ROHMUSDC/LapisDevBoard/Starting Software - PC GUI and MCU Default Code/LAPISDevKit - Q112 - Default Firmware (Release)/_output/_obj/main.asm

;; Compile Options : /TML610112 /MS /near /Icommon /Imain /Iirq /Itimer /Iclock /Itbc /Iuart /Ii2c /SS 256 /SD /Oa /Ot /W 3 /Wc /Fa_output\_obj\ 
;; Version Number  : Ver.3.31.4
;; File Name       : main.c

	type (ML610112) 
	model small, near
	$$NVARmain segment data 2h #0h
	$$NINITVAR segment data 2h #0h
	$$NINITTAB segment table 2h any
	$$Initialization$main segment code 2h #0h
	$$NOP1000$main segment code 2h #0h
	$$PinB0_PWM$main segment code 2h #0h
	$$PortA_Digital_Inputs$main segment code 2h #0h
	$$PortA_Low$main segment code 2h #0h
	$$PortB_Low$main segment code 2h #0h
	$$PortC_Low$main segment code 2h #0h
	$$PortD_Low$main segment code 2h #0h
	$$SetOSC$main segment code 2h #0h
	$$TAB_uartSetParam$main segment table 2h #0h
	$$_funcI2CFin$main segment code 2h #0h
	$$_funcUartFin$main segment code 2h #0h
	$$_intI2c$main segment code 2h #0h
	$$_intUart$main segment code 2h #0h
	$$analog_comparator$main segment code 2h #0h
	$$checkI2C$main segment code 2h #0h
	$$main$main segment code 2h #0h
	$$main_clrWDT$main segment code 2h #0h
	$$main_reqNotHalt$main segment code 2h #0h
	STACKSEG 0100h
CVERSION 3.31.4
CGLOBAL 01H 03H 0000H "checkI2C" 08H 02H 88H 00H 81H 02H 00H 00H 07H
CGLOBAL 01H 03H 0000H "main_clrWDT" 08H 02H 7CH 00H 80H 00H 00H 00H 07H
CSGLOBAL 03H 0000H "_funcUartFin" 08H 02H 86H 00H 81H 02H 00H 00H 07H
CGLOBAL 01H 03H 0000H "main_reqNotHalt" 08H 02H 89H 00H 80H 00H 00H 00H 07H
CSGLOBAL 03H 0000H "Initialization" 08H 02H 7DH 00H 81H 04H 00H 00H 07H
CGLOBAL 01H 03H 0000H "PortA_Digital_Inputs" 08H 02H 84H 00H 80H 00H 00H 00H 07H
CGLOBAL 01H 03H 0000H "main" 08H 02H 8DH 00H 80H 08H 00H 00H 01H
CSGLOBAL 03H 0000H "_intUart" 08H 02H 8AH 00H 80H 00H 00H 00H 07H
CGLOBAL 01H 03H 0000H "PortD_Low" 08H 02H 83H 00H 80H 00H 00H 00H 07H
CGLOBAL 01H 03H 0000H "NOP1000" 08H 02H 8CH 00H 80H 00H 00H 00H 07H
CSGLOBAL 03H 0000H "_intI2c" 08H 02H 8BH 00H 81H 02H 00H 00H 07H
CSGLOBAL 03H 0000H "SetOSC" 08H 02H 7EH 00H 80H 00H 00H 00H 07H
CGLOBAL 01H 03H 0000H "PortC_Low" 08H 02H 82H 00H 80H 00H 00H 00H 07H
CGLOBAL 01H 03H 0000H "PortB_Low" 08H 02H 81H 00H 80H 00H 00H 00H 07H
CGLOBAL 01H 03H 0000H "PortA_Low" 08H 02H 80H 00H 80H 00H 00H 00H 07H
CGLOBAL 01H 03H 0000H "analog_comparator" 08H 02H 7FH 00H 80H 00H 00H 00H 07H
CSGLOBAL 03H 0000H "_funcI2CFin" 08H 02H 87H 00H 81H 02H 00H 00H 07H
CGLOBAL 01H 03H 0000H "PinB0_PWM" 08H 02H 85H 00H 80H 00H 00H 00H 07H
CSTRUCTTAG 0000H 0000H 0006H 0003H 00000001H "_Notag"
CSTRUCTMEM 52H 00000001H 00000000H "state" 02H 00H 00H
CSTRUCTMEM 52H 00000002H 00000001H "state_sub" 02H 00H 00H
CSTRUCTMEM 52H 00000005H 00000003H "reserve" 02H 00H 00H
CSTRUCTTAG 0000H 0000H 0005H 000CH 00000016H "_Notag"
CSTRUCTMEM 42H 00000002H 00000000H "_Mode" 02H 00H 08H
CSTRUCTMEM 43H 00000002H 00000002H "_Handle" 02H 00H 08H
CSTRUCTMEM 42H 00000002H 00000004H "_Buf" 04H 03H 00H 00H 00H
CSTRUCTMEM 42H 00000002H 00000006H "_Bend" 04H 03H 00H 00H 00H
CSTRUCTMEM 42H 00000002H 00000008H "_Next" 04H 03H 00H 00H 00H
CSTRUCTMEM 42H 00000002H 0000000AH "_Rend" 04H 03H 00H 00H 00H
CSTRUCTMEM 42H 00000002H 0000000CH "_Rsave" 04H 03H 00H 00H 00H
CSTRUCTMEM 42H 00000002H 0000000EH "_Wend" 04H 03H 00H 00H 00H
CSTRUCTMEM 42H 00000002H 00000010H "_Back" 05H 01H 02H 00H 00H 00H
CSTRUCTMEM 42H 00000001H 00000012H "_Cbuf" 02H 00H 00H
CSTRUCTMEM 42H 00000001H 00000013H "_Nback" 02H 00H 00H
CSTRUCTMEM 43H 00000002H 00000014H "_Tmpnam" 04H 03H 00H 00H 00H
CSTRUCTTAG 0000H 0000H 0004H 0001H 00000004H "_Notag"
CSTRUCTMEM 42H 00000004H 00000000H "_Off" 02H 00H 02H
CSTRUCTTAG 0000H 0000H 0003H 0006H 0000000AH "_Notag"
CSTRUCTMEM 42H 00000004H 00000000H "br" 02H 00H 02H
CSTRUCTMEM 42H 00000001H 00000004H "lg" 02H 00H 00H
CSTRUCTMEM 42H 00000001H 00000005H "pt" 02H 00H 00H
CSTRUCTMEM 42H 00000001H 00000006H "stp" 02H 00H 00H
CSTRUCTMEM 42H 00000001H 00000007H "neg" 02H 00H 00H
CSTRUCTMEM 42H 00000001H 00000008H "dir" 02H 00H 00H
CSTRUCTTAG 0000H 0000H 0002H 0002H 00000008H "_Notag"
CSTRUCTMEM 43H 00000004H 00000000H "quot" 02H 00H 02H
CSTRUCTMEM 43H 00000004H 00000004H "rem" 02H 00H 02H
CSTRUCTTAG 0000H 0000H 0001H 0002H 00000004H "_Notag"
CSTRUCTMEM 43H 00000002H 00000000H "quot" 02H 00H 01H
CSTRUCTMEM 43H 00000002H 00000002H "rem" 02H 00H 01H
CSTRUCTTAG 0000H 0000H 0000H 0008H 00000001H "_Notag"
CSTRUCTMEM 52H 00000001H 00000000H "b0" 02H 00H 00H
CSTRUCTMEM 52H 00000001H 00000001H "b1" 02H 00H 00H
CSTRUCTMEM 52H 00000001H 00000002H "b2" 02H 00H 00H
CSTRUCTMEM 52H 00000001H 00000003H "b3" 02H 00H 00H
CSTRUCTMEM 52H 00000001H 00000004H "b4" 02H 00H 00H
CSTRUCTMEM 52H 00000001H 00000005H "b5" 02H 00H 00H
CSTRUCTMEM 52H 00000001H 00000006H "b6" 02H 00H 00H
CSTRUCTMEM 52H 00000001H 00000007H "b7" 02H 00H 00H
CTYPEDEF 0000H 0000H 43H "_Ptrdifft" 02H 00H 01H
CTYPEDEF 0000H 0000H 42H "_Sizet" 02H 00H 01H
CTYPEDEF 0000H 0000H 43H "tUartSetParam" 04H 00H 05H 03H 00H
CTYPEDEF 0000H 0000H 42H "size_t" 02H 00H 01H
CTYPEDEF 0000H 0000H 43H "cbfUart" 0AH 03H 00H 02H 2EH 00H 00H 00H 00H 00H 07H
CTYPEDEF 0000H 0000H 43H "fpos_t" 04H 00H 05H 04H 00H
CTYPEDEF 0000H 0000H 43H "STRUCT_STATE" 04H 00H 05H 06H 00H
CTYPEDEF 0000H 0000H 43H "cbfI2c" 0AH 03H 00H 02H 43H 00H 00H 00H 00H 00H 07H
CTYPEDEF 0000H 0000H 03H "_Cmpfun_nf" 08H 02H 01H 00H 00H 00H 00H 00H 01H
CTYPEDEF 0000H 0000H 03H "_Cmpfun_nn" 08H 02H 00H 00H 00H 00H 00H 00H 01H
CTYPEDEF 0000H 0000H 03H "_Cmpfun_ff" 08H 02H 03H 00H 00H 00H 00H 00H 01H
CTYPEDEF 0000H 0000H 03H "_Cmpfun_fn" 08H 02H 02H 00H 00H 00H 00H 00H 01H
CTYPEDEF 0000H 0000H 43H "FILE" 04H 00H 05H 05H 00H
CTYPEDEF 0000H 0000H 43H "div_t" 04H 00H 05H 01H 00H
CTYPEDEF 0000H 0000H 43H "ldiv_t" 04H 00H 05H 02H 00H
CTYPEDEF 0000H 0000H 43H "_BYTE_FIELD" 04H 00H 05H 00H 00H
CGLOBAL 00H 42H 0015H "RecWorld" 05H 01H 15H 00H 00H 00H
CGLOBAL 00H 42H 0001H "_flgUartFin" 02H 00H 00H
CGLOBAL 01H 42H 003EH "NackMCUConn" 05H 01H 3EH 00H 00H 00H
CSGLOBAL 42H 002EH "I2C_BUFF" 05H 01H 2EH 00H 00H 00H
CSGLOBAL 42H 0001H "I2CNumBytes" 02H 00H 00H
CSGLOBAL 42H 0001H "Data2Str_temp" 02H 00H 00H
CSGLOBAL 42H 0001H "RegAddr_temp" 02H 00H 00H
CSGLOBAL 42H 0001H "Data3Str_temp" 02H 00H 00H
CGLOBAL 00H 42H 0002H "testI2C" 02H 00H 01H
CGLOBAL 00H 42H 0002H "ret" 02H 00H 01H
CSGLOBAL 42H 0008H "I2CReceInfo" 05H 01H 08H 00H 00H 00H
CSGLOBAL 42H 0001H "Data0Str_temp" 02H 00H 00H
CSGLOBAL 42H 0001H "Data1Str_temp" 02H 00H 00H
CSGLOBAL 42H 0001H "Data4Str_temp" 02H 00H 00H
CSGLOBAL 42H 0001H "Data5Str_temp" 02H 00H 00H
CGLOBAL 00H 42H 0002H "UART_VAR" 02H 00H 01H
CSGLOBAL 42H 0001H "Data6Str_temp" 02H 00H 00H
CSGLOBAL 42H 0001H "Data7Str_temp" 02H 00H 00H
CGLOBAL 01H 42H 0016H "AckMCUConn" 05H 01H 16H 00H 00H 00H
CGLOBAL 01H 42H 000EH "InputRec" 05H 01H 0EH 00H 00H 00H
CSGLOBAL 42H 0001H "I2CNumBytes_temp" 02H 00H 00H
CSGLOBAL 01H 000AH "_uartSetParam" 04H 00H 05H 03H 00H
CSGLOBAL 42H 0001H "Data2Str" 02H 00H 00H
CSGLOBAL 42H 0001H "Data3Str" 02H 00H 00H
CSGLOBAL 42H 0001H "RegAddr" 02H 00H 00H
CGLOBAL 01H 42H 0017H "I2C_RX_Data" 05H 01H 17H 00H 00H 00H
CGLOBAL 01H 42H 0016H "ListFWRev" 05H 01H 16H 00H 00H 00H
CSGLOBAL 42H 0001H "Data0Str" 02H 00H 00H
CSGLOBAL 42H 0001H "Data1Str" 02H 00H 00H
CGLOBAL 01H 42H 0017H "OutputRec" 05H 01H 17H 00H 00H 00H
CSGLOBAL 42H 0001H "I2CAdd" 02H 00H 00H
CSGLOBAL 42H 0001H "chari" 02H 00H 00H
CSGLOBAL 42H 0001H "charj" 02H 00H 00H
CSGLOBAL 42H 0001H "chark" 02H 00H 00H
CGLOBAL 01H 42H 000EH "HelloWorld" 05H 01H 0EH 00H 00H 00H
CGLOBAL 00H 42H 0001H "_flgI2CFin" 02H 00H 00H
CGLOBAL 00H 42H 0001H "_reqNotHalt" 02H 00H 00H
CSGLOBAL 42H 0001H "Data6Str" 02H 00H 00H
CGLOBAL 01H 42H 0017H "InputStatus" 05H 01H 17H 00H 00H 00H
CSGLOBAL 42H 0008H "I2CSendInfo" 05H 01H 08H 00H 00H 00H
CSGLOBAL 42H 0001H "Data7Str" 02H 00H 00H
CSGLOBAL 42H 0001H "Data4Str" 02H 00H 00H
CSGLOBAL 42H 0001H "Data5Str" 02H 00H 00H
CGLOBAL 01H 42H 0015H "I2C_RX_REC" 05H 01H 15H 00H 00H 00H
CGLOBAL 01H 42H 0015H "I2C_TX_REC" 05H 01H 15H 00H 00H 00H
CSGLOBAL 42H 0001H "I2CAdd_temp" 02H 00H 00H
CFILE 0001H 0000085AH "main\\ML610112.H"
CFILE 0002H 000000D8H "main\\stdlib.h"
CFILE 0003H 0000007AH "main\\yvals.h"
CFILE 0004H 0000006BH "uart\\uart.h"
CFILE 0005H 00000027H "common\\common.h"
CFILE 0006H 00000057H "irq\\irq.h"
CFILE 0007H 00000023H "main\\mcu.h"
CFILE 0008H 00000045H "i2c\\i2c.h"
CFILE 0009H 000000EEH "main\\stdio.h"
CFILE 0000H 00000674H "main\\main.c"

	rseg $$main$main
CFUNCTION 141

_main	:
CBLOCK 141 1 240

;;{
CLINEA 0000H 0001H 00F0H 0001H 0001H
CBLOCK 141 2 240
CLOCAL 4BH 0001H 0000H 0002H "char_a" 02H 00H 00H
CLOCAL 4AH 0001H 0000H 0002H "uchar" 02H 00H 00H
CLOCAL 4BH 0002H 0000H 0002H "inta" 02H 00H 01H
CLOCAL 4BH 00C8H 0000H 0002H "table" 05H 01H 64H 00H 00H 01H
CLOCAL 4AH 0002H 0000H 0002H "uint" 02H 00H 01H
CLOCAL 4BH 0004H 0000H 0002H "long_a" 02H 00H 02H
CLOCAL 4BH 0004H 0000H 0002H "delay" 02H 00H 02H
CLOCAL 4BH 0004H 0000H 0002H "float_a" 02H 00H 03H
CLOCAL 4BH 0008H 0000H 0002H "double_a" 02H 00H 04H
CLOCAL 4AH 0001H 0000H 0002H "button_flag" 02H 00H 00H
CLOCAL 47H 0002H 0024H 0002H "i" 02H 00H 01H
CLOCAL 4BH 0002H 0000H 0002H "j" 02H 00H 01H
CLOCAL 4BH 0002H 0000H 0002H "k" 02H 00H 01H
CLOCAL 4BH 0002H 0000H 0002H "x" 02H 00H 01H
CLOCAL 4BH 0002H 0000H 0002H "y" 02H 00H 01H
CLOCAL 4AH 0001H 0000H 0002H "sndByte" 02H 00H 00H
CLOCAL 46H 0002H 0026H 0002H "count" 02H 00H 01H
CLOCAL 4BH 0001H 0000H 0002H "maskC" 02H 00H 00H

;;	Initialization(); //Ports, UART, Timers, Oscillator, Comparators, etc.
CLINEA 0000H 0001H 0103H 0002H 0047H
	bl	_Initialization

;;RX_Loop:	
CLINEA 0000H 0001H 0105H 0001H 0009H
CLABEL 000CH "RX_Loop"
_$L12 :

;;		main_clrWDT();
CLINEA 0000H 0001H 0106H 0003H 0010H
	bl	_main_clrWDT

;;		for (i=0;i<22;i++)
CLINEA 0000H 0001H 0109H 0003H 0014H
	mov	er0,	#0 
_$L15 :
CBLOCK 141 3 266

;;			RecWorld[i] = 0;	
CLINEA 0000H 0001H 010BH 0004H 0014H
	mov	r2,	#00h
	st	r2,	NEAR _RecWorld[er0]
CBLOCKEND 141 3 268

;;		for (i=0;i<22;i++)
CLINEA 0000H 0000H 0109H 0003H 0014H
	add	er0,	#1 
	cmp	r0,	#016h
	cmpc	r1,	#00h
	blts	_$L15

;;		_flgUartFin = 0;
CLINEA 0000H 0001H 010FH 0003H 0012H
	mov	r0,	#00h
	st	r0,	NEAR __flgUartFin

;;		uart_stop();
CLINEA 0000H 0001H 0110H 0003H 000EH
	bl	_uart_stop

;;		uart_startReceive(RecWorld, 21, _funcUartFin);
CLINEA 0000H 0001H 0111H 0003H 0030H
	mov	r0,	#BYTE1 OFFSET __funcUartFin
	mov	r1,	#BYTE2 OFFSET __funcUartFin
	push	er0
	mov	er2,	#21
	mov	r0,	#BYTE1 OFFSET _RecWorld
	mov	r1,	#BYTE2 OFFSET _RecWorld
	bl	_uart_startReceive
	add	sp,	#2 

;;		while(_flgUartFin != 1){
CLINEA 0000H 0000H 0112H 0001H 000BH
	bal	_$L480

;;		while(_flgUartFin != 1){
CLINEA 0000H 0000H 0112H 0003H 001AH
_$L21 :
CBLOCK 141 4 274

;;			NOP1000();
CLINEA 0000H 0001H 0113H 0004H 000DH
	bl	_NOP1000

;;			main_clrWDT();
CLINEA 0000H 0001H 0114H 0004H 0011H
	bl	_main_clrWDT
CBLOCKEND 141 4 277

;;		while(_flgUartFin != 1){
CLINEA 0000H 0000H 0112H 0001H 000BH
_$L480 :
	l	r0,	NEAR __flgUartFin
	cmp	r0,	#01h
	bne	_$L21

;;		if(RecWorld[0] == 0x41){			//if RECWORLD == "ACK2"
CLINEA 0000H 0001H 011AH 0003H 0034H
	l	r0,	NEAR _RecWorld
	cmp	r0,	#041h
	beq	_$M97
	b	_$L41
_$M97 :
CBLOCK 141 5 282

;;			if(RecWorld[1] == 0x43){
CLINEA 0000H 0001H 011BH 0004H 001BH
	l	r0,	NEAR _RecWorld+01h
	cmp	r0,	#043h
	beq	_$M98
	b	_$L41
_$M98 :
CBLOCK 141 6 283

;;				if(RecWorld[2] == 0x4B){
CLINEA 0000H 0001H 011CH 0005H 001CH
	l	r0,	NEAR _RecWorld+02h
	cmp	r0,	#04bh
	beq	_$M99
	b	_$L41
_$M99 :
CBLOCK 141 7 284
	mov	r0,	#00h
	st	r0,	NEAR __flgUartFin

;;					if(RecWorld[3] == 0x32){
CLINEA 0000H 0001H 011DH 0006H 001DH
	l	r0,	NEAR _RecWorld+03h
	cmp	r0,	#032h
	bne	_$L29
CBLOCK 141 8 285

;;						uart_stop();
CLINEA 0000H 0001H 011FH 0007H 0012H
	bl	_uart_stop

;;						uart_startSend(AckMCUConn, 22, _funcUartFin);
CLINEA 0000H 0001H 0120H 0007H 0033H
	mov	r0,	#BYTE1 OFFSET __funcUartFin
	mov	r1,	#BYTE2 OFFSET __funcUartFin
	push	er0
	mov	er2,	#22
	mov	r0,	#BYTE1 OFFSET _AckMCUConn
	mov	r1,	#BYTE2 OFFSET _AckMCUConn
	bl	_uart_startSend
	add	sp,	#2 

;;						while(_flgUartFin != 1){
CLINEA 0000H 0000H 0121H 0001H 000BH
	bal	_$L481

;;						while(_flgUartFin != 1){
CLINEA 0000H 0000H 0121H 0007H 001EH
_$L33 :
CBLOCK 141 9 289

;;							NOP1000();
CLINEA 0000H 0001H 0122H 0008H 0011H
	bl	_NOP1000

;;							main_clrWDT();
CLINEA 0000H 0001H 0123H 0008H 0015H
	bl	_main_clrWDT
CBLOCKEND 141 9 292

;;						while(_flgUartFin != 1){
CLINEA 0000H 0000H 0121H 0001H 000BH
_$L481 :
	l	r0,	NEAR __flgUartFin
	cmp	r0,	#01h
	bne	_$L33

;;						_flgUartFin = 0;
CLINEA 0000H 0001H 0125H 0007H 0016H
	mov	r0,	#00h
	st	r0,	NEAR __flgUartFin

;;						uart_stop();
CLINEA 0000H 0001H 0126H 0007H 0012H
	bl	_uart_stop

;;						uart_startSend(ListFWRev, 22, _funcUartFin);
CLINEA 0000H 0001H 0127H 0007H 0032H
	mov	r0,	#BYTE1 OFFSET __funcUartFin
	mov	r1,	#BYTE2 OFFSET __funcUartFin
	push	er0
	mov	er2,	#22
	mov	r0,	#BYTE1 OFFSET _ListFWRev
	mov	r1,	#BYTE2 OFFSET _ListFWRev
	bl	_uart_startSend
	add	sp,	#2 

;;						while(_flgUartFin != 1){
CLINEA 0000H 0000H 0128H 0001H 000BH
	bal	_$L482

;;						while(_flgUartFin != 1){
CLINEA 0000H 0000H 0128H 0007H 001EH
_$L37 :
CBLOCK 141 10 296

;;							NOP1000();
CLINEA 0000H 0001H 0129H 0008H 0011H
	bl	_NOP1000

;;							main_clrWDT();
CLINEA 0000H 0001H 012AH 0008H 0015H
	bl	_main_clrWDT
CBLOCKEND 141 10 299

;;						while(_flgUartFin != 1){
CLINEA 0000H 0000H 0128H 0001H 000BH
_$L482 :
	l	r0,	NEAR __flgUartFin
	cmp	r0,	#01h
	bne	_$L37

;;					else
CLINEA 0000H 0001H 012DH 0006H 0009H
	bal	_$L41
_$L29 :
CBLOCK 141 11 302

;;						uart_stop();
CLINEA 0000H 0001H 0130H 0007H 0012H
	bl	_uart_stop

;;						uart_startSend(NackMCUConn, 62, _funcUartFin);
CLINEA 0000H 0001H 0131H 0007H 0034H
	mov	r0,	#BYTE1 OFFSET __funcUartFin
	mov	r1,	#BYTE2 OFFSET __funcUartFin
	push	er0
	mov	er2,	#62
	mov	r0,	#BYTE1 OFFSET _NackMCUConn
	mov	r1,	#BYTE2 OFFSET _NackMCUConn
	bl	_uart_startSend
	add	sp,	#2 

;;						while(_flgUartFin != 1){
CLINEA 0000H 0000H 0132H 0001H 000BH
	bal	_$L483

;;						while(_flgUartFin != 1){
CLINEA 0000H 0000H 0132H 0007H 001EH
_$L42 :
CBLOCK 141 12 306

;;							NOP1000();
CLINEA 0000H 0001H 0133H 0008H 0011H
	bl	_NOP1000

;;							main_clrWDT();
CLINEA 0000H 0001H 0134H 0008H 0015H
	bl	_main_clrWDT
CBLOCKEND 141 12 309

;;						while(_flgUartFin != 1){
CLINEA 0000H 0000H 0132H 0001H 000BH
_$L483 :
	l	r0,	NEAR __flgUartFin
	cmp	r0,	#01h
	bne	_$L42

;;						}
CLINEA 0000H 0000H 0135H 0007H 0007H
_$L41 :
CBLOCKEND 141 11 311
CBLOCKEND 141 7 312
CBLOCKEND 141 8 989
CBLOCKEND 141 6 313
CBLOCKEND 141 5 314

;;		if(RecWorld[0] == 0x49){			//if RECWORLD == "INC"
CLINEA 0000H 0001H 013EH 0003H 0033H
	l	r0,	NEAR _RecWorld
	cmp	r0,	#049h
	beq	_$M100
	b	_$L71
_$M100 :
CBLOCK 141 13 318

;;			if(RecWorld[1] == 0x4E){
CLINEA 0000H 0001H 013FH 0004H 001BH
	l	r0,	NEAR _RecWorld+01h
	cmp	r0,	#04eh
	beq	_$M101
	b	_$L71
_$M101 :
CBLOCK 141 14 319

;;				if(RecWorld[2] == 0x43){
CLINEA 0000H 0001H 0140H 0005H 001CH
	l	r0,	NEAR _RecWorld+02h
	cmp	r0,	#043h
	beq	_$M102
	b	_$L71
_$M102 :
CBLOCK 141 15 320

;;					InputStatus[2] = 0x43;
CLINEA 0000H 0001H 0141H 0006H 001BH
	mov	r0,	#043h
	st	r0,	NEAR _InputStatus+02h

;;					InputRec[2] = 0x43;
CLINEA 0000H 0001H 0142H 0006H 0018H
	st	r0,	NEAR _InputRec+02h

;;					for(count = 4; count < 12; count++)
CLINEA 0000H 0001H 0143H 0006H 0028H
	mov	er4,	#4 
_$L52 :
CBLOCK 141 16 324

;;						RecWorld[count] -= 0x30;
CLINEA 0000H 0001H 0145H 0007H 001EH
	l	r2,	NEAR _RecWorld[er4]
	add	r2,	#0d0h
	st	r2,	NEAR _RecWorld[er4]

;;						if(RecWorld[count] != (0x01||0x00)){
CLINEA 0000H 0001H 0146H 0007H 002AH
	mov	r0,	r2
	cmp	r0,	#01h
	beq	_$L64
CBLOCK 141 17 326

;;							RecWorld[count] = 0;
CLINEA 0000H 0001H 0147H 0008H 001BH
	mov	r2,	#00h
	st	r2,	NEAR _RecWorld[er4]
CBLOCKEND 141 17 328

;;						}
CLINEA 0000H 0000H 0148H 0007H 0007H
_$L64 :
CBLOCKEND 141 16 329

;;					for(count = 4; count < 12; count++)
CLINEA 0000H 0000H 0143H 0006H 0028H
	add	er4,	#1 
	cmp	r4,	#0ch
	cmpc	r5,	#00h
	blt	_$L52

;;					PC7DIR = RecWorld[4];
CLINEA 0000H 0001H 014CH 0006H 001AH
	l	r0,	NEAR _RecWorld+04h
	and	r0,	#01h
	beq	_$M1
	sb	0f261h.7
	bal	_$M2
_$M1 :
	rb	0f261h.7
_$M2 :

;;					PC6DIR = RecWorld[5];
CLINEA 0000H 0001H 014DH 0006H 001AH
	l	r0,	NEAR _RecWorld+05h
	and	r0,	#01h
	beq	_$M3
	sb	0f261h.6
	bal	_$M4
_$M3 :
	rb	0f261h.6
_$M4 :

;;					PC5DIR = RecWorld[6];
CLINEA 0000H 0001H 014EH 0006H 001AH
	l	r0,	NEAR _RecWorld+06h
	and	r0,	#01h
	beq	_$M5
	sb	0f261h.5
	bal	_$M6
_$M5 :
	rb	0f261h.5
_$M6 :

;;					PC4DIR = RecWorld[7];
CLINEA 0000H 0001H 014FH 0006H 001AH
	l	r0,	NEAR _RecWorld+07h
	and	r0,	#01h
	beq	_$M7
	sb	0f261h.4
	bal	_$M8
_$M7 :
	rb	0f261h.4
_$M8 :

;;					PC3DIR = RecWorld[8];
CLINEA 0000H 0001H 0150H 0006H 001AH
	l	r0,	NEAR _RecWorld+08h
	and	r0,	#01h
	beq	_$M9
	sb	0f261h.3
	bal	_$M10
_$M9 :
	rb	0f261h.3
_$M10 :

;;					PC2DIR = RecWorld[9];
CLINEA 0000H 0001H 0151H 0006H 001AH
	l	r0,	NEAR _RecWorld+09h
	and	r0,	#01h
	beq	_$M11
	sb	0f261h.2
	bal	_$M12
_$M11 :
	rb	0f261h.2
_$M12 :

;;					PC1DIR = RecWorld[10];
CLINEA 0000H 0001H 0152H 0006H 001BH
	l	r0,	NEAR _RecWorld+0ah
	and	r0,	#01h
	beq	_$M13
	sb	0f261h.1
	bal	_$M14
_$M13 :
	rb	0f261h.1
_$M14 :

;;					PC0DIR = RecWorld[11];
CLINEA 0000H 0001H 0153H 0006H 001BH
	l	r0,	NEAR _RecWorld+0bh
	and	r0,	#01h
	beq	_$M15
	sb	0f261h.0
	bal	_$M16
_$M15 :
	rb	0f261h.0
_$M16 :

;;					InputStatus[4] = PC7DIR + 0x30;
CLINEA 0000H 0001H 0156H 0006H 0024H
	l	r0,	0f261h
	srl	r0,	#07h
	and	r0,	#01h
	add	r0,	#030h
	st	r0,	NEAR _InputStatus+04h

;;					InputStatus[5] = PC6DIR + 0x30;
CLINEA 0000H 0001H 0157H 0006H 0024H
	l	r0,	0f261h
	srl	r0,	#06h
	and	r0,	#01h
	add	r0,	#030h
	st	r0,	NEAR _InputStatus+05h

;;					InputStatus[6] = PC5DIR + 0x30;
CLINEA 0000H 0001H 0158H 0006H 0024H
	l	r0,	0f261h
	srl	r0,	#05h
	and	r0,	#01h
	add	r0,	#030h
	st	r0,	NEAR _InputStatus+06h

;;					InputStatus[7] = PC4DIR + 0x30;
CLINEA 0000H 0001H 0159H 0006H 0024H
	l	r0,	0f261h
	srl	r0,	#04h
	and	r0,	#01h
	add	r0,	#030h
	st	r0,	NEAR _InputStatus+07h

;;					InputStatus[8] = PC3DIR + 0x30;
CLINEA 0000H 0001H 015AH 0006H 0024H
	l	r0,	0f261h
	srl	r0,	#03h
	and	r0,	#01h
	add	r0,	#030h
	st	r0,	NEAR _InputStatus+08h

;;					InputStatus[9] = PC2DIR + 0x30;
CLINEA 0000H 0001H 015BH 0006H 0024H
	l	r0,	0f261h
	srl	r0,	#02h
	and	r0,	#01h
	add	r0,	#030h
	st	r0,	NEAR _InputStatus+09h

;;					InputStatus[10] = PC1DIR + 0x30;
CLINEA 0000H 0001H 015CH 0006H 0025H
	l	r0,	0f261h
	srl	r0,	#01h
	and	r0,	#01h
	add	r0,	#030h
	st	r0,	NEAR _InputStatus+0ah

;;					InputStatus[11] = PC0DIR + 0x30;
CLINEA 0000H 0001H 015DH 0006H 0025H
	l	r0,	0f261h
	and	r0,	#01h
	add	r0,	#030h
	st	r0,	NEAR _InputStatus+0bh

;;					InputStatus[13] = PC7D + 0x30;
CLINEA 0000H 0001H 0160H 0006H 0023H
	l	r0,	0f260h
	srl	r0,	#07h
	and	r0,	#01h
	add	r0,	#030h
	st	r0,	NEAR _InputStatus+0dh

;;					InputStatus[14] = PC6D + 0x30;
CLINEA 0000H 0001H 0161H 0006H 0023H
	l	r0,	0f260h
	srl	r0,	#06h
	and	r0,	#01h
	add	r0,	#030h
	st	r0,	NEAR _InputStatus+0eh

;;					InputStatus[15] = PC5D + 0x30;
CLINEA 0000H 0001H 0162H 0006H 0023H
	l	r0,	0f260h
	srl	r0,	#05h
	and	r0,	#01h
	add	r0,	#030h
	st	r0,	NEAR _InputStatus+0fh

;;					InputStatus[16] = PC4D + 0x30;
CLINEA 0000H 0001H 0163H 0006H 0023H
	l	r0,	0f260h
	srl	r0,	#04h
	and	r0,	#01h
	add	r0,	#030h
	st	r0,	NEAR _InputStatus+010h

;;					InputStatus[17] = PC3D + 0x30;
CLINEA 0000H 0001H 0164H 0006H 0023H
	l	r0,	0f260h
	srl	r0,	#03h
	and	r0,	#01h
	add	r0,	#030h
	st	r0,	NEAR _InputStatus+011h

;;					InputStatus[18] = PC2D + 0x30;
CLINEA 0000H 0001H 0165H 0006H 0023H
	l	r0,	0f260h
	srl	r0,	#02h
	and	r0,	#01h
	add	r0,	#030h
	st	r0,	NEAR _InputStatus+012h

;;					InputStatus[19] = PC1D + 0x30;
CLINEA 0000H 0001H 0166H 0006H 0023H
	l	r0,	0f260h
	srl	r0,	#01h
	and	r0,	#01h
	add	r0,	#030h
	st	r0,	NEAR _InputStatus+013h

;;					InputStatus[20] = PC0D + 0x30;
CLINEA 0000H 0001H 0167H 0006H 0023H
	l	r0,	0f260h
	and	r0,	#01h
	add	r0,	#030h
	st	r0,	NEAR _InputStatus+014h

;;					_flgUartFin = 0;
CLINEA 0000H 0001H 016BH 0006H 0015H
	mov	r0,	#00h
	st	r0,	NEAR __flgUartFin

;;					uart_stop();
CLINEA 0000H 0001H 016CH 0006H 0011H
	bl	_uart_stop

;;					uart_startSend(InputStatus, 23, _funcUartFin);
CLINEA 0000H 0001H 016DH 0006H 0033H
	mov	r0,	#BYTE1 OFFSET __funcUartFin
	mov	r1,	#BYTE2 OFFSET __funcUartFin
	push	er0
	mov	er2,	#23
	mov	r0,	#BYTE1 OFFSET _InputStatus
	mov	r1,	#BYTE2 OFFSET _InputStatus
	bl	_uart_startSend
	add	sp,	#2 

;;					while(_flgUartFin != 1){
CLINEA 0000H 0000H 016EH 0001H 000BH
	bal	_$L484

;;					while(_flgUartFin != 1){
CLINEA 0000H 0000H 016EH 0006H 001DH
_$L68 :
CBLOCK 141 18 366

;;						NOP1000();
CLINEA 0000H 0001H 016FH 0007H 0010H
	bl	_NOP1000

;;						main_clrWDT();
CLINEA 0000H 0001H 0170H 0007H 0014H
	bl	_main_clrWDT
CBLOCKEND 141 18 369

;;					while(_flgUartFin != 1){
CLINEA 0000H 0000H 016EH 0001H 000BH
_$L484 :
	l	r0,	NEAR __flgUartFin
	cmp	r0,	#01h
	bne	_$L68

;;					_flgUartFin = 0;
CLINEA 0000H 0001H 0174H 0006H 0015H
	mov	r0,	#00h
	st	r0,	NEAR __flgUartFin

;;					uart_stop();
CLINEA 0000H 0001H 0175H 0006H 0011H
	bl	_uart_stop

;;					uart_startSend(InputRec, 14, _funcUartFin);
CLINEA 0000H 0001H 0176H 0006H 0030H
	mov	r0,	#BYTE1 OFFSET __funcUartFin
	mov	r1,	#BYTE2 OFFSET __funcUartFin
	push	er0
	mov	er2,	#14
	mov	r0,	#BYTE1 OFFSET _InputRec
	mov	r1,	#BYTE2 OFFSET _InputRec
	bl	_uart_startSend
	add	sp,	#2 

;;					while(_flgUartFin != 1){
CLINEA 0000H 0000H 0177H 0001H 000BH
	bal	_$L485

;;					while(_flgUartFin != 1){
CLINEA 0000H 0000H 0177H 0006H 001DH
_$L72 :
CBLOCK 141 19 375

;;						NOP1000();
CLINEA 0000H 0001H 0178H 0007H 0010H
	bl	_NOP1000

;;						main_clrWDT();
CLINEA 0000H 0001H 0179H 0007H 0014H
	bl	_main_clrWDT
CBLOCKEND 141 19 378

;;					while(_flgUartFin != 1){
CLINEA 0000H 0000H 0177H 0001H 000BH
_$L485 :
	l	r0,	NEAR __flgUartFin
	cmp	r0,	#01h
	bne	_$L72

;;					}
CLINEA 0000H 0000H 017AH 0006H 0006H
_$L71 :
CBLOCKEND 141 15 379
CBLOCKEND 141 14 380
CBLOCKEND 141 13 381

;;		if(RecWorld[0] == 0x4F){			//if RECWORLD == "OUC"
CLINEA 0000H 0001H 0181H 0003H 0033H
	l	r0,	NEAR _RecWorld
	cmp	r0,	#04fh
	beq	_$M103
	b	_$L97
_$M103 :
CBLOCK 141 20 385

;;			if(RecWorld[1] == 0x55){
CLINEA 0000H 0001H 0182H 0004H 001BH
	l	r0,	NEAR _RecWorld+01h
	cmp	r0,	#055h
	beq	_$M104
	b	_$L97
_$M104 :
CBLOCK 141 21 386

;;				if(RecWorld[2] == 0x43){
CLINEA 0000H 0001H 0183H 0005H 001CH
	l	r0,	NEAR _RecWorld+02h
	cmp	r0,	#043h
	beq	_$M105
	b	_$L97
_$M105 :
CBLOCK 141 22 387

;;					OutputRec[2] = 0x43;
CLINEA 0000H 0001H 0184H 0006H 0019H
	mov	r0,	#043h
	st	r0,	NEAR _OutputRec+02h

;;					for(count = 4; count < 21; count++)
CLINEA 0000H 0001H 0185H 0006H 0028H
	mov	er4,	#4 
_$L82 :
CBLOCK 141 23 390

;;						RecWorld[count] -= 0x30;
CLINEA 0000H 0001H 0187H 0007H 001EH
	l	r2,	NEAR _RecWorld[er4]
	add	r2,	#0d0h
	st	r2,	NEAR _RecWorld[er4]

;;						if(RecWorld[count] != (0x01||0x00)){
CLINEA 0000H 0001H 0188H 0007H 002AH
	mov	r0,	r2
	cmp	r0,	#01h
	beq	_$L94
CBLOCK 141 24 392

;;							RecWorld[count] = 0;
CLINEA 0000H 0001H 0189H 0008H 001BH
	mov	r2,	#00h
	st	r2,	NEAR _RecWorld[er4]
CBLOCKEND 141 24 394

;;						}
CLINEA 0000H 0000H 018AH 0007H 0007H
_$L94 :
CBLOCKEND 141 23 395

;;					for(count = 4; count < 21; count++)
CLINEA 0000H 0000H 0185H 0006H 0028H
	add	er4,	#1 
	cmp	r4,	#015h
	cmpc	r5,	#00h
	blt	_$L82

;;					PC7DIR = RecWorld[4];
CLINEA 0000H 0001H 018DH 0006H 001AH
	l	r0,	NEAR _RecWorld+04h
	and	r0,	#01h
	beq	_$M17
	sb	0f261h.7
	bal	_$M18
_$M17 :
	rb	0f261h.7
_$M18 :

;;					PC6DIR = RecWorld[5];
CLINEA 0000H 0001H 018EH 0006H 001AH
	l	r0,	NEAR _RecWorld+05h
	and	r0,	#01h
	beq	_$M19
	sb	0f261h.6
	bal	_$M20
_$M19 :
	rb	0f261h.6
_$M20 :

;;					PC5DIR = RecWorld[6];
CLINEA 0000H 0001H 018FH 0006H 001AH
	l	r0,	NEAR _RecWorld+06h
	and	r0,	#01h
	beq	_$M21
	sb	0f261h.5
	bal	_$M22
_$M21 :
	rb	0f261h.5
_$M22 :

;;					PC4DIR = RecWorld[7];
CLINEA 0000H 0001H 0190H 0006H 001AH
	l	r0,	NEAR _RecWorld+07h
	and	r0,	#01h
	beq	_$M23
	sb	0f261h.4
	bal	_$M24
_$M23 :
	rb	0f261h.4
_$M24 :

;;					PC3DIR = RecWorld[8];
CLINEA 0000H 0001H 0191H 0006H 001AH
	l	r0,	NEAR _RecWorld+08h
	and	r0,	#01h
	beq	_$M25
	sb	0f261h.3
	bal	_$M26
_$M25 :
	rb	0f261h.3
_$M26 :

;;					PC2DIR = RecWorld[9];
CLINEA 0000H 0001H 0192H 0006H 001AH
	l	r0,	NEAR _RecWorld+09h
	and	r0,	#01h
	beq	_$M27
	sb	0f261h.2
	bal	_$M28
_$M27 :
	rb	0f261h.2
_$M28 :

;;					PC1DIR = RecWorld[10];
CLINEA 0000H 0001H 0193H 0006H 001BH
	l	r0,	NEAR _RecWorld+0ah
	and	r0,	#01h
	beq	_$M29
	sb	0f261h.1
	bal	_$M30
_$M29 :
	rb	0f261h.1
_$M30 :

;;					PC0DIR = RecWorld[11];
CLINEA 0000H 0001H 0194H 0006H 001BH
	l	r0,	NEAR _RecWorld+0bh
	and	r0,	#01h
	beq	_$M31
	sb	0f261h.0
	bal	_$M32
_$M31 :
	rb	0f261h.0
_$M32 :

;;					PC7D = RecWorld[13];
CLINEA 0000H 0001H 0197H 0006H 0019H
	l	r0,	NEAR _RecWorld+0dh
	and	r0,	#01h
	beq	_$M33
	sb	0f260h.7
	bal	_$M34
_$M33 :
	rb	0f260h.7
_$M34 :

;;					PC6D = RecWorld[14];
CLINEA 0000H 0001H 0198H 0006H 0019H
	l	r0,	NEAR _RecWorld+0eh
	and	r0,	#01h
	beq	_$M35
	sb	0f260h.6
	bal	_$M36
_$M35 :
	rb	0f260h.6
_$M36 :

;;					PC5D = RecWorld[15];
CLINEA 0000H 0001H 0199H 0006H 0019H
	l	r0,	NEAR _RecWorld+0fh
	and	r0,	#01h
	beq	_$M37
	sb	0f260h.5
	bal	_$M38
_$M37 :
	rb	0f260h.5
_$M38 :

;;					PC4D = RecWorld[16];
CLINEA 0000H 0001H 019AH 0006H 0019H
	l	r0,	NEAR _RecWorld+010h
	and	r0,	#01h
	beq	_$M39
	sb	0f260h.4
	bal	_$M40
_$M39 :
	rb	0f260h.4
_$M40 :

;;					PC3D = RecWorld[17];
CLINEA 0000H 0001H 019BH 0006H 0019H
	l	r0,	NEAR _RecWorld+011h
	and	r0,	#01h
	beq	_$M41
	sb	0f260h.3
	bal	_$M42
_$M41 :
	rb	0f260h.3
_$M42 :

;;					PC2D = RecWorld[18];
CLINEA 0000H 0001H 019CH 0006H 0019H
	l	r0,	NEAR _RecWorld+012h
	and	r0,	#01h
	beq	_$M43
	sb	0f260h.2
	bal	_$M44
_$M43 :
	rb	0f260h.2
_$M44 :

;;					PC1D = RecWorld[19];
CLINEA 0000H 0001H 019DH 0006H 0019H
	l	r0,	NEAR _RecWorld+013h
	and	r0,	#01h
	beq	_$M45
	sb	0f260h.1
	bal	_$M46
_$M45 :
	rb	0f260h.1
_$M46 :

;;					PC0D = RecWorld[20];
CLINEA 0000H 0001H 019EH 0006H 0019H
	l	r0,	NEAR _RecWorld+014h
	and	r0,	#01h
	beq	_$M47
	sb	0f260h.0
	bal	_$M48
_$M47 :
	rb	0f260h.0
_$M48 :

;;					OutputRec[13] = PC7D + 0x30;
CLINEA 0000H 0001H 01A1H 0006H 0021H
	l	r0,	0f260h
	srl	r0,	#07h
	and	r0,	#01h
	add	r0,	#030h
	st	r0,	NEAR _OutputRec+0dh

;;					OutputRec[14] = PC6D + 0x30;
CLINEA 0000H 0001H 01A2H 0006H 0021H
	l	r0,	0f260h
	srl	r0,	#06h
	and	r0,	#01h
	add	r0,	#030h
	st	r0,	NEAR _OutputRec+0eh

;;					OutputRec[15] = PC5D + 0x30;
CLINEA 0000H 0001H 01A3H 0006H 0021H
	l	r0,	0f260h
	srl	r0,	#05h
	and	r0,	#01h
	add	r0,	#030h
	st	r0,	NEAR _OutputRec+0fh

;;					OutputRec[16] = PC4D + 0x30;
CLINEA 0000H 0001H 01A4H 0006H 0021H
	l	r0,	0f260h
	srl	r0,	#04h
	and	r0,	#01h
	add	r0,	#030h
	st	r0,	NEAR _OutputRec+010h

;;					OutputRec[17] = PC3D + 0x30;
CLINEA 0000H 0001H 01A5H 0006H 0021H
	l	r0,	0f260h
	srl	r0,	#03h
	and	r0,	#01h
	add	r0,	#030h
	st	r0,	NEAR _OutputRec+011h

;;					OutputRec[18] = PC2D + 0x30;
CLINEA 0000H 0001H 01A6H 0006H 0021H
	l	r0,	0f260h
	srl	r0,	#02h
	and	r0,	#01h
	add	r0,	#030h
	st	r0,	NEAR _OutputRec+012h

;;					OutputRec[19] = PC1D + 0x30;
CLINEA 0000H 0001H 01A7H 0006H 0021H
	l	r0,	0f260h
	srl	r0,	#01h
	and	r0,	#01h
	add	r0,	#030h
	st	r0,	NEAR _OutputRec+013h

;;					OutputRec[20] = PC0D + 0x30;
CLINEA 0000H 0001H 01A8H 0006H 0021H
	l	r0,	0f260h
	and	r0,	#01h
	add	r0,	#030h
	st	r0,	NEAR _OutputRec+014h

;;					_flgUartFin = 0;
CLINEA 0000H 0001H 01AAH 0006H 0015H
	mov	r0,	#00h
	st	r0,	NEAR __flgUartFin

;;					uart_stop();
CLINEA 0000H 0001H 01ABH 0006H 0011H
	bl	_uart_stop

;;					uart_startSend(OutputRec, 23, _funcUartFin);
CLINEA 0000H 0001H 01ACH 0006H 0031H
	mov	r0,	#BYTE1 OFFSET __funcUartFin
	mov	r1,	#BYTE2 OFFSET __funcUartFin
	push	er0
	mov	er2,	#23
	mov	r0,	#BYTE1 OFFSET _OutputRec
	mov	r1,	#BYTE2 OFFSET _OutputRec
	bl	_uart_startSend
	add	sp,	#2 

;;					while(_flgUartFin != 1){
CLINEA 0000H 0000H 01ADH 0001H 000BH
	bal	_$L486

;;					while(_flgUartFin != 1){
CLINEA 0000H 0000H 01ADH 0006H 001DH
_$L98 :
CBLOCK 141 25 429

;;						NOP1000();
CLINEA 0000H 0001H 01AEH 0007H 0010H
	bl	_NOP1000

;;						main_clrWDT();
CLINEA 0000H 0001H 01AFH 0007H 0014H
	bl	_main_clrWDT
CBLOCKEND 141 25 432

;;					while(_flgUartFin != 1){
CLINEA 0000H 0000H 01ADH 0001H 000BH
_$L486 :
	l	r0,	NEAR __flgUartFin
	cmp	r0,	#01h
	bne	_$L98

;;					}
CLINEA 0000H 0000H 01B0H 0006H 0006H
_$L97 :
CBLOCKEND 141 22 433
CBLOCKEND 141 21 434
CBLOCKEND 141 20 435

;;		if(RecWorld[0] == 0x49){			//if RECWORLD == "INB"
CLINEA 0000H 0001H 01B7H 0003H 0033H
	l	r0,	NEAR _RecWorld
	cmp	r0,	#049h
	beq	_$M106
	b	_$L127
_$M106 :
CBLOCK 141 26 439

;;			if(RecWorld[1] == 0x4E){
CLINEA 0000H 0001H 01B8H 0004H 001BH
	l	r0,	NEAR _RecWorld+01h
	cmp	r0,	#04eh
	beq	_$M107
	b	_$L127
_$M107 :
CBLOCK 141 27 440

;;				if(RecWorld[2] == 0x42){
CLINEA 0000H 0001H 01B9H 0005H 001CH
	l	r0,	NEAR _RecWorld+02h
	cmp	r0,	#042h
	beq	_$M108
	b	_$L127
_$M108 :
CBLOCK 141 28 441

;;					InputStatus[2] = 0x42;
CLINEA 0000H 0001H 01BAH 0006H 001BH
	mov	r0,	#042h
	st	r0,	NEAR _InputStatus+02h

;;					InputRec[2] = 0x42;
CLINEA 0000H 0001H 01BBH 0006H 0018H
	st	r0,	NEAR _InputRec+02h

;;					for(count = 4; count < 12; count++)
CLINEA 0000H 0001H 01BCH 0006H 0028H
	mov	er4,	#4 
_$L108 :
CBLOCK 141 29 445

;;						RecWorld[count] -= 0x30;
CLINEA 0000H 0001H 01BEH 0007H 001EH
	l	r2,	NEAR _RecWorld[er4]
	add	r2,	#0d0h
	st	r2,	NEAR _RecWorld[er4]

;;						if(RecWorld[count] != (0x01||0x00)){
CLINEA 0000H 0001H 01BFH 0007H 002AH
	mov	r0,	r2
	cmp	r0,	#01h
	beq	_$L120
CBLOCK 141 30 447

;;							RecWorld[count] = 0;
CLINEA 0000H 0001H 01C0H 0008H 001BH
	mov	r2,	#00h
	st	r2,	NEAR _RecWorld[er4]
CBLOCKEND 141 30 449

;;						}
CLINEA 0000H 0000H 01C1H 0007H 0007H
_$L120 :
CBLOCKEND 141 29 450

;;					for(count = 4; count < 12; count++)
CLINEA 0000H 0000H 01BCH 0006H 0028H
	add	er4,	#1 
	cmp	r4,	#0ch
	cmpc	r5,	#00h
	blt	_$L108

;;					PB7DIR = RecWorld[4]; 
CLINEA 0000H 0001H 01C8H 0006H 001BH
	l	r0,	NEAR _RecWorld+04h
	and	r0,	#01h
	beq	_$M49
	sb	0f259h.7
	bal	_$M50
_$M49 :
	rb	0f259h.7
_$M50 :

;;					PB2DIR = RecWorld[9];
CLINEA 0000H 0001H 01CDH 0006H 001AH
	l	r0,	NEAR _RecWorld+09h
	and	r0,	#01h
	beq	_$M51
	sb	0f259h.2
	bal	_$M52
_$M51 :
	rb	0f259h.2
_$M52 :

;;					InputStatus[4] = PB7DIR + 0x30;
CLINEA 0000H 0001H 01D2H 0006H 0024H
	l	r0,	0f259h
	srl	r0,	#07h
	and	r0,	#01h
	add	r0,	#030h
	st	r0,	NEAR _InputStatus+04h

;;					InputStatus[5] = 0x78;
CLINEA 0000H 0001H 01D3H 0006H 001BH
	mov	r0,	#078h
	st	r0,	NEAR _InputStatus+05h

;;					InputStatus[6] = 0x78;
CLINEA 0000H 0001H 01D4H 0006H 001BH
	st	r0,	NEAR _InputStatus+06h

;;					InputStatus[7] = 0x78;
CLINEA 0000H 0001H 01D5H 0006H 001BH
	st	r0,	NEAR _InputStatus+07h

;;					InputStatus[8] = 0x78;
CLINEA 0000H 0001H 01D6H 0006H 001BH
	st	r0,	NEAR _InputStatus+08h

;;					InputStatus[9] = PB2DIR + 0x30;
CLINEA 0000H 0001H 01D7H 0006H 0024H
	l	r0,	0f259h
	srl	r0,	#02h
	and	r0,	#01h
	add	r0,	#030h
	st	r0,	NEAR _InputStatus+09h

;;					InputStatus[10] = 0x78;
CLINEA 0000H 0001H 01D8H 0006H 001CH
	mov	r0,	#078h
	st	r0,	NEAR _InputStatus+0ah

;;					InputStatus[11] = 0x78;
CLINEA 0000H 0001H 01D9H 0006H 001CH
	st	r0,	NEAR _InputStatus+0bh

;;					InputStatus[13] = PB7D + 0x30;
CLINEA 0000H 0001H 01DCH 0006H 0023H
	l	r0,	0f258h
	srl	r0,	#07h
	and	r0,	#01h
	add	r0,	#030h
	st	r0,	NEAR _InputStatus+0dh

;;					InputStatus[14] = 0x78;
CLINEA 0000H 0001H 01DDH 0006H 001CH
	mov	r0,	#078h
	st	r0,	NEAR _InputStatus+0eh

;;					InputStatus[15] = 0x78;
CLINEA 0000H 0001H 01DEH 0006H 001CH
	st	r0,	NEAR _InputStatus+0fh

;;					InputStatus[16] = 0x78;
CLINEA 0000H 0001H 01DFH 0006H 001CH
	st	r0,	NEAR _InputStatus+010h

;;					InputStatus[17] = 0x78;
CLINEA 0000H 0001H 01E0H 0006H 001CH
	st	r0,	NEAR _InputStatus+011h

;;					InputStatus[18] = PB2D + 0x30;
CLINEA 0000H 0001H 01E1H 0006H 0023H
	l	r0,	0f258h
	srl	r0,	#02h
	and	r0,	#01h
	add	r0,	#030h
	st	r0,	NEAR _InputStatus+012h

;;					InputStatus[19] = 0x78;
CLINEA 0000H 0001H 01E2H 0006H 001CH
	mov	r0,	#078h
	st	r0,	NEAR _InputStatus+013h

;;					InputStatus[20] = 0x78;
CLINEA 0000H 0001H 01E3H 0006H 001CH
	st	r0,	NEAR _InputStatus+014h

;;					_flgUartFin = 0;
CLINEA 0000H 0001H 01E7H 0006H 0015H
	mov	r0,	#00h
	st	r0,	NEAR __flgUartFin

;;					uart_stop();
CLINEA 0000H 0001H 01E8H 0006H 0011H
	bl	_uart_stop

;;					uart_startSend(InputStatus, 23, _funcUartFin);
CLINEA 0000H 0001H 01E9H 0006H 0033H
	mov	r0,	#BYTE1 OFFSET __funcUartFin
	mov	r1,	#BYTE2 OFFSET __funcUartFin
	push	er0
	mov	er2,	#23
	mov	r0,	#BYTE1 OFFSET _InputStatus
	mov	r1,	#BYTE2 OFFSET _InputStatus
	bl	_uart_startSend
	add	sp,	#2 

;;					while(_flgUartFin != 1){
CLINEA 0000H 0000H 01EAH 0001H 000BH
	bal	_$L487

;;					while(_flgUartFin != 1){
CLINEA 0000H 0000H 01EAH 0006H 001DH
_$L124 :
CBLOCK 141 31 490

;;						NOP1000();
CLINEA 0000H 0001H 01EBH 0007H 0010H
	bl	_NOP1000

;;						main_clrWDT();
CLINEA 0000H 0001H 01ECH 0007H 0014H
	bl	_main_clrWDT
CBLOCKEND 141 31 493

;;					while(_flgUartFin != 1){
CLINEA 0000H 0000H 01EAH 0001H 000BH
_$L487 :
	l	r0,	NEAR __flgUartFin
	cmp	r0,	#01h
	bne	_$L124

;;					_flgUartFin = 0;
CLINEA 0000H 0001H 01F0H 0006H 0015H
	mov	r0,	#00h
	st	r0,	NEAR __flgUartFin

;;					uart_stop();
CLINEA 0000H 0001H 01F1H 0006H 0011H
	bl	_uart_stop

;;					uart_startSend(InputRec, 14, _funcUartFin);
CLINEA 0000H 0001H 01F2H 0006H 0030H
	mov	r0,	#BYTE1 OFFSET __funcUartFin
	mov	r1,	#BYTE2 OFFSET __funcUartFin
	push	er0
	mov	er2,	#14
	mov	r0,	#BYTE1 OFFSET _InputRec
	mov	r1,	#BYTE2 OFFSET _InputRec
	bl	_uart_startSend
	add	sp,	#2 

;;					while(_flgUartFin != 1){
CLINEA 0000H 0000H 01F3H 0001H 000BH
	bal	_$L488

;;					while(_flgUartFin != 1){
CLINEA 0000H 0000H 01F3H 0006H 001DH
_$L128 :
CBLOCK 141 32 499

;;						NOP1000();
CLINEA 0000H 0001H 01F4H 0007H 0010H
	bl	_NOP1000

;;						main_clrWDT();
CLINEA 0000H 0001H 01F5H 0007H 0014H
	bl	_main_clrWDT
CBLOCKEND 141 32 502

;;					while(_flgUartFin != 1){
CLINEA 0000H 0000H 01F3H 0001H 000BH
_$L488 :
	l	r0,	NEAR __flgUartFin
	cmp	r0,	#01h
	bne	_$L128

;;					}
CLINEA 0000H 0000H 01F6H 0006H 0006H
_$L127 :
CBLOCKEND 141 28 503
CBLOCKEND 141 27 504
CBLOCKEND 141 26 505

;;		if(RecWorld[0] == 0x4F){			//if RECWORLD == "OUB"
CLINEA 0000H 0001H 01FDH 0003H 0033H
	l	r0,	NEAR _RecWorld
	cmp	r0,	#04fh
	beq	_$M109
	b	_$L153
_$M109 :
CBLOCK 141 33 509

;;			if(RecWorld[1] == 0x55){
CLINEA 0000H 0001H 01FEH 0004H 001BH
	l	r0,	NEAR _RecWorld+01h
	cmp	r0,	#055h
	beq	_$M110
	b	_$L153
_$M110 :
CBLOCK 141 34 510

;;				if(RecWorld[2] == 0x42){
CLINEA 0000H 0001H 01FFH 0005H 001CH
	l	r0,	NEAR _RecWorld+02h
	cmp	r0,	#042h
	beq	_$M111
	b	_$L153
_$M111 :
CBLOCK 141 35 511

;;					OutputRec[2] = 0x42;
CLINEA 0000H 0001H 0200H 0006H 0019H
	mov	r0,	#042h
	st	r0,	NEAR _OutputRec+02h

;;					for(count = 4; count < 21; count++)
CLINEA 0000H 0001H 0201H 0006H 0028H
	mov	er4,	#4 
_$L138 :
CBLOCK 141 36 514

;;						RecWorld[count] -= 0x30;
CLINEA 0000H 0001H 0203H 0007H 001EH
	l	r2,	NEAR _RecWorld[er4]
	add	r2,	#0d0h
	st	r2,	NEAR _RecWorld[er4]

;;						if(RecWorld[count] != (0x01||0x00)){
CLINEA 0000H 0001H 0204H 0007H 002AH
	mov	r0,	r2
	cmp	r0,	#01h
	beq	_$L150
CBLOCK 141 37 516

;;							RecWorld[count] = 0;
CLINEA 0000H 0001H 0205H 0008H 001BH
	mov	r2,	#00h
	st	r2,	NEAR _RecWorld[er4]
CBLOCKEND 141 37 518

;;						}
CLINEA 0000H 0000H 0206H 0007H 0007H
_$L150 :
CBLOCKEND 141 36 519

;;					for(count = 4; count < 21; count++)
CLINEA 0000H 0000H 0201H 0006H 0028H
	add	er4,	#1 
	cmp	r4,	#015h
	cmpc	r5,	#00h
	blt	_$L138

;;					PB7DIR = RecWorld[4];
CLINEA 0000H 0001H 0209H 0006H 001AH
	l	r0,	NEAR _RecWorld+04h
	and	r0,	#01h
	beq	_$M53
	sb	0f259h.7
	bal	_$M54
_$M53 :
	rb	0f259h.7
_$M54 :

;;					PB2DIR = RecWorld[9];
CLINEA 0000H 0001H 020EH 0006H 001AH
	l	r0,	NEAR _RecWorld+09h
	and	r0,	#01h
	beq	_$M55
	sb	0f259h.2
	bal	_$M56
_$M55 :
	rb	0f259h.2
_$M56 :

;;					PB7D = RecWorld[13];
CLINEA 0000H 0001H 0213H 0006H 0019H
	l	r0,	NEAR _RecWorld+0dh
	and	r0,	#01h
	beq	_$M57
	sb	0f258h.7
	bal	_$M58
_$M57 :
	rb	0f258h.7
_$M58 :

;;					PB2D = RecWorld[18];
CLINEA 0000H 0001H 0218H 0006H 0019H
	l	r0,	NEAR _RecWorld+012h
	and	r0,	#01h
	beq	_$M59
	sb	0f258h.2
	bal	_$M60
_$M59 :
	rb	0f258h.2
_$M60 :

;;					OutputRec[13] = PB7D + 0x30;
CLINEA 0000H 0001H 021DH 0006H 0021H
	l	r0,	0f258h
	srl	r0,	#07h
	and	r0,	#01h
	add	r0,	#030h
	st	r0,	NEAR _OutputRec+0dh

;;					OutputRec[14] = 0x78;
CLINEA 0000H 0001H 021EH 0006H 001AH
	mov	r0,	#078h
	st	r0,	NEAR _OutputRec+0eh

;;					OutputRec[15] = 0x78;
CLINEA 0000H 0001H 021FH 0006H 001AH
	st	r0,	NEAR _OutputRec+0fh

;;					OutputRec[16] = 0x78;
CLINEA 0000H 0001H 0220H 0006H 001AH
	st	r0,	NEAR _OutputRec+010h

;;					OutputRec[17] = 0x78;
CLINEA 0000H 0001H 0221H 0006H 001AH
	st	r0,	NEAR _OutputRec+011h

;;					OutputRec[18] = PB2D + 0x30;
CLINEA 0000H 0001H 0222H 0006H 0021H
	l	r0,	0f258h
	srl	r0,	#02h
	and	r0,	#01h
	add	r0,	#030h
	st	r0,	NEAR _OutputRec+012h

;;					OutputRec[19] = 0x78;
CLINEA 0000H 0001H 0223H 0006H 001AH
	mov	r0,	#078h
	st	r0,	NEAR _OutputRec+013h

;;					OutputRec[20] = 0x78;
CLINEA 0000H 0001H 0224H 0006H 001AH
	st	r0,	NEAR _OutputRec+014h

;;					_flgUartFin = 0;
CLINEA 0000H 0001H 0226H 0006H 0015H
	mov	r0,	#00h
	st	r0,	NEAR __flgUartFin

;;					uart_stop();
CLINEA 0000H 0001H 0227H 0006H 0011H
	bl	_uart_stop

;;					uart_startSend(OutputRec, 23, _funcUartFin);
CLINEA 0000H 0001H 0228H 0006H 0031H
	mov	r0,	#BYTE1 OFFSET __funcUartFin
	mov	r1,	#BYTE2 OFFSET __funcUartFin
	push	er0
	mov	er2,	#23
	mov	r0,	#BYTE1 OFFSET _OutputRec
	mov	r1,	#BYTE2 OFFSET _OutputRec
	bl	_uart_startSend
	add	sp,	#2 

;;					while(_flgUartFin != 1){
CLINEA 0000H 0000H 0229H 0001H 000BH
	bal	_$L489

;;					while(_flgUartFin != 1){
CLINEA 0000H 0000H 0229H 0006H 001DH
_$L154 :
CBLOCK 141 38 553

;;						NOP1000();
CLINEA 0000H 0001H 022AH 0007H 0010H
	bl	_NOP1000

;;						main_clrWDT();
CLINEA 0000H 0001H 022BH 0007H 0014H
	bl	_main_clrWDT
CBLOCKEND 141 38 556

;;					while(_flgUartFin != 1){
CLINEA 0000H 0000H 0229H 0001H 000BH
_$L489 :
	l	r0,	NEAR __flgUartFin
	cmp	r0,	#01h
	bne	_$L154

;;					}
CLINEA 0000H 0000H 022CH 0006H 0006H
_$L153 :
CBLOCKEND 141 35 557
CBLOCKEND 141 34 558
CBLOCKEND 141 33 559

;;		if(RecWorld[0] == 0x49){			//if RECWORLD == "IND"
CLINEA 0000H 0001H 0233H 0003H 0033H
	l	r0,	NEAR _RecWorld
	cmp	r0,	#049h
	beq	_$M112
	b	_$L183
_$M112 :
CBLOCK 141 39 563

;;			if(RecWorld[1] == 0x4E){
CLINEA 0000H 0001H 0234H 0004H 001BH
	l	r0,	NEAR _RecWorld+01h
	cmp	r0,	#04eh
	beq	_$M113
	b	_$L183
_$M113 :
CBLOCK 141 40 564

;;				if(RecWorld[2] == 0x44){
CLINEA 0000H 0001H 0235H 0005H 001CH
	l	r0,	NEAR _RecWorld+02h
	cmp	r0,	#044h
	beq	_$M114
	b	_$L183
_$M114 :
CBLOCK 141 41 565

;;					InputStatus[2] = 0x44;
CLINEA 0000H 0001H 0236H 0006H 001BH
	mov	r0,	#044h
	st	r0,	NEAR _InputStatus+02h

;;					InputRec[2] = 0x44;
CLINEA 0000H 0001H 0237H 0006H 0018H
	st	r0,	NEAR _InputRec+02h

;;					for(count = 4; count < 12; count++)
CLINEA 0000H 0001H 0238H 0006H 0028H
	mov	er4,	#4 
_$L164 :
CBLOCK 141 42 569

;;						RecWorld[count] -= 0x30;
CLINEA 0000H 0001H 023AH 0007H 001EH
	l	r2,	NEAR _RecWorld[er4]
	add	r2,	#0d0h
	st	r2,	NEAR _RecWorld[er4]

;;						if(RecWorld[count] != (0x01||0x00)){
CLINEA 0000H 0001H 023BH 0007H 002AH
	mov	r0,	r2
	cmp	r0,	#01h
	beq	_$L176
CBLOCK 141 43 571

;;							RecWorld[count] = 0;
CLINEA 0000H 0001H 023CH 0008H 001BH
	mov	r2,	#00h
	st	r2,	NEAR _RecWorld[er4]
CBLOCKEND 141 43 573

;;						}
CLINEA 0000H 0000H 023DH 0007H 0007H
_$L176 :
CBLOCKEND 141 42 574

;;					for(count = 4; count < 12; count++)
CLINEA 0000H 0000H 0238H 0006H 0028H
	add	er4,	#1 
	cmp	r4,	#0ch
	cmpc	r5,	#00h
	blt	_$L164

;;					PD5DIR = RecWorld[6];
CLINEA 0000H 0001H 0243H 0006H 001AH
	l	r0,	NEAR _RecWorld+06h
	and	r0,	#01h
	beq	_$M61
	sb	0f269h.5
	bal	_$M62
_$M61 :
	rb	0f269h.5
_$M62 :

;;					PD4DIR = RecWorld[7];
CLINEA 0000H 0001H 0244H 0006H 001AH
	l	r0,	NEAR _RecWorld+07h
	and	r0,	#01h
	beq	_$M63
	sb	0f269h.4
	bal	_$M64
_$M63 :
	rb	0f269h.4
_$M64 :

;;					PD3DIR = RecWorld[8];
CLINEA 0000H 0001H 0245H 0006H 001AH
	l	r0,	NEAR _RecWorld+08h
	and	r0,	#01h
	beq	_$M65
	sb	0f269h.3
	bal	_$M66
_$M65 :
	rb	0f269h.3
_$M66 :

;;					PD2DIR = RecWorld[9];
CLINEA 0000H 0001H 0246H 0006H 001AH
	l	r0,	NEAR _RecWorld+09h
	and	r0,	#01h
	beq	_$M67
	sb	0f269h.2
	bal	_$M68
_$M67 :
	rb	0f269h.2
_$M68 :

;;					PD1DIR = RecWorld[10];
CLINEA 0000H 0001H 0247H 0006H 001BH
	l	r0,	NEAR _RecWorld+0ah
	and	r0,	#01h
	beq	_$M69
	sb	0f269h.1
	bal	_$M70
_$M69 :
	rb	0f269h.1
_$M70 :

;;					PD0DIR = RecWorld[11];
CLINEA 0000H 0001H 0248H 0006H 001BH
	l	r0,	NEAR _RecWorld+0bh
	and	r0,	#01h
	beq	_$M71
	sb	0f269h.0
	bal	_$M72
_$M71 :
	rb	0f269h.0
_$M72 :

;;					InputStatus[4] = 0x78;
CLINEA 0000H 0001H 024BH 0006H 001BH
	mov	r0,	#078h
	st	r0,	NEAR _InputStatus+04h

;;					InputStatus[5] = 0x78;
CLINEA 0000H 0001H 024CH 0006H 001BH
	st	r0,	NEAR _InputStatus+05h

;;					InputStatus[6] = PD5DIR + 0x30;
CLINEA 0000H 0001H 024DH 0006H 0024H
	l	r0,	0f269h
	srl	r0,	#05h
	and	r0,	#01h
	add	r0,	#030h
	st	r0,	NEAR _InputStatus+06h

;;					InputStatus[7] = PD4DIR + 0x30;
CLINEA 0000H 0001H 024EH 0006H 0024H
	l	r0,	0f269h
	srl	r0,	#04h
	and	r0,	#01h
	add	r0,	#030h
	st	r0,	NEAR _InputStatus+07h

;;					InputStatus[8] = PD3DIR + 0x30;
CLINEA 0000H 0001H 024FH 0006H 0024H
	l	r0,	0f269h
	srl	r0,	#03h
	and	r0,	#01h
	add	r0,	#030h
	st	r0,	NEAR _InputStatus+08h

;;					InputStatus[9] = PD2DIR + 0x30;
CLINEA 0000H 0001H 0250H 0006H 0024H
	l	r0,	0f269h
	srl	r0,	#02h
	and	r0,	#01h
	add	r0,	#030h
	st	r0,	NEAR _InputStatus+09h

;;					InputStatus[10] = PD1DIR + 0x30;
CLINEA 0000H 0001H 0251H 0006H 0025H
	l	r0,	0f269h
	srl	r0,	#01h
	and	r0,	#01h
	add	r0,	#030h
	st	r0,	NEAR _InputStatus+0ah

;;					InputStatus[11] = PD0DIR + 0x30;
CLINEA 0000H 0001H 0252H 0006H 0025H
	l	r0,	0f269h
	and	r0,	#01h
	add	r0,	#030h
	st	r0,	NEAR _InputStatus+0bh

;;					InputStatus[13] = 0x78;
CLINEA 0000H 0001H 0255H 0006H 001CH
	mov	r0,	#078h
	st	r0,	NEAR _InputStatus+0dh

;;					InputStatus[14] = 0x78;
CLINEA 0000H 0001H 0256H 0006H 001CH
	st	r0,	NEAR _InputStatus+0eh

;;					InputStatus[15] = PD5D + 0x30;
CLINEA 0000H 0001H 0257H 0006H 0023H
	l	r0,	0f268h
	srl	r0,	#05h
	and	r0,	#01h
	add	r0,	#030h
	st	r0,	NEAR _InputStatus+0fh

;;					InputStatus[16] = PD4D + 0x30;
CLINEA 0000H 0001H 0258H 0006H 0023H
	l	r0,	0f268h
	srl	r0,	#04h
	and	r0,	#01h
	add	r0,	#030h
	st	r0,	NEAR _InputStatus+010h

;;					InputStatus[17] = PD3D + 0x30;
CLINEA 0000H 0001H 0259H 0006H 0023H
	l	r0,	0f268h
	srl	r0,	#03h
	and	r0,	#01h
	add	r0,	#030h
	st	r0,	NEAR _InputStatus+011h

;;					InputStatus[18] = PD2D + 0x30;
CLINEA 0000H 0001H 025AH 0006H 0023H
	l	r0,	0f268h
	srl	r0,	#02h
	and	r0,	#01h
	add	r0,	#030h
	st	r0,	NEAR _InputStatus+012h

;;					InputStatus[19] = PD1D + 0x30;
CLINEA 0000H 0001H 025BH 0006H 0023H
	l	r0,	0f268h
	srl	r0,	#01h
	and	r0,	#01h
	add	r0,	#030h
	st	r0,	NEAR _InputStatus+013h

;;					InputStatus[20] = PD0D + 0x30;
CLINEA 0000H 0001H 025CH 0006H 0023H
	l	r0,	0f268h
	and	r0,	#01h
	add	r0,	#030h
	st	r0,	NEAR _InputStatus+014h

;;					_flgUartFin = 0;
CLINEA 0000H 0001H 0260H 0006H 0015H
	mov	r0,	#00h
	st	r0,	NEAR __flgUartFin

;;					uart_stop();
CLINEA 0000H 0001H 0261H 0006H 0011H
	bl	_uart_stop

;;					uart_startSend(InputStatus, 23, _funcUartFin);
CLINEA 0000H 0001H 0262H 0006H 0033H
	mov	r0,	#BYTE1 OFFSET __funcUartFin
	mov	r1,	#BYTE2 OFFSET __funcUartFin
	push	er0
	mov	er2,	#23
	mov	r0,	#BYTE1 OFFSET _InputStatus
	mov	r1,	#BYTE2 OFFSET _InputStatus
	bl	_uart_startSend
	add	sp,	#2 

;;					while(_flgUartFin != 1){
CLINEA 0000H 0000H 0263H 0001H 000BH
	bal	_$L490

;;					while(_flgUartFin != 1){
CLINEA 0000H 0000H 0263H 0006H 001DH
_$L180 :
CBLOCK 141 44 611

;;						NOP1000();
CLINEA 0000H 0001H 0264H 0007H 0010H
	bl	_NOP1000

;;						main_clrWDT();
CLINEA 0000H 0001H 0265H 0007H 0014H
	bl	_main_clrWDT
CBLOCKEND 141 44 614

;;					while(_flgUartFin != 1){
CLINEA 0000H 0000H 0263H 0001H 000BH
_$L490 :
	l	r0,	NEAR __flgUartFin
	cmp	r0,	#01h
	bne	_$L180

;;					_flgUartFin = 0;
CLINEA 0000H 0001H 0269H 0006H 0015H
	mov	r0,	#00h
	st	r0,	NEAR __flgUartFin

;;					uart_stop();
CLINEA 0000H 0001H 026AH 0006H 0011H
	bl	_uart_stop

;;					uart_startSend(InputRec, 14, _funcUartFin);
CLINEA 0000H 0001H 026BH 0006H 0030H
	mov	r0,	#BYTE1 OFFSET __funcUartFin
	mov	r1,	#BYTE2 OFFSET __funcUartFin
	push	er0
	mov	er2,	#14
	mov	r0,	#BYTE1 OFFSET _InputRec
	mov	r1,	#BYTE2 OFFSET _InputRec
	bl	_uart_startSend
	add	sp,	#2 

;;					while(_flgUartFin != 1){
CLINEA 0000H 0000H 026CH 0001H 000BH
	bal	_$L491

;;					while(_flgUartFin != 1){
CLINEA 0000H 0000H 026CH 0006H 001DH
_$L184 :
CBLOCK 141 45 620

;;						NOP1000();
CLINEA 0000H 0001H 026DH 0007H 0010H
	bl	_NOP1000

;;						main_clrWDT();
CLINEA 0000H 0001H 026EH 0007H 0014H
	bl	_main_clrWDT
CBLOCKEND 141 45 623

;;					while(_flgUartFin != 1){
CLINEA 0000H 0000H 026CH 0001H 000BH
_$L491 :
	l	r0,	NEAR __flgUartFin
	cmp	r0,	#01h
	bne	_$L184

;;					}
CLINEA 0000H 0000H 026FH 0006H 0006H
_$L183 :
CBLOCKEND 141 41 624
CBLOCKEND 141 40 625
CBLOCKEND 141 39 626

;;		if(RecWorld[0] == 0x4F){			//if RECWORLD == "OUD"
CLINEA 0000H 0001H 0276H 0003H 0033H
	l	r0,	NEAR _RecWorld
	cmp	r0,	#04fh
	beq	_$M115
	b	_$L209
_$M115 :
CBLOCK 141 46 630

;;			if(RecWorld[1] == 0x55){
CLINEA 0000H 0001H 0277H 0004H 001BH
	l	r0,	NEAR _RecWorld+01h
	cmp	r0,	#055h
	beq	_$M116
	b	_$L209
_$M116 :
CBLOCK 141 47 631

;;				if(RecWorld[2] == 0x44){
CLINEA 0000H 0001H 0278H 0005H 001CH
	l	r0,	NEAR _RecWorld+02h
	cmp	r0,	#044h
	beq	_$M117
	b	_$L209
_$M117 :
CBLOCK 141 48 632

;;					OutputRec[2] = 0x44;
CLINEA 0000H 0001H 0279H 0006H 0019H
	mov	r0,	#044h
	st	r0,	NEAR _OutputRec+02h

;;					for(count = 4; count < 21; count++)
CLINEA 0000H 0001H 027AH 0006H 0028H
	mov	er4,	#4 
_$L194 :
CBLOCK 141 49 635

;;						RecWorld[count] -= 0x30;
CLINEA 0000H 0001H 027CH 0007H 001EH
	l	r2,	NEAR _RecWorld[er4]
	add	r2,	#0d0h
	st	r2,	NEAR _RecWorld[er4]

;;						if(RecWorld[count] != (0x01||0x00)){
CLINEA 0000H 0001H 027DH 0007H 002AH
	mov	r0,	r2
	cmp	r0,	#01h
	beq	_$L206
CBLOCK 141 50 637

;;							RecWorld[count] = 0;
CLINEA 0000H 0001H 027EH 0008H 001BH
	mov	r2,	#00h
	st	r2,	NEAR _RecWorld[er4]
CBLOCKEND 141 50 639

;;						}
CLINEA 0000H 0000H 027FH 0007H 0007H
_$L206 :
CBLOCKEND 141 49 640

;;					for(count = 4; count < 21; count++)
CLINEA 0000H 0000H 027AH 0006H 0028H
	add	er4,	#1 
	cmp	r4,	#015h
	cmpc	r5,	#00h
	blt	_$L194

;;					PD5DIR = RecWorld[6];
CLINEA 0000H 0001H 0284H 0006H 001AH
	l	r0,	NEAR _RecWorld+06h
	and	r0,	#01h
	beq	_$M73
	sb	0f269h.5
	bal	_$M74
_$M73 :
	rb	0f269h.5
_$M74 :

;;					PD4DIR = RecWorld[7];
CLINEA 0000H 0001H 0285H 0006H 001AH
	l	r0,	NEAR _RecWorld+07h
	and	r0,	#01h
	beq	_$M75
	sb	0f269h.4
	bal	_$M76
_$M75 :
	rb	0f269h.4
_$M76 :

;;					PD3DIR = RecWorld[8];
CLINEA 0000H 0001H 0286H 0006H 001AH
	l	r0,	NEAR _RecWorld+08h
	and	r0,	#01h
	beq	_$M77
	sb	0f269h.3
	bal	_$M78
_$M77 :
	rb	0f269h.3
_$M78 :

;;					PD2DIR = RecWorld[9];
CLINEA 0000H 0001H 0287H 0006H 001AH
	l	r0,	NEAR _RecWorld+09h
	and	r0,	#01h
	beq	_$M79
	sb	0f269h.2
	bal	_$M80
_$M79 :
	rb	0f269h.2
_$M80 :

;;					PD1DIR = RecWorld[10];
CLINEA 0000H 0001H 0288H 0006H 001BH
	l	r0,	NEAR _RecWorld+0ah
	and	r0,	#01h
	beq	_$M81
	sb	0f269h.1
	bal	_$M82
_$M81 :
	rb	0f269h.1
_$M82 :

;;					PD0DIR = RecWorld[11];
CLINEA 0000H 0001H 0289H 0006H 001BH
	l	r0,	NEAR _RecWorld+0bh
	and	r0,	#01h
	beq	_$M83
	sb	0f269h.0
	bal	_$M84
_$M83 :
	rb	0f269h.0
_$M84 :

;;					PD5D = RecWorld[15];
CLINEA 0000H 0001H 028EH 0006H 0019H
	l	r0,	NEAR _RecWorld+0fh
	and	r0,	#01h
	beq	_$M85
	sb	0f268h.5
	bal	_$M86
_$M85 :
	rb	0f268h.5
_$M86 :

;;					PD4D = RecWorld[16];
CLINEA 0000H 0001H 028FH 0006H 0019H
	l	r0,	NEAR _RecWorld+010h
	and	r0,	#01h
	beq	_$M87
	sb	0f268h.4
	bal	_$M88
_$M87 :
	rb	0f268h.4
_$M88 :

;;					PD3D = RecWorld[17];
CLINEA 0000H 0001H 0290H 0006H 0019H
	l	r0,	NEAR _RecWorld+011h
	and	r0,	#01h
	beq	_$M89
	sb	0f268h.3
	bal	_$M90
_$M89 :
	rb	0f268h.3
_$M90 :

;;					PD2D = RecWorld[18];
CLINEA 0000H 0001H 0291H 0006H 0019H
	l	r0,	NEAR _RecWorld+012h
	and	r0,	#01h
	beq	_$M91
	sb	0f268h.2
	bal	_$M92
_$M91 :
	rb	0f268h.2
_$M92 :

;;					PD1D = RecWorld[19];
CLINEA 0000H 0001H 0292H 0006H 0019H
	l	r0,	NEAR _RecWorld+013h
	and	r0,	#01h
	beq	_$M93
	sb	0f268h.1
	bal	_$M94
_$M93 :
	rb	0f268h.1
_$M94 :

;;					PD0D = RecWorld[20];
CLINEA 0000H 0001H 0293H 0006H 0019H
	l	r0,	NEAR _RecWorld+014h
	and	r0,	#01h
	beq	_$M95
	sb	0f268h.0
	bal	_$M96
_$M95 :
	rb	0f268h.0
_$M96 :

;;					OutputRec[13] = 0x78;
CLINEA 0000H 0001H 0296H 0006H 001AH
	mov	r0,	#078h
	st	r0,	NEAR _OutputRec+0dh

;;					OutputRec[14] = 0x78;
CLINEA 0000H 0001H 0297H 0006H 001AH
	st	r0,	NEAR _OutputRec+0eh

;;					OutputRec[15] = PD5D + 0x30;
CLINEA 0000H 0001H 0298H 0006H 0021H
	l	r0,	0f268h
	srl	r0,	#05h
	and	r0,	#01h
	add	r0,	#030h
	st	r0,	NEAR _OutputRec+0fh

;;					OutputRec[16] = PD4D + 0x30;
CLINEA 0000H 0001H 0299H 0006H 0021H
	l	r0,	0f268h
	srl	r0,	#04h
	and	r0,	#01h
	add	r0,	#030h
	st	r0,	NEAR _OutputRec+010h

;;					OutputRec[17] = PD3D + 0x30;
CLINEA 0000H 0001H 029AH 0006H 0021H
	l	r0,	0f268h
	srl	r0,	#03h
	and	r0,	#01h
	add	r0,	#030h
	st	r0,	NEAR _OutputRec+011h

;;					OutputRec[18] = PD2D + 0x30;
CLINEA 0000H 0001H 029BH 0006H 0021H
	l	r0,	0f268h
	srl	r0,	#02h
	and	r0,	#01h
	add	r0,	#030h
	st	r0,	NEAR _OutputRec+012h

;;					OutputRec[19] = PD1D + 0x30;
CLINEA 0000H 0001H 029CH 0006H 0021H
	l	r0,	0f268h
	srl	r0,	#01h
	and	r0,	#01h
	add	r0,	#030h
	st	r0,	NEAR _OutputRec+013h

;;					OutputRec[20] = PD0D + 0x30;
CLINEA 0000H 0001H 029DH 0006H 0021H
	l	r0,	0f268h
	and	r0,	#01h
	add	r0,	#030h
	st	r0,	NEAR _OutputRec+014h

;;					_flgUartFin = 0;
CLINEA 0000H 0001H 029FH 0006H 0015H
	mov	r0,	#00h
	st	r0,	NEAR __flgUartFin

;;					uart_stop();
CLINEA 0000H 0001H 02A0H 0006H 0011H
	bl	_uart_stop

;;					uart_startSend(OutputRec, 23, _funcUartFin);
CLINEA 0000H 0001H 02A1H 0006H 0031H
	mov	r0,	#BYTE1 OFFSET __funcUartFin
	mov	r1,	#BYTE2 OFFSET __funcUartFin
	push	er0
	mov	er2,	#23
	mov	r0,	#BYTE1 OFFSET _OutputRec
	mov	r1,	#BYTE2 OFFSET _OutputRec
	bl	_uart_startSend
	add	sp,	#2 

;;					while(_flgUartFin != 1){
CLINEA 0000H 0000H 02A2H 0001H 000BH
	bal	_$L492

;;					while(_flgUartFin != 1){
CLINEA 0000H 0000H 02A2H 0006H 001DH
_$L210 :
CBLOCK 141 51 674

;;						NOP1000();
CLINEA 0000H 0001H 02A3H 0007H 0010H
	bl	_NOP1000

;;						main_clrWDT();
CLINEA 0000H 0001H 02A4H 0007H 0014H
	bl	_main_clrWDT
CBLOCKEND 141 51 677

;;					while(_flgUartFin != 1){
CLINEA 0000H 0000H 02A2H 0001H 000BH
_$L492 :
	l	r0,	NEAR __flgUartFin
	cmp	r0,	#01h
	bne	_$L210

;;					}
CLINEA 0000H 0000H 02A5H 0006H 0006H
_$L209 :
CBLOCKEND 141 48 678
CBLOCKEND 141 47 679
CBLOCKEND 141 46 680

;;		if(RecWorld[0] == 0x49){			//if RECWORLD == "I2CTX"
CLINEA 0000H 0001H 02ACH 0003H 0035H
	l	r0,	NEAR _RecWorld
	cmp	r0,	#049h
	beq	_$M118
	b	_$L397
_$M118 :
CBLOCK 141 52 684

;;			if(RecWorld[1] == 0x32){
CLINEA 0000H 0001H 02ADH 0004H 001BH
	l	r0,	NEAR _RecWorld+01h
	cmp	r0,	#032h
	beq	_$M119
	b	_$L397
_$M119 :
CBLOCK 141 53 685

;;				if(RecWorld[2] == 0x43){
CLINEA 0000H 0001H 02AEH 0005H 001CH
	l	r0,	NEAR _RecWorld+02h
	cmp	r0,	#043h
	beq	_$M120
	b	_$L397
_$M120 :
CBLOCK 141 54 686

;;					if(RecWorld[3] == 0x54){
CLINEA 0000H 0001H 02AFH 0006H 001DH
	l	r0,	NEAR _RecWorld+03h
	cmp	r0,	#054h
	beq	_$M121
	b	_$L397
_$M121 :
CBLOCK 141 55 687

;;						if(RecWorld[4] == 0x58){
CLINEA 0000H 0001H 02B0H 0007H 001EH
	l	r0,	NEAR _RecWorld+04h
	cmp	r0,	#058h
	beq	_$M122
	b	_$L397
_$M122 :
CBLOCK 141 56 688

;;							_flgUartFin = 0;
CLINEA 0000H 0001H 02B3H 0008H 0017H
	mov	r0,	#00h
	st	r0,	NEAR __flgUartFin

;;							uart_stop();
CLINEA 0000H 0001H 02B4H 0008H 0013H
	bl	_uart_stop

;;							uart_startReceive(I2C_BUFF, 46, _funcUartFin);
CLINEA 0000H 0001H 02B5H 0008H 0035H
	mov	r0,	#BYTE1 OFFSET __funcUartFin
	mov	r1,	#BYTE2 OFFSET __funcUartFin
	push	er0
	mov	er2,	#46
	mov	r0,	#BYTE1 OFFSET _I2C_BUFF
	mov	r1,	#BYTE2 OFFSET _I2C_BUFF
	bl	_uart_startReceive
	add	sp,	#2 

;;							while(_flgUartFin != 1){
CLINEA 0000H 0000H 02B6H 0001H 000BH
	bal	_$L493

;;							while(_flgUartFin != 1){
CLINEA 0000H 0000H 02B6H 0008H 001FH
_$L224 :
CBLOCK 141 57 694

;;								NOP1000();
CLINEA 0000H 0001H 02B7H 0009H 0012H
	bl	_NOP1000

;;								main_clrWDT();
CLINEA 0000H 0001H 02B8H 0009H 0016H
	bl	_main_clrWDT
CBLOCKEND 141 57 697

;;							while(_flgUartFin != 1){
CLINEA 0000H 0000H 02B6H 0001H 000BH
_$L493 :
	l	r0,	NEAR __flgUartFin
	cmp	r0,	#01h
	bne	_$L224

;;							chari = 2;
CLINEA 0000H 0001H 02BCH 0008H 0011H
	mov	r0,	#02h
	st	r0,	NEAR _chari

;;							charj = 0;
CLINEA 0000H 0001H 02BDH 0008H 0011H
	mov	r0,	#00h
	st	r0,	NEAR _charj

;;							while(I2C_BUFF[chari]!=0x20){
CLINEA 0000H 0001H 02BFH 0008H 0024H
	l	r0,	NEAR _I2C_BUFF+02h
	cmp	r0,	#020h
	beq	_$L227
_$L228 :
CBLOCK 141 58 703

;;								chari++;
CLINEA 0000H 0000H 02C0H 0009H 0010H
	lea	OFFSET _chari
	inc	[ea]

;;								charj++;
CLINEA 0000H 0000H 02C1H 0009H 0010H
	lea	OFFSET _charj
	inc	[ea]
CBLOCKEND 141 58 706

;;							while(I2C_BUFF[chari]!=0x20){
CLINEA 0000H 0000H 02BFH 001BH 0022H
	l	r0,	NEAR _chari
	mov	r1,	#00h
	l	r0,	NEAR _I2C_BUFF[er0]
	cmp	r0,	#020h
	bne	_$L228

;;							}
CLINEA 0000H 0000H 02C2H 0008H 0008H
_$L227 :

;;							for(chark = charj; chark>0; chark--){
CLINEA 0000H 0001H 02C3H 000CH 0019H
	l	r0,	NEAR _charj

;;							for(chark = charj; chark>0; chark--){
CLINEA 0000H 0000H 02C3H 0001H 000BH
	bal	_$L494

;;							for(chark = charj; chark>0; chark--){
CLINEA 0000H 0000H 02C3H 0024H 002AH
_$L232 :
CBLOCK 141 59 707

;;								if(chark == 3){I2CAdd_temp = (I2C_BUFF[chari-chark]-0x30)*100;}
CLINEA 0000H 0001H 02C4H 0009H 0047H
	cmp	r0,	#03h
	bne	_$L236
CBLOCK 141 60 708
	l	r0,	NEAR _chari
	mov	r1,	#00h
	l	r2,	NEAR _chark
	mov	r3,	#00h
	sub	r0,	r2
	subc	r1,	r3
	l	r0,	NEAR _I2C_BUFF[er0]
	add	r0,	#0d0h
	mov	r1,	r0
	sll	r1,	#01h
	add	r1,	r0
	sll	r1,	#03h
	add	r1,	r0
	sll	r1,	#02h
	st	r1,	NEAR _I2CAdd_temp

;;								else if(chark == 2){I2CAdd_temp = (I2C_BUFF[chari-chark]-0x30)*10;}
CLINEA 0000H 0001H 02C5H 0009H 004BH
	bal	_$L241
_$L236 :
	cmp	r0,	#02h
	bne	_$L239
CBLOCK 141 61 709
	l	r0,	NEAR _chari
	mov	r1,	#00h
	l	r2,	NEAR _chark
	mov	r3,	#00h
	sub	r0,	r2
	subc	r1,	r3
	l	r0,	NEAR _I2C_BUFF[er0]
	add	r0,	#0d0h
	mov	r1,	r0
	sll	r1,	#02h
	add	r1,	r0
	sll	r1,	#01h
	st	r1,	NEAR _I2CAdd_temp
CBLOCKEND 141 61 709

;;								else {I2CAdd_temp = (I2C_BUFF[chari-chark]-0x30);}
CLINEA 0000H 0001H 02C6H 0009H 003AH
	bal	_$L241
_$L239 :
CBLOCK 141 62 710
	l	r0,	NEAR _chari
	mov	r1,	#00h
	l	r2,	NEAR _chark
	mov	r3,	#00h
	sub	r0,	r2
	subc	r1,	r3
	l	r0,	NEAR _I2C_BUFF[er0]
	add	r0,	#0d0h
	st	r0,	NEAR _I2CAdd_temp
CBLOCKEND 141 62 710
_$L241 :

;;								I2CAdd += I2CAdd_temp;
CLINEA 0000H 0001H 02C7H 0009H 001EH
	l	r0,	NEAR _I2CAdd
	l	r1,	NEAR _I2CAdd_temp
	add	r0,	r1
	st	r0,	NEAR _I2CAdd
CBLOCKEND 141 59 712
CBLOCKEND 141 60 989

;;							for(chark = charj; chark>0; chark--){
CLINEA 0000H 0000H 02C3H 0024H 002AH
	mov	r0,	r2
	add	r0,	#0ffh

;;							for(chark = charj; chark>0; chark--){
CLINEA 0000H 0000H 02C3H 0001H 000BH
_$L494 :
	st	r0,	NEAR _chark

;;							for(chark = charj; chark>0; chark--){
CLINEA 0000H 0000H 02C3H 001BH 0022H
	cmp	r0,	#00h
	ble	_$M123
	b	_$L232
_$M123 :

;;							chari++;
CLINEA 0000H 0000H 02C9H 0008H 000FH
	lea	OFFSET _chari
	inc	[ea]

;;							charj = 0;
CLINEA 0000H 0001H 02CAH 0008H 0011H
	mov	r0,	#00h

;;							while(I2C_BUFF[chari]!=0x20){
CLINEA 0000H 0000H 02CBH 0001H 000BH
	bal	_$L495

;;							while(I2C_BUFF[chari]!=0x20){
CLINEA 0000H 0000H 02CBH 0008H 0024H
_$L244 :
CBLOCK 141 63 715

;;								chari++;
CLINEA 0000H 0000H 02CCH 0009H 0010H
	lea	OFFSET _chari
	inc	[ea]

;;								charj++;
CLINEA 0000H 0000H 02CDH 0009H 0010H
	l	r0,	NEAR _charj
	add	r0,	#01h
CBLOCKEND 141 63 718

;;							while(I2C_BUFF[chari]!=0x20){
CLINEA 0000H 0000H 02CBH 0001H 000BH
_$L495 :
	st	r0,	NEAR _charj

;;							while(I2C_BUFF[chari]!=0x20){
CLINEA 0000H 0000H 02CBH 001BH 0022H
	l	r0,	NEAR _chari
	mov	r1,	#00h
	l	r0,	NEAR _I2C_BUFF[er0]
	cmp	r0,	#020h
	bne	_$L244

;;							for(chark = charj; chark>0; chark--){
CLINEA 0000H 0001H 02CFH 000CH 0019H
	l	r0,	NEAR _charj

;;							for(chark = charj; chark>0; chark--){
CLINEA 0000H 0000H 02CFH 0001H 000BH
	bal	_$L496

;;							for(chark = charj; chark>0; chark--){
CLINEA 0000H 0000H 02CFH 0024H 002AH
_$L248 :
CBLOCK 141 64 719

;;								if(chark == 3){I2CNumBytes_temp = (I2C_BUFF[chari-chark]-0x30)*100;}
CLINEA 0000H 0001H 02D0H 0009H 004CH
	cmp	r0,	#03h
	bne	_$L252
CBLOCK 141 65 720
	l	r0,	NEAR _chari
	mov	r1,	#00h
	l	r2,	NEAR _chark
	mov	r3,	#00h
	sub	r0,	r2
	subc	r1,	r3
	l	r0,	NEAR _I2C_BUFF[er0]
	add	r0,	#0d0h
	mov	r1,	r0
	sll	r1,	#01h
	add	r1,	r0
	sll	r1,	#03h
	add	r1,	r0
	sll	r1,	#02h
	st	r1,	NEAR _I2CNumBytes_temp

;;								else if(chark == 2){I2CNumBytes_temp = (I2C_BUFF[chari-chark]-0x30)*10;}
CLINEA 0000H 0001H 02D1H 0009H 0050H
	bal	_$L257
_$L252 :
	cmp	r0,	#02h
	bne	_$L255
CBLOCK 141 66 721
	l	r0,	NEAR _chari
	mov	r1,	#00h
	l	r2,	NEAR _chark
	mov	r3,	#00h
	sub	r0,	r2
	subc	r1,	r3
	l	r0,	NEAR _I2C_BUFF[er0]
	add	r0,	#0d0h
	mov	r1,	r0
	sll	r1,	#02h
	add	r1,	r0
	sll	r1,	#01h
	st	r1,	NEAR _I2CNumBytes_temp
CBLOCKEND 141 66 721

;;								else {I2CNumBytes_temp = (I2C_BUFF[chari-chark]-0x30);}
CLINEA 0000H 0001H 02D2H 0009H 003FH
	bal	_$L257
_$L255 :
CBLOCK 141 67 722
	l	r0,	NEAR _chari
	mov	r1,	#00h
	l	r2,	NEAR _chark
	mov	r3,	#00h
	sub	r0,	r2
	subc	r1,	r3
	l	r0,	NEAR _I2C_BUFF[er0]
	add	r0,	#0d0h
	st	r0,	NEAR _I2CNumBytes_temp
CBLOCKEND 141 67 722
_$L257 :

;;								I2CNumBytes += I2CNumBytes_temp;
CLINEA 0000H 0001H 02D3H 0009H 0028H
	l	r0,	NEAR _I2CNumBytes
	l	r1,	NEAR _I2CNumBytes_temp
	add	r0,	r1
	st	r0,	NEAR _I2CNumBytes
CBLOCKEND 141 64 724
CBLOCKEND 141 65 989

;;							for(chark = charj; chark>0; chark--){
CLINEA 0000H 0000H 02CFH 0024H 002AH
	mov	r0,	r2
	add	r0,	#0ffh

;;							for(chark = charj; chark>0; chark--){
CLINEA 0000H 0000H 02CFH 0001H 000BH
_$L496 :
	st	r0,	NEAR _chark

;;							for(chark = charj; chark>0; chark--){
CLINEA 0000H 0000H 02CFH 001BH 0022H
	cmp	r0,	#00h
	ble	_$M124
	b	_$L248
_$M124 :

;;							chari++;
CLINEA 0000H 0000H 02D5H 0008H 000FH
	lea	OFFSET _chari
	inc	[ea]

;;							charj = 0;
CLINEA 0000H 0001H 02D6H 0008H 0011H
	mov	r0,	#00h

;;							while(I2C_BUFF[chari]!=0x20){
CLINEA 0000H 0000H 02D8H 0001H 000BH
	bal	_$L497

;;							while(I2C_BUFF[chari]!=0x20){
CLINEA 0000H 0000H 02D8H 0008H 0024H
_$L260 :
CBLOCK 141 68 728

;;								chari++;
CLINEA 0000H 0000H 02D9H 0009H 0010H
	lea	OFFSET _chari
	inc	[ea]

;;								charj++;
CLINEA 0000H 0000H 02DAH 0009H 0010H
	l	r0,	NEAR _charj
	add	r0,	#01h
CBLOCKEND 141 68 731

;;							while(I2C_BUFF[chari]!=0x20){
CLINEA 0000H 0000H 02D8H 0001H 000BH
_$L497 :
	st	r0,	NEAR _charj

;;							while(I2C_BUFF[chari]!=0x20){
CLINEA 0000H 0000H 02D8H 001BH 0022H
	l	r0,	NEAR _chari
	mov	r1,	#00h
	l	r0,	NEAR _I2C_BUFF[er0]
	cmp	r0,	#020h
	bne	_$L260

;;							for(chark = charj; chark>0; chark--){
CLINEA 0000H 0001H 02DCH 000CH 0019H
	l	r0,	NEAR _charj

;;							for(chark = charj; chark>0; chark--){
CLINEA 0000H 0000H 02DCH 0001H 000BH
	bal	_$L498

;;							for(chark = charj; chark>0; chark--){
CLINEA 0000H 0000H 02DCH 0024H 002AH
_$L264 :
CBLOCK 141 69 732

;;								if(chark == 3){Data0Str_temp = (I2C_BUFF[chari-chark]-0x30)*100;}
CLINEA 0000H 0001H 02DDH 0009H 0049H
	cmp	r0,	#03h
	bne	_$L268
CBLOCK 141 70 733
	l	r0,	NEAR _chari
	mov	r1,	#00h
	l	r2,	NEAR _chark
	mov	r3,	#00h
	sub	r0,	r2
	subc	r1,	r3
	l	r0,	NEAR _I2C_BUFF[er0]
	add	r0,	#0d0h
	mov	r1,	r0
	sll	r1,	#01h
	add	r1,	r0
	sll	r1,	#03h
	add	r1,	r0
	sll	r1,	#02h
	st	r1,	NEAR _Data0Str_temp

;;								else if(chark == 2){Data0Str_temp = (I2C_BUFF[chari-chark]-0x30)*10;}
CLINEA 0000H 0001H 02DEH 0009H 004DH
	bal	_$L273
_$L268 :
	cmp	r0,	#02h
	bne	_$L271
CBLOCK 141 71 734
	l	r0,	NEAR _chari
	mov	r1,	#00h
	l	r2,	NEAR _chark
	mov	r3,	#00h
	sub	r0,	r2
	subc	r1,	r3
	l	r0,	NEAR _I2C_BUFF[er0]
	add	r0,	#0d0h
	mov	r1,	r0
	sll	r1,	#02h
	add	r1,	r0
	sll	r1,	#01h
	st	r1,	NEAR _Data0Str_temp
CBLOCKEND 141 71 734

;;								else {Data0Str_temp = (I2C_BUFF[chari-chark]-0x30);}
CLINEA 0000H 0001H 02DFH 0009H 003CH
	bal	_$L273
_$L271 :
CBLOCK 141 72 735
	l	r0,	NEAR _chari
	mov	r1,	#00h
	l	r2,	NEAR _chark
	mov	r3,	#00h
	sub	r0,	r2
	subc	r1,	r3
	l	r0,	NEAR _I2C_BUFF[er0]
	add	r0,	#0d0h
	st	r0,	NEAR _Data0Str_temp
CBLOCKEND 141 72 735
_$L273 :

;;								Data0Str += Data0Str_temp;
CLINEA 0000H 0001H 02E0H 0009H 0022H
	l	r0,	NEAR _Data0Str
	l	r1,	NEAR _Data0Str_temp
	add	r0,	r1
	st	r0,	NEAR _Data0Str
CBLOCKEND 141 69 737
CBLOCKEND 141 70 989

;;							for(chark = charj; chark>0; chark--){
CLINEA 0000H 0000H 02DCH 0024H 002AH
	mov	r0,	r2
	add	r0,	#0ffh

;;							for(chark = charj; chark>0; chark--){
CLINEA 0000H 0000H 02DCH 0001H 000BH
_$L498 :
	st	r0,	NEAR _chark

;;							for(chark = charj; chark>0; chark--){
CLINEA 0000H 0000H 02DCH 001BH 0022H
	cmp	r0,	#00h
	ble	_$M125
	b	_$L264
_$M125 :

;;							chari++;
CLINEA 0000H 0000H 02E2H 0008H 000FH
	lea	OFFSET _chari
	inc	[ea]

;;							charj = 0;
CLINEA 0000H 0001H 02E3H 0008H 0011H
	mov	r0,	#00h

;;							while(I2C_BUFF[chari]!=0x20){
CLINEA 0000H 0000H 02E5H 0001H 000BH
	bal	_$L499

;;							while(I2C_BUFF[chari]!=0x20){
CLINEA 0000H 0000H 02E5H 0008H 0024H
_$L276 :
CBLOCK 141 73 741

;;								chari++;
CLINEA 0000H 0000H 02E6H 0009H 0010H
	lea	OFFSET _chari
	inc	[ea]

;;								charj++;
CLINEA 0000H 0000H 02E7H 0009H 0010H
	l	r0,	NEAR _charj
	add	r0,	#01h
CBLOCKEND 141 73 744

;;							while(I2C_BUFF[chari]!=0x20){
CLINEA 0000H 0000H 02E5H 0001H 000BH
_$L499 :
	st	r0,	NEAR _charj

;;							while(I2C_BUFF[chari]!=0x20){
CLINEA 0000H 0000H 02E5H 001BH 0022H
	l	r0,	NEAR _chari
	mov	r1,	#00h
	l	r0,	NEAR _I2C_BUFF[er0]
	cmp	r0,	#020h
	bne	_$L276

;;							for(chark = charj; chark>0; chark--){
CLINEA 0000H 0001H 02E9H 000CH 0019H
	l	r0,	NEAR _charj

;;							for(chark = charj; chark>0; chark--){
CLINEA 0000H 0000H 02E9H 0001H 000BH
	bal	_$L500

;;							for(chark = charj; chark>0; chark--){
CLINEA 0000H 0000H 02E9H 0024H 002AH
_$L280 :
CBLOCK 141 74 745

;;								if(chark == 3){Data1Str_temp = (I2C_BUFF[chari-chark]-0x30)*100;}
CLINEA 0000H 0001H 02EAH 0009H 0049H
	cmp	r0,	#03h
	bne	_$L284
CBLOCK 141 75 746
	l	r0,	NEAR _chari
	mov	r1,	#00h
	l	r2,	NEAR _chark
	mov	r3,	#00h
	sub	r0,	r2
	subc	r1,	r3
	l	r0,	NEAR _I2C_BUFF[er0]
	add	r0,	#0d0h
	mov	r1,	r0
	sll	r1,	#01h
	add	r1,	r0
	sll	r1,	#03h
	add	r1,	r0
	sll	r1,	#02h
	st	r1,	NEAR _Data1Str_temp

;;								else if(chark == 2){Data1Str_temp = (I2C_BUFF[chari-chark]-0x30)*10;}
CLINEA 0000H 0001H 02EBH 0009H 004DH
	bal	_$L289
_$L284 :
	cmp	r0,	#02h
	bne	_$L287
CBLOCK 141 76 747
	l	r0,	NEAR _chari
	mov	r1,	#00h
	l	r2,	NEAR _chark
	mov	r3,	#00h
	sub	r0,	r2
	subc	r1,	r3
	l	r0,	NEAR _I2C_BUFF[er0]
	add	r0,	#0d0h
	mov	r1,	r0
	sll	r1,	#02h
	add	r1,	r0
	sll	r1,	#01h
	st	r1,	NEAR _Data1Str_temp
CBLOCKEND 141 76 747

;;								else {Data1Str_temp = (I2C_BUFF[chari-chark]-0x30);}
CLINEA 0000H 0001H 02ECH 0009H 003CH
	bal	_$L289
_$L287 :
CBLOCK 141 77 748
	l	r0,	NEAR _chari
	mov	r1,	#00h
	l	r2,	NEAR _chark
	mov	r3,	#00h
	sub	r0,	r2
	subc	r1,	r3
	l	r0,	NEAR _I2C_BUFF[er0]
	add	r0,	#0d0h
	st	r0,	NEAR _Data1Str_temp
CBLOCKEND 141 77 748
_$L289 :

;;								Data1Str += Data1Str_temp;
CLINEA 0000H 0001H 02EDH 0009H 0022H
	l	r0,	NEAR _Data1Str
	l	r1,	NEAR _Data1Str_temp
	add	r0,	r1
	st	r0,	NEAR _Data1Str
CBLOCKEND 141 74 750
CBLOCKEND 141 75 989

;;							for(chark = charj; chark>0; chark--){
CLINEA 0000H 0000H 02E9H 0024H 002AH
	mov	r0,	r2
	add	r0,	#0ffh

;;							for(chark = charj; chark>0; chark--){
CLINEA 0000H 0000H 02E9H 0001H 000BH
_$L500 :
	st	r0,	NEAR _chark

;;							for(chark = charj; chark>0; chark--){
CLINEA 0000H 0000H 02E9H 001BH 0022H
	cmp	r0,	#00h
	ble	_$M126
	b	_$L280
_$M126 :

;;							chari++;
CLINEA 0000H 0000H 02EFH 0008H 000FH
	lea	OFFSET _chari
	inc	[ea]

;;							charj = 0;
CLINEA 0000H 0001H 02F0H 0008H 0011H
	mov	r0,	#00h

;;							while(I2C_BUFF[chari]!=0x20){
CLINEA 0000H 0000H 02F2H 0001H 000BH
	bal	_$L501

;;							while(I2C_BUFF[chari]!=0x20){
CLINEA 0000H 0000H 02F2H 0008H 0024H
_$L292 :
CBLOCK 141 78 754

;;								chari++;
CLINEA 0000H 0000H 02F3H 0009H 0010H
	lea	OFFSET _chari
	inc	[ea]

;;								charj++;
CLINEA 0000H 0000H 02F4H 0009H 0010H
	l	r0,	NEAR _charj
	add	r0,	#01h
CBLOCKEND 141 78 757

;;							while(I2C_BUFF[chari]!=0x20){
CLINEA 0000H 0000H 02F2H 0001H 000BH
_$L501 :
	st	r0,	NEAR _charj

;;							while(I2C_BUFF[chari]!=0x20){
CLINEA 0000H 0000H 02F2H 001BH 0022H
	l	r0,	NEAR _chari
	mov	r1,	#00h
	l	r0,	NEAR _I2C_BUFF[er0]
	cmp	r0,	#020h
	bne	_$L292

;;							for(chark = charj; chark>0; chark--){
CLINEA 0000H 0001H 02F6H 000CH 0019H
	l	r0,	NEAR _charj

;;							for(chark = charj; chark>0; chark--){
CLINEA 0000H 0000H 02F6H 0001H 000BH
	bal	_$L502

;;							for(chark = charj; chark>0; chark--){
CLINEA 0000H 0000H 02F6H 0024H 002AH
_$L296 :
CBLOCK 141 79 758

;;								if(chark == 3){Data2Str_temp = (I2C_BUFF[chari-chark]-0x30)*100;}
CLINEA 0000H 0001H 02F7H 0009H 0049H
	cmp	r0,	#03h
	bne	_$L300
CBLOCK 141 80 759
	l	r0,	NEAR _chari
	mov	r1,	#00h
	l	r2,	NEAR _chark
	mov	r3,	#00h
	sub	r0,	r2
	subc	r1,	r3
	l	r0,	NEAR _I2C_BUFF[er0]
	add	r0,	#0d0h
	mov	r1,	r0
	sll	r1,	#01h
	add	r1,	r0
	sll	r1,	#03h
	add	r1,	r0
	sll	r1,	#02h
	st	r1,	NEAR _Data2Str_temp

;;								else if(chark == 2){Data2Str_temp = (I2C_BUFF[chari-chark]-0x30)*10;}
CLINEA 0000H 0001H 02F8H 0009H 004DH
	bal	_$L305
_$L300 :
	cmp	r0,	#02h
	bne	_$L303
CBLOCK 141 81 760
	l	r0,	NEAR _chari
	mov	r1,	#00h
	l	r2,	NEAR _chark
	mov	r3,	#00h
	sub	r0,	r2
	subc	r1,	r3
	l	r0,	NEAR _I2C_BUFF[er0]
	add	r0,	#0d0h
	mov	r1,	r0
	sll	r1,	#02h
	add	r1,	r0
	sll	r1,	#01h
	st	r1,	NEAR _Data2Str_temp
CBLOCKEND 141 81 760

;;								else {Data2Str_temp = (I2C_BUFF[chari-chark]-0x30);}
CLINEA 0000H 0001H 02F9H 0009H 003CH
	bal	_$L305
_$L303 :
CBLOCK 141 82 761
	l	r0,	NEAR _chari
	mov	r1,	#00h
	l	r2,	NEAR _chark
	mov	r3,	#00h
	sub	r0,	r2
	subc	r1,	r3
	l	r0,	NEAR _I2C_BUFF[er0]
	add	r0,	#0d0h
	st	r0,	NEAR _Data2Str_temp
CBLOCKEND 141 82 761
_$L305 :

;;								Data2Str += Data2Str_temp;
CLINEA 0000H 0001H 02FAH 0009H 0022H
	l	r0,	NEAR _Data2Str
	l	r1,	NEAR _Data2Str_temp
	add	r0,	r1
	st	r0,	NEAR _Data2Str
CBLOCKEND 141 79 763
CBLOCKEND 141 80 989

;;							for(chark = charj; chark>0; chark--){
CLINEA 0000H 0000H 02F6H 0024H 002AH
	mov	r0,	r2
	add	r0,	#0ffh

;;							for(chark = charj; chark>0; chark--){
CLINEA 0000H 0000H 02F6H 0001H 000BH
_$L502 :
	st	r0,	NEAR _chark

;;							for(chark = charj; chark>0; chark--){
CLINEA 0000H 0000H 02F6H 001BH 0022H
	cmp	r0,	#00h
	ble	_$M127
	b	_$L296
_$M127 :

;;							chari++;
CLINEA 0000H 0000H 02FCH 0008H 000FH
	lea	OFFSET _chari
	inc	[ea]

;;							charj = 0;
CLINEA 0000H 0001H 02FDH 0008H 0011H
	mov	r0,	#00h

;;							while(I2C_BUFF[chari]!=0x20){
CLINEA 0000H 0000H 02FFH 0001H 000BH
	bal	_$L503

;;							while(I2C_BUFF[chari]!=0x20){
CLINEA 0000H 0000H 02FFH 0008H 0024H
_$L308 :
CBLOCK 141 83 767

;;								chari++;
CLINEA 0000H 0000H 0300H 0009H 0010H
	lea	OFFSET _chari
	inc	[ea]

;;								charj++;
CLINEA 0000H 0000H 0301H 0009H 0010H
	l	r0,	NEAR _charj
	add	r0,	#01h
CBLOCKEND 141 83 770

;;							while(I2C_BUFF[chari]!=0x20){
CLINEA 0000H 0000H 02FFH 0001H 000BH
_$L503 :
	st	r0,	NEAR _charj

;;							while(I2C_BUFF[chari]!=0x20){
CLINEA 0000H 0000H 02FFH 001BH 0022H
	l	r0,	NEAR _chari
	mov	r1,	#00h
	l	r0,	NEAR _I2C_BUFF[er0]
	cmp	r0,	#020h
	bne	_$L308

;;							for(chark = charj; chark>0; chark--){
CLINEA 0000H 0001H 0303H 000CH 0019H
	l	r0,	NEAR _charj

;;							for(chark = charj; chark>0; chark--){
CLINEA 0000H 0000H 0303H 0001H 000BH
	bal	_$L504

;;							for(chark = charj; chark>0; chark--){
CLINEA 0000H 0000H 0303H 0024H 002AH
_$L312 :
CBLOCK 141 84 771

;;								if(chark == 3){Data3Str_temp = (I2C_BUFF[chari-chark]-0x30)*100;}
CLINEA 0000H 0001H 0304H 0009H 0049H
	cmp	r0,	#03h
	bne	_$L316
CBLOCK 141 85 772
	l	r0,	NEAR _chari
	mov	r1,	#00h
	l	r2,	NEAR _chark
	mov	r3,	#00h
	sub	r0,	r2
	subc	r1,	r3
	l	r0,	NEAR _I2C_BUFF[er0]
	add	r0,	#0d0h
	mov	r1,	r0
	sll	r1,	#01h
	add	r1,	r0
	sll	r1,	#03h
	add	r1,	r0
	sll	r1,	#02h
	st	r1,	NEAR _Data3Str_temp

;;								else if(chark == 2){Data3Str_temp = (I2C_BUFF[chari-chark]-0x30)*10;}
CLINEA 0000H 0001H 0305H 0009H 004DH
	bal	_$L321
_$L316 :
	cmp	r0,	#02h
	bne	_$L319
CBLOCK 141 86 773
	l	r0,	NEAR _chari
	mov	r1,	#00h
	l	r2,	NEAR _chark
	mov	r3,	#00h
	sub	r0,	r2
	subc	r1,	r3
	l	r0,	NEAR _I2C_BUFF[er0]
	add	r0,	#0d0h
	mov	r1,	r0
	sll	r1,	#02h
	add	r1,	r0
	sll	r1,	#01h
	st	r1,	NEAR _Data3Str_temp
CBLOCKEND 141 86 773

;;								else {Data3Str_temp = (I2C_BUFF[chari-chark]-0x30);}
CLINEA 0000H 0001H 0306H 0009H 003CH
	bal	_$L321
_$L319 :
CBLOCK 141 87 774
	l	r0,	NEAR _chari
	mov	r1,	#00h
	l	r2,	NEAR _chark
	mov	r3,	#00h
	sub	r0,	r2
	subc	r1,	r3
	l	r0,	NEAR _I2C_BUFF[er0]
	add	r0,	#0d0h
	st	r0,	NEAR _Data3Str_temp
CBLOCKEND 141 87 774
_$L321 :

;;								Data3Str += Data3Str_temp;
CLINEA 0000H 0001H 0307H 0009H 0022H
	l	r0,	NEAR _Data3Str
	l	r1,	NEAR _Data3Str_temp
	add	r0,	r1
	st	r0,	NEAR _Data3Str
CBLOCKEND 141 84 776
CBLOCKEND 141 85 989

;;							for(chark = charj; chark>0; chark--){
CLINEA 0000H 0000H 0303H 0024H 002AH
	mov	r0,	r2
	add	r0,	#0ffh

;;							for(chark = charj; chark>0; chark--){
CLINEA 0000H 0000H 0303H 0001H 000BH
_$L504 :
	st	r0,	NEAR _chark

;;							for(chark = charj; chark>0; chark--){
CLINEA 0000H 0000H 0303H 001BH 0022H
	cmp	r0,	#00h
	ble	_$M128
	b	_$L312
_$M128 :

;;							chari++;
CLINEA 0000H 0000H 0309H 0008H 000FH
	lea	OFFSET _chari
	inc	[ea]

;;							charj = 0;
CLINEA 0000H 0001H 030AH 0008H 0011H
	mov	r0,	#00h

;;							while(I2C_BUFF[chari]!=0x20){
CLINEA 0000H 0000H 030CH 0001H 000BH
	bal	_$L505

;;							while(I2C_BUFF[chari]!=0x20){
CLINEA 0000H 0000H 030CH 0008H 0024H
_$L324 :
CBLOCK 141 88 780

;;								chari++;
CLINEA 0000H 0000H 030DH 0009H 0010H
	lea	OFFSET _chari
	inc	[ea]

;;								charj++;
CLINEA 0000H 0000H 030EH 0009H 0010H
	l	r0,	NEAR _charj
	add	r0,	#01h
CBLOCKEND 141 88 783

;;							while(I2C_BUFF[chari]!=0x20){
CLINEA 0000H 0000H 030CH 0001H 000BH
_$L505 :
	st	r0,	NEAR _charj

;;							while(I2C_BUFF[chari]!=0x20){
CLINEA 0000H 0000H 030CH 001BH 0022H
	l	r0,	NEAR _chari
	mov	r1,	#00h
	l	r0,	NEAR _I2C_BUFF[er0]
	cmp	r0,	#020h
	bne	_$L324

;;							for(chark = charj; chark>0; chark--){
CLINEA 0000H 0001H 0310H 000CH 0019H
	l	r0,	NEAR _charj

;;							for(chark = charj; chark>0; chark--){
CLINEA 0000H 0000H 0310H 0001H 000BH
	bal	_$L506

;;							for(chark = charj; chark>0; chark--){
CLINEA 0000H 0000H 0310H 0024H 002AH
_$L328 :
CBLOCK 141 89 784

;;								if(chark == 3){Data4Str_temp = (I2C_BUFF[chari-chark]-0x30)*100;}
CLINEA 0000H 0001H 0311H 0009H 0049H
	cmp	r0,	#03h
	bne	_$L332
CBLOCK 141 90 785
	l	r0,	NEAR _chari
	mov	r1,	#00h
	l	r2,	NEAR _chark
	mov	r3,	#00h
	sub	r0,	r2
	subc	r1,	r3
	l	r0,	NEAR _I2C_BUFF[er0]
	add	r0,	#0d0h
	mov	r1,	r0
	sll	r1,	#01h
	add	r1,	r0
	sll	r1,	#03h
	add	r1,	r0
	sll	r1,	#02h
	st	r1,	NEAR _Data4Str_temp

;;								else if(chark == 2){Data4Str_temp = (I2C_BUFF[chari-chark]-0x30)*10;}
CLINEA 0000H 0001H 0312H 0009H 004DH
	bal	_$L337
_$L332 :
	cmp	r0,	#02h
	bne	_$L335
CBLOCK 141 91 786
	l	r0,	NEAR _chari
	mov	r1,	#00h
	l	r2,	NEAR _chark
	mov	r3,	#00h
	sub	r0,	r2
	subc	r1,	r3
	l	r0,	NEAR _I2C_BUFF[er0]
	add	r0,	#0d0h
	mov	r1,	r0
	sll	r1,	#02h
	add	r1,	r0
	sll	r1,	#01h
	st	r1,	NEAR _Data4Str_temp
CBLOCKEND 141 91 786

;;								else {Data4Str_temp = (I2C_BUFF[chari-chark]-0x30);}
CLINEA 0000H 0001H 0313H 0009H 003CH
	bal	_$L337
_$L335 :
CBLOCK 141 92 787
	l	r0,	NEAR _chari
	mov	r1,	#00h
	l	r2,	NEAR _chark
	mov	r3,	#00h
	sub	r0,	r2
	subc	r1,	r3
	l	r0,	NEAR _I2C_BUFF[er0]
	add	r0,	#0d0h
	st	r0,	NEAR _Data4Str_temp
CBLOCKEND 141 92 787
_$L337 :

;;								Data4Str += Data4Str_temp;
CLINEA 0000H 0001H 0314H 0009H 0022H
	l	r0,	NEAR _Data4Str
	l	r1,	NEAR _Data4Str_temp
	add	r0,	r1
	st	r0,	NEAR _Data4Str
CBLOCKEND 141 89 789
CBLOCKEND 141 90 989

;;							for(chark = charj; chark>0; chark--){
CLINEA 0000H 0000H 0310H 0024H 002AH
	mov	r0,	r2
	add	r0,	#0ffh

;;							for(chark = charj; chark>0; chark--){
CLINEA 0000H 0000H 0310H 0001H 000BH
_$L506 :
	st	r0,	NEAR _chark

;;							for(chark = charj; chark>0; chark--){
CLINEA 0000H 0000H 0310H 001BH 0022H
	cmp	r0,	#00h
	ble	_$M129
	b	_$L328
_$M129 :

;;							chari++;
CLINEA 0000H 0000H 0316H 0008H 000FH
	lea	OFFSET _chari
	inc	[ea]

;;							charj = 0;
CLINEA 0000H 0001H 0317H 0008H 0011H
	mov	r0,	#00h

;;							while(I2C_BUFF[chari]!=0x20){
CLINEA 0000H 0000H 0319H 0001H 000BH
	bal	_$L507

;;							while(I2C_BUFF[chari]!=0x20){
CLINEA 0000H 0000H 0319H 0008H 0024H
_$L340 :
CBLOCK 141 93 793

;;								chari++;
CLINEA 0000H 0000H 031AH 0009H 0010H
	lea	OFFSET _chari
	inc	[ea]

;;								charj++;
CLINEA 0000H 0000H 031BH 0009H 0010H
	l	r0,	NEAR _charj
	add	r0,	#01h
CBLOCKEND 141 93 796

;;							while(I2C_BUFF[chari]!=0x20){
CLINEA 0000H 0000H 0319H 0001H 000BH
_$L507 :
	st	r0,	NEAR _charj

;;							while(I2C_BUFF[chari]!=0x20){
CLINEA 0000H 0000H 0319H 001BH 0022H
	l	r0,	NEAR _chari
	mov	r1,	#00h
	l	r0,	NEAR _I2C_BUFF[er0]
	cmp	r0,	#020h
	bne	_$L340

;;							for(chark = charj; chark>0; chark--){
CLINEA 0000H 0001H 031DH 000CH 0019H
	l	r0,	NEAR _charj

;;							for(chark = charj; chark>0; chark--){
CLINEA 0000H 0000H 031DH 0001H 000BH
	bal	_$L508

;;							for(chark = charj; chark>0; chark--){
CLINEA 0000H 0000H 031DH 0024H 002AH
_$L344 :
CBLOCK 141 94 797

;;								if(chark == 3){Data5Str_temp = (I2C_BUFF[chari-chark]-0x30)*100;}
CLINEA 0000H 0001H 031EH 0009H 0049H
	cmp	r0,	#03h
	bne	_$L348
CBLOCK 141 95 798
	l	r0,	NEAR _chari
	mov	r1,	#00h
	l	r2,	NEAR _chark
	mov	r3,	#00h
	sub	r0,	r2
	subc	r1,	r3
	l	r0,	NEAR _I2C_BUFF[er0]
	add	r0,	#0d0h
	mov	r1,	r0
	sll	r1,	#01h
	add	r1,	r0
	sll	r1,	#03h
	add	r1,	r0
	sll	r1,	#02h
	st	r1,	NEAR _Data5Str_temp

;;								else if(chark == 2){Data5Str_temp = (I2C_BUFF[chari-chark]-0x30)*10;}
CLINEA 0000H 0001H 031FH 0009H 004DH
	bal	_$L353
_$L348 :
	cmp	r0,	#02h
	bne	_$L351
CBLOCK 141 96 799
	l	r0,	NEAR _chari
	mov	r1,	#00h
	l	r2,	NEAR _chark
	mov	r3,	#00h
	sub	r0,	r2
	subc	r1,	r3
	l	r0,	NEAR _I2C_BUFF[er0]
	add	r0,	#0d0h
	mov	r1,	r0
	sll	r1,	#02h
	add	r1,	r0
	sll	r1,	#01h
	st	r1,	NEAR _Data5Str_temp
CBLOCKEND 141 96 799

;;								else {Data5Str_temp = (I2C_BUFF[chari-chark]-0x30);}
CLINEA 0000H 0001H 0320H 0009H 003CH
	bal	_$L353
_$L351 :
CBLOCK 141 97 800
	l	r0,	NEAR _chari
	mov	r1,	#00h
	l	r2,	NEAR _chark
	mov	r3,	#00h
	sub	r0,	r2
	subc	r1,	r3
	l	r0,	NEAR _I2C_BUFF[er0]
	add	r0,	#0d0h
	st	r0,	NEAR _Data5Str_temp
CBLOCKEND 141 97 800
_$L353 :

;;								Data5Str += Data5Str_temp;
CLINEA 0000H 0001H 0321H 0009H 0022H
	l	r0,	NEAR _Data5Str
	l	r1,	NEAR _Data5Str_temp
	add	r0,	r1
	st	r0,	NEAR _Data5Str
CBLOCKEND 141 94 802
CBLOCKEND 141 95 989

;;							for(chark = charj; chark>0; chark--){
CLINEA 0000H 0000H 031DH 0024H 002AH
	mov	r0,	r2
	add	r0,	#0ffh

;;							for(chark = charj; chark>0; chark--){
CLINEA 0000H 0000H 031DH 0001H 000BH
_$L508 :
	st	r0,	NEAR _chark

;;							for(chark = charj; chark>0; chark--){
CLINEA 0000H 0000H 031DH 001BH 0022H
	cmp	r0,	#00h
	ble	_$M130
	b	_$L344
_$M130 :

;;							chari++;
CLINEA 0000H 0000H 0323H 0008H 000FH
	lea	OFFSET _chari
	inc	[ea]

;;							charj = 0;
CLINEA 0000H 0001H 0324H 0008H 0011H
	mov	r0,	#00h

;;							while(I2C_BUFF[chari]!=0x20){
CLINEA 0000H 0000H 0326H 0001H 000BH
	bal	_$L509

;;							while(I2C_BUFF[chari]!=0x20){
CLINEA 0000H 0000H 0326H 0008H 0024H
_$L356 :
CBLOCK 141 98 806

;;								chari++;
CLINEA 0000H 0000H 0327H 0009H 0010H
	lea	OFFSET _chari
	inc	[ea]

;;								charj++;
CLINEA 0000H 0000H 0328H 0009H 0010H
	l	r0,	NEAR _charj
	add	r0,	#01h
CBLOCKEND 141 98 809

;;							while(I2C_BUFF[chari]!=0x20){
CLINEA 0000H 0000H 0326H 0001H 000BH
_$L509 :
	st	r0,	NEAR _charj

;;							while(I2C_BUFF[chari]!=0x20){
CLINEA 0000H 0000H 0326H 001BH 0022H
	l	r0,	NEAR _chari
	mov	r1,	#00h
	l	r0,	NEAR _I2C_BUFF[er0]
	cmp	r0,	#020h
	bne	_$L356

;;							for(chark = charj; chark>0; chark--){
CLINEA 0000H 0001H 032AH 000CH 0019H
	l	r0,	NEAR _charj

;;							for(chark = charj; chark>0; chark--){
CLINEA 0000H 0000H 032AH 0001H 000BH
	bal	_$L510

;;							for(chark = charj; chark>0; chark--){
CLINEA 0000H 0000H 032AH 0024H 002AH
_$L360 :
CBLOCK 141 99 810

;;								if(chark == 3){Data6Str_temp = (I2C_BUFF[chari-chark]-0x30)*100;}
CLINEA 0000H 0001H 032BH 0009H 0049H
	cmp	r0,	#03h
	bne	_$L364
CBLOCK 141 100 811
	l	r0,	NEAR _chari
	mov	r1,	#00h
	l	r2,	NEAR _chark
	mov	r3,	#00h
	sub	r0,	r2
	subc	r1,	r3
	l	r0,	NEAR _I2C_BUFF[er0]
	add	r0,	#0d0h
	mov	r1,	r0
	sll	r1,	#01h
	add	r1,	r0
	sll	r1,	#03h
	add	r1,	r0
	sll	r1,	#02h
	st	r1,	NEAR _Data6Str_temp

;;								else if(chark == 2){Data6Str_temp = (I2C_BUFF[chari-chark]-0x30)*10;}
CLINEA 0000H 0001H 032CH 0009H 004DH
	bal	_$L369
_$L364 :
	cmp	r0,	#02h
	bne	_$L367
CBLOCK 141 101 812
	l	r0,	NEAR _chari
	mov	r1,	#00h
	l	r2,	NEAR _chark
	mov	r3,	#00h
	sub	r0,	r2
	subc	r1,	r3
	l	r0,	NEAR _I2C_BUFF[er0]
	add	r0,	#0d0h
	mov	r1,	r0
	sll	r1,	#02h
	add	r1,	r0
	sll	r1,	#01h
	st	r1,	NEAR _Data6Str_temp
CBLOCKEND 141 101 812

;;								else {Data6Str_temp = (I2C_BUFF[chari-chark]-0x30);}
CLINEA 0000H 0001H 032DH 0009H 003CH
	bal	_$L369
_$L367 :
CBLOCK 141 102 813
	l	r0,	NEAR _chari
	mov	r1,	#00h
	l	r2,	NEAR _chark
	mov	r3,	#00h
	sub	r0,	r2
	subc	r1,	r3
	l	r0,	NEAR _I2C_BUFF[er0]
	add	r0,	#0d0h
	st	r0,	NEAR _Data6Str_temp
CBLOCKEND 141 102 813
_$L369 :

;;								Data6Str += Data6Str_temp;
CLINEA 0000H 0001H 032EH 0009H 0022H
	l	r0,	NEAR _Data6Str
	l	r1,	NEAR _Data6Str_temp
	add	r0,	r1
	st	r0,	NEAR _Data6Str
CBLOCKEND 141 99 815
CBLOCKEND 141 100 989

;;							for(chark = charj; chark>0; chark--){
CLINEA 0000H 0000H 032AH 0024H 002AH
	mov	r0,	r2
	add	r0,	#0ffh

;;							for(chark = charj; chark>0; chark--){
CLINEA 0000H 0000H 032AH 0001H 000BH
_$L510 :
	st	r0,	NEAR _chark

;;							for(chark = charj; chark>0; chark--){
CLINEA 0000H 0000H 032AH 001BH 0022H
	cmp	r0,	#00h
	ble	_$M131
	b	_$L360
_$M131 :

;;							chari++;
CLINEA 0000H 0000H 0330H 0008H 000FH
	lea	OFFSET _chari
	inc	[ea]

;;							charj = 0;
CLINEA 0000H 0001H 0331H 0008H 0011H
	mov	r0,	#00h

;;							while(I2C_BUFF[chari]!=0x20){
CLINEA 0000H 0000H 0333H 0001H 000BH
	bal	_$L511

;;							while(I2C_BUFF[chari]!=0x20){
CLINEA 0000H 0000H 0333H 0008H 0024H
_$L372 :
CBLOCK 141 103 819

;;								chari++;
CLINEA 0000H 0000H 0334H 0009H 0010H
	lea	OFFSET _chari
	inc	[ea]

;;								charj++;
CLINEA 0000H 0000H 0335H 0009H 0010H
	l	r0,	NEAR _charj
	add	r0,	#01h
CBLOCKEND 141 103 822

;;							while(I2C_BUFF[chari]!=0x20){
CLINEA 0000H 0000H 0333H 0001H 000BH
_$L511 :
	st	r0,	NEAR _charj

;;							while(I2C_BUFF[chari]!=0x20){
CLINEA 0000H 0000H 0333H 001BH 0022H
	l	r0,	NEAR _chari
	mov	r1,	#00h
	l	r0,	NEAR _I2C_BUFF[er0]
	cmp	r0,	#020h
	bne	_$L372

;;							for(chark = charj; chark>0; chark--){
CLINEA 0000H 0001H 0337H 000CH 0019H
	l	r0,	NEAR _charj

;;							for(chark = charj; chark>0; chark--){
CLINEA 0000H 0000H 0337H 0001H 000BH
	bal	_$L512

;;							for(chark = charj; chark>0; chark--){
CLINEA 0000H 0000H 0337H 0024H 002AH
_$L376 :
CBLOCK 141 104 823

;;								if(chark == 3){Data7Str_temp = (I2C_BUFF[chari-chark]-0x30)*100;}
CLINEA 0000H 0001H 0338H 0009H 0049H
	cmp	r0,	#03h
	bne	_$L380
CBLOCK 141 105 824
	l	r0,	NEAR _chari
	mov	r1,	#00h
	l	r2,	NEAR _chark
	mov	r3,	#00h
	sub	r0,	r2
	subc	r1,	r3
	l	r0,	NEAR _I2C_BUFF[er0]
	add	r0,	#0d0h
	mov	r1,	r0
	sll	r1,	#01h
	add	r1,	r0
	sll	r1,	#03h
	add	r1,	r0
	sll	r1,	#02h
	st	r1,	NEAR _Data7Str_temp

;;								else if(chark == 2){Data7Str_temp = (I2C_BUFF[chari-chark]-0x30)*10;}
CLINEA 0000H 0001H 0339H 0009H 004DH
	bal	_$L385
_$L380 :
	cmp	r0,	#02h
	bne	_$L383
CBLOCK 141 106 825
	l	r0,	NEAR _chari
	mov	r1,	#00h
	l	r2,	NEAR _chark
	mov	r3,	#00h
	sub	r0,	r2
	subc	r1,	r3
	l	r0,	NEAR _I2C_BUFF[er0]
	add	r0,	#0d0h
	mov	r1,	r0
	sll	r1,	#02h
	add	r1,	r0
	sll	r1,	#01h
	st	r1,	NEAR _Data7Str_temp
CBLOCKEND 141 106 825

;;								else {Data7Str_temp = (I2C_BUFF[chari-chark]-0x30);}
CLINEA 0000H 0001H 033AH 0009H 003CH
	bal	_$L385
_$L383 :
CBLOCK 141 107 826
	l	r0,	NEAR _chari
	mov	r1,	#00h
	l	r2,	NEAR _chark
	mov	r3,	#00h
	sub	r0,	r2
	subc	r1,	r3
	l	r0,	NEAR _I2C_BUFF[er0]
	add	r0,	#0d0h
	st	r0,	NEAR _Data7Str_temp
CBLOCKEND 141 107 826
_$L385 :

;;								Data7Str += Data7Str_temp;
CLINEA 0000H 0001H 033BH 0009H 0022H
	l	r0,	NEAR _Data7Str
	l	r1,	NEAR _Data7Str_temp
	add	r0,	r1
	st	r0,	NEAR _Data7Str
CBLOCKEND 141 104 828
CBLOCKEND 141 105 989

;;							for(chark = charj; chark>0; chark--){
CLINEA 0000H 0000H 0337H 0024H 002AH
	mov	r0,	r2
	add	r0,	#0ffh

;;							for(chark = charj; chark>0; chark--){
CLINEA 0000H 0000H 0337H 0001H 000BH
_$L512 :
	st	r0,	NEAR _chark

;;							for(chark = charj; chark>0; chark--){
CLINEA 0000H 0000H 0337H 001BH 0022H
	cmp	r0,	#00h
	ble	_$M132
	b	_$L376
_$M132 :

;;							chari++;
CLINEA 0000H 0000H 033DH 0008H 000FH
	lea	OFFSET _chari
	inc	[ea]

;;							charj = 0;							
CLINEA 0000H 0001H 033EH 0008H 0018H
	mov	r0,	#00h
	st	r0,	NEAR _charj

;;							I2CSendInfo[0] = Data0Str;
CLINEA 0000H 0001H 0341H 0008H 0021H
	l	r0,	NEAR _Data0Str
	st	r0,	NEAR _I2CSendInfo

;;							I2CSendInfo[1] = Data1Str;
CLINEA 0000H 0001H 0342H 0008H 0021H
	l	r0,	NEAR _Data1Str
	st	r0,	NEAR _I2CSendInfo+01h

;;							I2CSendInfo[2] = Data2Str;
CLINEA 0000H 0001H 0343H 0008H 0021H
	l	r0,	NEAR _Data2Str
	st	r0,	NEAR _I2CSendInfo+02h

;;							I2CSendInfo[3] = Data3Str;
CLINEA 0000H 0001H 0344H 0008H 0021H
	l	r0,	NEAR _Data3Str
	st	r0,	NEAR _I2CSendInfo+03h

;;							I2CSendInfo[4] = Data4Str;
CLINEA 0000H 0001H 0345H 0008H 0021H
	l	r0,	NEAR _Data4Str
	st	r0,	NEAR _I2CSendInfo+04h

;;							I2CSendInfo[5] = Data5Str;
CLINEA 0000H 0001H 0346H 0008H 0021H
	l	r0,	NEAR _Data5Str
	st	r0,	NEAR _I2CSendInfo+05h

;;							I2CSendInfo[6] = Data6Str;
CLINEA 0000H 0001H 0347H 0008H 0021H
	l	r0,	NEAR _Data6Str
	st	r0,	NEAR _I2CSendInfo+06h

;;							I2CSendInfo[7] = Data7Str;
CLINEA 0000H 0001H 0348H 0008H 0021H
	l	r0,	NEAR _Data7Str
	st	r0,	NEAR _I2CSendInfo+07h

;;							Data0Str = Data1Str = Data2Str = Data3Str = Data4Str = Data5Str = Data6Str = Data7Str = 0;
CLINEA 0000H 0001H 034BH 0008H 0061H
	mov	r0,	#00h
	st	r0,	NEAR _Data7Str
	st	r0,	NEAR _Data6Str
	st	r0,	NEAR _Data5Str
	st	r0,	NEAR _Data4Str
	st	r0,	NEAR _Data3Str
	st	r0,	NEAR _Data2Str
	st	r0,	NEAR _Data1Str
	st	r0,	NEAR _Data0Str

;;							_flgI2CFin = 0;														//reset I2C completed flag
CLINEA 0000H 0001H 034EH 0008H 003EH
	st	r0,	NEAR __flgI2CFin

;;							i2c_stop();															//Make sure I2C is not currently running
CLINEA 0000H 0001H 034FH 0008H 0049H
	bl	_i2c_stop

;;							i2c_startSend( I2CAdd, &I2CSendInfo, I2CNumBytes, &I2CSendInfo, 0, (cbfI2c)_funcI2CFin);		//Begin I2C Recieve Command
CLINEA 0000H 0001H 0350H 0008H 007CH
	mov	r0,	#BYTE1 OFFSET __funcI2CFin
	mov	r1,	#BYTE2 OFFSET __funcI2CFin
	push	er0
	mov	er0,	#0 
	push	er0
	mov	r0,	#BYTE1 OFFSET _I2CSendInfo
	mov	r1,	#BYTE2 OFFSET _I2CSendInfo
	push	er0
	l	r0,	NEAR _I2CNumBytes
	mov	r1,	#00h
	push	er0
	mov	r2,	#BYTE1 OFFSET _I2CSendInfo
	mov	r3,	#BYTE2 OFFSET _I2CSendInfo
	l	r0,	NEAR _I2CAdd
	bl	_i2c_startSend
	add	sp,	#8 

;;							while(_flgI2CFin != 1){												//Wait for I2C commands to finish transfer
CLINEA 0000H 0000H 0351H 0001H 000BH
	bal	_$L513

;;							while(_flgI2CFin != 1){												//Wait for I2C commands to finish transfer
CLINEA 0000H 0000H 0351H 0008H 0054H
_$L388 :
CBLOCK 141 108 849

;;								NOP1000();
CLINEA 0000H 0001H 0352H 0009H 0012H
	bl	_NOP1000

;;								main_clrWDT();
CLINEA 0000H 0001H 0353H 0009H 0016H
	bl	_main_clrWDT
CBLOCKEND 141 108 852

;;							while(_flgI2CFin != 1){												//Wait for I2C commands to finish transfer
CLINEA 0000H 0000H 0351H 0001H 000BH
_$L513 :

;;							while(_flgI2CFin != 1){												//Wait for I2C commands to finish transfer
CLINEA 0000H 0000H 0351H 001BH 0022H
	l	r0,	NEAR __flgI2CFin
	cmp	r0,	#01h
	bne	_$L388

;;							I2CAdd = 0;
CLINEA 0000H 0001H 0357H 0008H 0012H
	mov	r0,	#00h
	st	r0,	NEAR _I2CAdd

;;							I2CNumBytes = 0;
CLINEA 0000H 0001H 0358H 0008H 0017H
	st	r0,	NEAR _I2CNumBytes

;;							chari = 0;
CLINEA 0000H 0001H 0359H 0008H 0011H
	st	r0,	NEAR _chari

;;							for(chari = 0; chari < 8; chari++){
CLINEA 0000H 0000H 035AH 0008H 002AH
_$L392 :
CBLOCK 141 109 858

;;								I2CSendInfo[chari] = 0;
CLINEA 0000H 0001H 035BH 0009H 001FH
	mov	r1,	#00h
	mov	r2,	#00h
	st	r2,	NEAR _I2CSendInfo[er0]
CBLOCKEND 141 109 860

;;							for(chari = 0; chari < 8; chari++){
CLINEA 0000H 0000H 035AH 0008H 002AH
	lea	OFFSET _chari
	inc	[ea]
	l	r0,	NEAR _chari

;;							for(chari = 0; chari < 8; chari++){
CLINEA 0000H 0000H 035AH 001BH 0022H
	cmp	r0,	#08h
	blt	_$L392

;;							_flgUartFin = 0;
CLINEA 0000H 0001H 035FH 0008H 0017H
	mov	r0,	#00h
	st	r0,	NEAR __flgUartFin

;;							uart_stop();
CLINEA 0000H 0001H 0360H 0008H 0013H
	bl	_uart_stop

;;							uart_startSend(I2C_TX_REC, 21, _funcUartFin);
CLINEA 0000H 0001H 0361H 0008H 0034H
	mov	r0,	#BYTE1 OFFSET __funcUartFin
	mov	r1,	#BYTE2 OFFSET __funcUartFin
	push	er0
	mov	er2,	#21
	mov	r0,	#BYTE1 OFFSET _I2C_TX_REC
	mov	r1,	#BYTE2 OFFSET _I2C_TX_REC
	bl	_uart_startSend
	add	sp,	#2 

;;							while(_flgUartFin != 1){
CLINEA 0000H 0000H 0362H 0001H 000BH
	bal	_$L514

;;							while(_flgUartFin != 1){
CLINEA 0000H 0000H 0362H 0008H 001FH
_$L398 :
CBLOCK 141 110 866

;;								NOP1000();
CLINEA 0000H 0001H 0363H 0009H 0012H
	bl	_NOP1000

;;								main_clrWDT();
CLINEA 0000H 0001H 0364H 0009H 0016H
	bl	_main_clrWDT
CBLOCKEND 141 110 869

;;							while(_flgUartFin != 1){
CLINEA 0000H 0000H 0362H 0001H 000BH
_$L514 :

;;							while(_flgUartFin != 1){
CLINEA 0000H 0000H 0362H 001BH 0022H
	l	r0,	NEAR __flgUartFin
	cmp	r0,	#01h
	bne	_$L398

;;							}
CLINEA 0000H 0000H 0365H 0008H 0008H
_$L397 :
CBLOCKEND 141 56 870
CBLOCKEND 141 55 871
CBLOCKEND 141 54 872
CBLOCKEND 141 53 873
CBLOCKEND 141 52 874

;;		if(RecWorld[0] == 0x49){			//if RECWORLD == "I2CRX"
CLINEA 0000H 0001H 036EH 0003H 0035H
	l	r0,	NEAR _RecWorld
	cmp	r0,	#049h
	beq	_$M133
	b	_$L12
_$M133 :
CBLOCK 141 111 878

;;			if(RecWorld[1] == 0x32){
CLINEA 0000H 0001H 036FH 0004H 001BH
	l	r0,	NEAR _RecWorld+01h
	cmp	r0,	#032h
	beq	_$M134
	b	_$L12
_$M134 :
CBLOCK 141 112 879

;;				if(RecWorld[2] == 0x43){
CLINEA 0000H 0001H 0370H 0005H 001CH
	l	r0,	NEAR _RecWorld+02h
	cmp	r0,	#043h
	beq	_$M135
	b	_$L12
_$M135 :
CBLOCK 141 113 880

;;					if(RecWorld[3] == 0x52){
CLINEA 0000H 0001H 0371H 0006H 001DH
	l	r0,	NEAR _RecWorld+03h
	cmp	r0,	#052h
	beq	_$M136
	b	_$L12
_$M136 :
CBLOCK 141 114 881

;;						if(RecWorld[4] == 0x58){
CLINEA 0000H 0001H 0372H 0007H 001EH
	l	r0,	NEAR _RecWorld+04h
	cmp	r0,	#058h
	beq	_$M137
	b	_$L12
_$M137 :
CBLOCK 141 115 882

;;							_flgUartFin = 0;
CLINEA 0000H 0001H 0375H 0008H 0017H
	mov	r0,	#00h
	st	r0,	NEAR __flgUartFin

;;							uart_stop();
CLINEA 0000H 0001H 0376H 0008H 0013H
	bl	_uart_stop

;;							uart_startReceive(I2C_BUFF, 46, _funcUartFin);
CLINEA 0000H 0001H 0377H 0008H 0035H
	mov	r0,	#BYTE1 OFFSET __funcUartFin
	mov	r1,	#BYTE2 OFFSET __funcUartFin
	push	er0
	mov	er2,	#46
	mov	r0,	#BYTE1 OFFSET _I2C_BUFF
	mov	r1,	#BYTE2 OFFSET _I2C_BUFF
	bl	_uart_startReceive
	add	sp,	#2 

;;							while(_flgUartFin != 1){
CLINEA 0000H 0000H 0378H 0001H 000BH
	bal	_$L515

;;							while(_flgUartFin != 1){
CLINEA 0000H 0000H 0378H 0008H 001FH
_$L412 :
CBLOCK 141 116 888

;;								NOP1000();
CLINEA 0000H 0001H 0379H 0009H 0012H
	bl	_NOP1000

;;								main_clrWDT();
CLINEA 0000H 0001H 037AH 0009H 0016H
	bl	_main_clrWDT
CBLOCKEND 141 116 891

;;							while(_flgUartFin != 1){
CLINEA 0000H 0000H 0378H 0001H 000BH
_$L515 :

;;							while(_flgUartFin != 1){
CLINEA 0000H 0000H 0378H 001BH 0022H
	l	r0,	NEAR __flgUartFin
	cmp	r0,	#01h
	bne	_$L412

;;							chari = 2;
CLINEA 0000H 0001H 037EH 0008H 0011H
	mov	r0,	#02h
	st	r0,	NEAR _chari

;;							charj = 0;
CLINEA 0000H 0001H 037FH 0008H 0011H
	mov	r0,	#00h
	st	r0,	NEAR _charj

;;							while(I2C_BUFF[chari]!=0x20){
CLINEA 0000H 0001H 0381H 0008H 0024H
	l	r0,	NEAR _I2C_BUFF+02h
	cmp	r0,	#020h
	beq	_$L415
_$L416 :
CBLOCK 141 117 897

;;								chari++;
CLINEA 0000H 0000H 0382H 0009H 0010H
	lea	OFFSET _chari
	inc	[ea]

;;								charj++;
CLINEA 0000H 0000H 0383H 0009H 0010H
	lea	OFFSET _charj
	inc	[ea]
CBLOCKEND 141 117 900

;;							while(I2C_BUFF[chari]!=0x20){
CLINEA 0000H 0000H 0381H 001BH 0022H
	l	r0,	NEAR _chari
	mov	r1,	#00h
	l	r0,	NEAR _I2C_BUFF[er0]
	cmp	r0,	#020h
	bne	_$L416

;;							}
CLINEA 0000H 0000H 0384H 0008H 0008H
_$L415 :

;;							for(chark = charj; chark>0; chark--){
CLINEA 0000H 0001H 0385H 000CH 0019H
	l	r0,	NEAR _charj

;;							for(chark = charj; chark>0; chark--){
CLINEA 0000H 0000H 0385H 0001H 000BH
	bal	_$L516

;;							for(chark = charj; chark>0; chark--){
CLINEA 0000H 0000H 0385H 0024H 002AH
_$L420 :
CBLOCK 141 118 901

;;								if(chark == 3){I2CAdd_temp = (I2C_BUFF[chari-chark]-0x30)*100;}
CLINEA 0000H 0001H 0386H 0009H 0047H
	cmp	r0,	#03h
	bne	_$L424
CBLOCK 141 119 902
	l	r0,	NEAR _chari
	mov	r1,	#00h
	l	r2,	NEAR _chark
	mov	r3,	#00h
	sub	r0,	r2
	subc	r1,	r3
	l	r0,	NEAR _I2C_BUFF[er0]
	add	r0,	#0d0h
	mov	r1,	r0
	sll	r1,	#01h
	add	r1,	r0
	sll	r1,	#03h
	add	r1,	r0
	sll	r1,	#02h
	st	r1,	NEAR _I2CAdd_temp

;;								else if(chark == 2){I2CAdd_temp = (I2C_BUFF[chari-chark]-0x30)*10;}
CLINEA 0000H 0001H 0387H 0009H 004BH
	bal	_$L429
_$L424 :
	cmp	r0,	#02h
	bne	_$L427
CBLOCK 141 120 903
	l	r0,	NEAR _chari
	mov	r1,	#00h
	l	r2,	NEAR _chark
	mov	r3,	#00h
	sub	r0,	r2
	subc	r1,	r3
	l	r0,	NEAR _I2C_BUFF[er0]
	add	r0,	#0d0h
	mov	r1,	r0
	sll	r1,	#02h
	add	r1,	r0
	sll	r1,	#01h
	st	r1,	NEAR _I2CAdd_temp
CBLOCKEND 141 120 903

;;								else {I2CAdd_temp = (I2C_BUFF[chari-chark]-0x30);}
CLINEA 0000H 0001H 0388H 0009H 003AH
	bal	_$L429
_$L427 :
CBLOCK 141 121 904
	l	r0,	NEAR _chari
	mov	r1,	#00h
	l	r2,	NEAR _chark
	mov	r3,	#00h
	sub	r0,	r2
	subc	r1,	r3
	l	r0,	NEAR _I2C_BUFF[er0]
	add	r0,	#0d0h
	st	r0,	NEAR _I2CAdd_temp
CBLOCKEND 141 121 904
_$L429 :

;;								I2CAdd += I2CAdd_temp;
CLINEA 0000H 0001H 0389H 0009H 001EH
	l	r0,	NEAR _I2CAdd
	l	r1,	NEAR _I2CAdd_temp
	add	r0,	r1
	st	r0,	NEAR _I2CAdd
CBLOCKEND 141 118 906
CBLOCKEND 141 119 989

;;							for(chark = charj; chark>0; chark--){
CLINEA 0000H 0000H 0385H 0024H 002AH
	mov	r0,	r2
	add	r0,	#0ffh

;;							for(chark = charj; chark>0; chark--){
CLINEA 0000H 0000H 0385H 0001H 000BH
_$L516 :
	st	r0,	NEAR _chark

;;							for(chark = charj; chark>0; chark--){
CLINEA 0000H 0000H 0385H 001BH 0022H
	cmp	r0,	#00h
	ble	_$M138
	b	_$L420
_$M138 :

;;							chari++;
CLINEA 0000H 0000H 038BH 0008H 000FH
	lea	OFFSET _chari
	inc	[ea]

;;							charj = 0;
CLINEA 0000H 0001H 038CH 0008H 0011H
	mov	r0,	#00h

;;							while(I2C_BUFF[chari]!=0x20){
CLINEA 0000H 0000H 038DH 0001H 000BH
	bal	_$L517

;;							while(I2C_BUFF[chari]!=0x20){
CLINEA 0000H 0000H 038DH 0008H 0024H
_$L432 :
CBLOCK 141 122 909

;;								chari++;
CLINEA 0000H 0000H 038EH 0009H 0010H
	lea	OFFSET _chari
	inc	[ea]

;;								charj++;
CLINEA 0000H 0000H 038FH 0009H 0010H
	l	r0,	NEAR _charj
	add	r0,	#01h
CBLOCKEND 141 122 912

;;							while(I2C_BUFF[chari]!=0x20){
CLINEA 0000H 0000H 038DH 0001H 000BH
_$L517 :
	st	r0,	NEAR _charj

;;							while(I2C_BUFF[chari]!=0x20){
CLINEA 0000H 0000H 038DH 001BH 0022H
	l	r0,	NEAR _chari
	mov	r1,	#00h
	l	r0,	NEAR _I2C_BUFF[er0]
	cmp	r0,	#020h
	bne	_$L432

;;							for(chark = charj; chark>0; chark--){
CLINEA 0000H 0001H 0391H 000CH 0019H
	l	r0,	NEAR _charj

;;							for(chark = charj; chark>0; chark--){
CLINEA 0000H 0000H 0391H 0001H 000BH
	bal	_$L518

;;							for(chark = charj; chark>0; chark--){
CLINEA 0000H 0000H 0391H 0024H 002AH
_$L436 :
CBLOCK 141 123 913

;;								if(chark == 3){I2CNumBytes_temp = (I2C_BUFF[chari-chark]-0x30)*100;}
CLINEA 0000H 0001H 0392H 0009H 004CH
	cmp	r0,	#03h
	bne	_$L440
CBLOCK 141 124 914
	l	r0,	NEAR _chari
	mov	r1,	#00h
	l	r2,	NEAR _chark
	mov	r3,	#00h
	sub	r0,	r2
	subc	r1,	r3
	l	r0,	NEAR _I2C_BUFF[er0]
	add	r0,	#0d0h
	mov	r1,	r0
	sll	r1,	#01h
	add	r1,	r0
	sll	r1,	#03h
	add	r1,	r0
	sll	r1,	#02h
	st	r1,	NEAR _I2CNumBytes_temp

;;								else if(chark == 2){I2CNumBytes_temp = (I2C_BUFF[chari-chark]-0x30)*10;}
CLINEA 0000H 0001H 0393H 0009H 0050H
	bal	_$L445
_$L440 :
	cmp	r0,	#02h
	bne	_$L443
CBLOCK 141 125 915
	l	r0,	NEAR _chari
	mov	r1,	#00h
	l	r2,	NEAR _chark
	mov	r3,	#00h
	sub	r0,	r2
	subc	r1,	r3
	l	r0,	NEAR _I2C_BUFF[er0]
	add	r0,	#0d0h
	mov	r1,	r0
	sll	r1,	#02h
	add	r1,	r0
	sll	r1,	#01h
	st	r1,	NEAR _I2CNumBytes_temp
CBLOCKEND 141 125 915

;;								else {I2CNumBytes_temp = (I2C_BUFF[chari-chark]-0x30);}
CLINEA 0000H 0001H 0394H 0009H 003FH
	bal	_$L445
_$L443 :
CBLOCK 141 126 916
	l	r0,	NEAR _chari
	mov	r1,	#00h
	l	r2,	NEAR _chark
	mov	r3,	#00h
	sub	r0,	r2
	subc	r1,	r3
	l	r0,	NEAR _I2C_BUFF[er0]
	add	r0,	#0d0h
	st	r0,	NEAR _I2CNumBytes_temp
CBLOCKEND 141 126 916
_$L445 :

;;								I2CNumBytes += I2CNumBytes_temp;
CLINEA 0000H 0001H 0395H 0009H 0028H
	l	r0,	NEAR _I2CNumBytes
	l	r1,	NEAR _I2CNumBytes_temp
	add	r0,	r1
	st	r0,	NEAR _I2CNumBytes
CBLOCKEND 141 123 918
CBLOCKEND 141 124 989

;;							for(chark = charj; chark>0; chark--){
CLINEA 0000H 0000H 0391H 0024H 002AH
	mov	r0,	r2
	add	r0,	#0ffh

;;							for(chark = charj; chark>0; chark--){
CLINEA 0000H 0000H 0391H 0001H 000BH
_$L518 :
	st	r0,	NEAR _chark

;;							for(chark = charj; chark>0; chark--){
CLINEA 0000H 0000H 0391H 001BH 0022H
	cmp	r0,	#00h
	ble	_$M139
	b	_$L436
_$M139 :

;;							chari++;
CLINEA 0000H 0000H 0397H 0008H 000FH
	lea	OFFSET _chari
	inc	[ea]

;;							charj = 0;
CLINEA 0000H 0001H 0398H 0008H 0011H
	mov	r0,	#00h

;;							while(I2C_BUFF[chari]!=0x20){
CLINEA 0000H 0000H 039AH 0001H 000BH
	bal	_$L519

;;							while(I2C_BUFF[chari]!=0x20){
CLINEA 0000H 0000H 039AH 0008H 0024H
_$L448 :
CBLOCK 141 127 922

;;								chari++;
CLINEA 0000H 0000H 039BH 0009H 0010H
	lea	OFFSET _chari
	inc	[ea]

;;								charj++;
CLINEA 0000H 0000H 039CH 0009H 0010H
	l	r0,	NEAR _charj
	add	r0,	#01h
CBLOCKEND 141 127 925

;;							while(I2C_BUFF[chari]!=0x20){
CLINEA 0000H 0000H 039AH 0001H 000BH
_$L519 :
	st	r0,	NEAR _charj

;;							while(I2C_BUFF[chari]!=0x20){
CLINEA 0000H 0000H 039AH 001BH 0022H
	l	r0,	NEAR _chari
	mov	r1,	#00h
	l	r0,	NEAR _I2C_BUFF[er0]
	cmp	r0,	#020h
	bne	_$L448

;;							for(chark = charj; chark>0; chark--){
CLINEA 0000H 0001H 039EH 000CH 0019H
	l	r0,	NEAR _charj

;;							for(chark = charj; chark>0; chark--){
CLINEA 0000H 0000H 039EH 0001H 000BH
	bal	_$L520

;;							for(chark = charj; chark>0; chark--){
CLINEA 0000H 0000H 039EH 0024H 002AH
_$L452 :
CBLOCK 141 128 926

;;								if(chark == 3){RegAddr_temp = (I2C_BUFF[chari-chark]-0x30)*100;}
CLINEA 0000H 0001H 039FH 0009H 0048H
	cmp	r0,	#03h
	bne	_$L456
CBLOCK 141 129 927
	l	r0,	NEAR _chari
	mov	r1,	#00h
	l	r2,	NEAR _chark
	mov	r3,	#00h
	sub	r0,	r2
	subc	r1,	r3
	l	r0,	NEAR _I2C_BUFF[er0]
	add	r0,	#0d0h
	mov	r1,	r0
	sll	r1,	#01h
	add	r1,	r0
	sll	r1,	#03h
	add	r1,	r0
	sll	r1,	#02h
	st	r1,	NEAR _RegAddr_temp

;;								else if(chark == 2){RegAddr_temp = (I2C_BUFF[chari-chark]-0x30)*10;}
CLINEA 0000H 0001H 03A0H 0009H 004CH
	bal	_$L461
_$L456 :
	cmp	r0,	#02h
	bne	_$L459
CBLOCK 141 130 928
	l	r0,	NEAR _chari
	mov	r1,	#00h
	l	r2,	NEAR _chark
	mov	r3,	#00h
	sub	r0,	r2
	subc	r1,	r3
	l	r0,	NEAR _I2C_BUFF[er0]
	add	r0,	#0d0h
	mov	r1,	r0
	sll	r1,	#02h
	add	r1,	r0
	sll	r1,	#01h
	st	r1,	NEAR _RegAddr_temp
CBLOCKEND 141 130 928

;;								else {RegAddr_temp = (I2C_BUFF[chari-chark]-0x30);}
CLINEA 0000H 0001H 03A1H 0009H 003BH
	bal	_$L461
_$L459 :
CBLOCK 141 131 929
	l	r0,	NEAR _chari
	mov	r1,	#00h
	l	r2,	NEAR _chark
	mov	r3,	#00h
	sub	r0,	r2
	subc	r1,	r3
	l	r0,	NEAR _I2C_BUFF[er0]
	add	r0,	#0d0h
	st	r0,	NEAR _RegAddr_temp
CBLOCKEND 141 131 929
_$L461 :

;;								RegAddr += RegAddr_temp;
CLINEA 0000H 0001H 03A2H 0009H 0020H
	l	r0,	NEAR _RegAddr
	l	r1,	NEAR _RegAddr_temp
	add	r0,	r1
	st	r0,	NEAR _RegAddr
CBLOCKEND 141 128 931
CBLOCKEND 141 129 989

;;							for(chark = charj; chark>0; chark--){
CLINEA 0000H 0000H 039EH 0024H 002AH
	mov	r0,	r2
	add	r0,	#0ffh

;;							for(chark = charj; chark>0; chark--){
CLINEA 0000H 0000H 039EH 0001H 000BH
_$L520 :
	st	r0,	NEAR _chark

;;							for(chark = charj; chark>0; chark--){
CLINEA 0000H 0000H 039EH 001BH 0022H
	cmp	r0,	#00h
	ble	_$M140
	b	_$L452
_$M140 :

;;							chari++;
CLINEA 0000H 0000H 03A4H 0008H 000FH
	lea	OFFSET _chari
	inc	[ea]

;;							charj = 0;
CLINEA 0000H 0001H 03A5H 0008H 0011H
	mov	r0,	#00h
	st	r0,	NEAR _charj

;;							_flgI2CFin = 0;																	//reset I2C completed Flag
CLINEA 0000H 0001H 03A8H 0008H 0041H
	st	r0,	NEAR __flgI2CFin

;;							i2c_stop();																		//Make sure I2C is not currently running
CLINEA 0000H 0001H 03A9H 0008H 004CH
	bl	_i2c_stop

;;							i2c_startReceive(I2CAdd, &RegAddr, 1, &I2CReceInfo, I2CNumBytes, (cbfI2c)_funcI2CFin);	//Begin I2C Recieve Command
CLINEA 0000H 0001H 03AAH 0008H 0079H
	mov	r0,	#BYTE1 OFFSET __funcI2CFin
	mov	r1,	#BYTE2 OFFSET __funcI2CFin
	push	er0
	l	r0,	NEAR _I2CNumBytes
	mov	r1,	#00h
	push	er0
	mov	r0,	#BYTE1 OFFSET _I2CReceInfo
	mov	r1,	#BYTE2 OFFSET _I2CReceInfo
	push	er0
	mov	er0,	#1 
	push	er0
	mov	r2,	#BYTE1 OFFSET _RegAddr
	mov	r3,	#BYTE2 OFFSET _RegAddr
	l	r0,	NEAR _I2CAdd
	bl	_i2c_startReceive
	add	sp,	#8 

;;							while(_flgI2CFin != 1){															//Wait for I2C commands to finish transfer
CLINEA 0000H 0000H 03ABH 0001H 000BH
	bal	_$L521

;;							while(_flgI2CFin != 1){															//Wait for I2C commands to finish transfer
CLINEA 0000H 0000H 03ABH 0008H 0057H
_$L464 :
CBLOCK 141 132 939

;;								NOP1000();
CLINEA 0000H 0001H 03ACH 0009H 0012H
	bl	_NOP1000

;;								main_clrWDT();
CLINEA 0000H 0001H 03ADH 0009H 0016H
	bl	_main_clrWDT
CBLOCKEND 141 132 942

;;							while(_flgI2CFin != 1){															//Wait for I2C commands to finish transfer
CLINEA 0000H 0000H 03ABH 0001H 000BH
_$L521 :

;;							while(_flgI2CFin != 1){															//Wait for I2C commands to finish transfer
CLINEA 0000H 0000H 03ABH 001BH 0022H
	l	r0,	NEAR __flgI2CFin
	cmp	r0,	#01h
	bne	_$L464

;;							I2C_RX_Data[6] = I2CReceInfo[0];
CLINEA 0000H 0001H 03B4H 0008H 0027H
	l	r0,	NEAR _I2CReceInfo
	st	r0,	NEAR _I2C_RX_Data+06h

;;							I2C_RX_Data[8] = I2CReceInfo[1];
CLINEA 0000H 0001H 03B5H 0008H 0027H
	l	r0,	NEAR _I2CReceInfo+01h
	st	r0,	NEAR _I2C_RX_Data+08h

;;							I2C_RX_Data[10] = I2CReceInfo[2];
CLINEA 0000H 0001H 03B6H 0008H 0028H
	l	r0,	NEAR _I2CReceInfo+02h
	st	r0,	NEAR _I2C_RX_Data+0ah

;;							I2C_RX_Data[12] = I2CReceInfo[3];
CLINEA 0000H 0001H 03B7H 0008H 0028H
	l	r0,	NEAR _I2CReceInfo+03h
	st	r0,	NEAR _I2C_RX_Data+0ch

;;							I2C_RX_Data[14] = I2CReceInfo[4];
CLINEA 0000H 0001H 03B8H 0008H 0028H
	l	r0,	NEAR _I2CReceInfo+04h
	st	r0,	NEAR _I2C_RX_Data+0eh

;;							I2C_RX_Data[16] = I2CReceInfo[5];
CLINEA 0000H 0001H 03B9H 0008H 0028H
	l	r0,	NEAR _I2CReceInfo+05h
	st	r0,	NEAR _I2C_RX_Data+010h

;;							I2C_RX_Data[18] = I2CReceInfo[6];
CLINEA 0000H 0001H 03BAH 0008H 0028H
	l	r0,	NEAR _I2CReceInfo+06h
	st	r0,	NEAR _I2C_RX_Data+012h

;;							I2C_RX_Data[20] = I2CReceInfo[7];
CLINEA 0000H 0001H 03BBH 0008H 0028H
	l	r0,	NEAR _I2CReceInfo+07h
	st	r0,	NEAR _I2C_RX_Data+014h

;;							_flgUartFin = 0;
CLINEA 0000H 0001H 03BDH 0008H 0017H
	mov	r0,	#00h
	st	r0,	NEAR __flgUartFin

;;							uart_stop();
CLINEA 0000H 0001H 03BEH 0008H 0013H
	bl	_uart_stop

;;							uart_startSend(I2C_RX_Data, 23, _funcUartFin);
CLINEA 0000H 0001H 03BFH 0008H 0035H
	mov	r0,	#BYTE1 OFFSET __funcUartFin
	mov	r1,	#BYTE2 OFFSET __funcUartFin
	push	er0
	mov	er2,	#23
	mov	r0,	#BYTE1 OFFSET _I2C_RX_Data
	mov	r1,	#BYTE2 OFFSET _I2C_RX_Data
	bl	_uart_startSend
	add	sp,	#2 

;;							while(_flgUartFin != 1){
CLINEA 0000H 0000H 03C0H 0001H 000BH
	bal	_$L522

;;							while(_flgUartFin != 1){
CLINEA 0000H 0000H 03C0H 0008H 001FH
_$L468 :
CBLOCK 141 133 960

;;								NOP1000();
CLINEA 0000H 0001H 03C1H 0009H 0012H
	bl	_NOP1000

;;								main_clrWDT();
CLINEA 0000H 0001H 03C2H 0009H 0016H
	bl	_main_clrWDT
CBLOCKEND 141 133 963

;;							while(_flgUartFin != 1){
CLINEA 0000H 0000H 03C0H 0001H 000BH
_$L522 :

;;							while(_flgUartFin != 1){
CLINEA 0000H 0000H 03C0H 001BH 0022H
	l	r0,	NEAR __flgUartFin
	cmp	r0,	#01h
	bne	_$L468

;;							I2CAdd = 0;
CLINEA 0000H 0001H 03C6H 0008H 0012H
	mov	r0,	#00h
	st	r0,	NEAR _I2CAdd

;;							I2CNumBytes = 0;
CLINEA 0000H 0001H 03C7H 0008H 0017H
	st	r0,	NEAR _I2CNumBytes

;;							RegAddr = 0;
CLINEA 0000H 0001H 03C8H 0008H 0013H
	st	r0,	NEAR _RegAddr

;;							chari = 0;
CLINEA 0000H 0001H 03C9H 0008H 0011H
	st	r0,	NEAR _chari

;;							for(chari = 0; chari < 8; chari++){
CLINEA 0000H 0000H 03CAH 0008H 002AH
_$L472 :
CBLOCK 141 134 970

;;								I2CReceInfo[chari] = 0;
CLINEA 0000H 0001H 03CBH 0009H 001FH
	mov	r1,	#00h
	mov	r2,	#00h
	st	r2,	NEAR _I2CReceInfo[er0]
CBLOCKEND 141 134 972

;;							for(chari = 0; chari < 8; chari++){
CLINEA 0000H 0000H 03CAH 0008H 002AH
	lea	OFFSET _chari
	inc	[ea]
	l	r0,	NEAR _chari

;;							for(chari = 0; chari < 8; chari++){
CLINEA 0000H 0000H 03CAH 001BH 0022H
	cmp	r0,	#08h
	blt	_$L472

;;							_flgUartFin = 0;
CLINEA 0000H 0001H 03CFH 0008H 0017H
	mov	r0,	#00h
	st	r0,	NEAR __flgUartFin

;;							uart_stop();
CLINEA 0000H 0001H 03D0H 0008H 0013H
	bl	_uart_stop

;;							uart_startSend(I2C_RX_REC, 21, _funcUartFin);
CLINEA 0000H 0001H 03D1H 0008H 0034H
	mov	r0,	#BYTE1 OFFSET __funcUartFin
	mov	r1,	#BYTE2 OFFSET __funcUartFin
	push	er0
	mov	er2,	#21
	mov	r0,	#BYTE1 OFFSET _I2C_RX_REC
	mov	r1,	#BYTE2 OFFSET _I2C_RX_REC
	bl	_uart_startSend
	add	sp,	#2 

;;							while(_flgUartFin != 1){
CLINEA 0000H 0000H 03D2H 0001H 000BH
	bal	_$L523

;;							while(_flgUartFin != 1){
CLINEA 0000H 0000H 03D2H 0008H 001FH
_$L478 :
CBLOCK 141 135 978

;;								NOP1000();
CLINEA 0000H 0001H 03D3H 0009H 0012H
	bl	_NOP1000

;;								main_clrWDT();
CLINEA 0000H 0001H 03D4H 0009H 0016H
	bl	_main_clrWDT
CBLOCKEND 141 135 981

;;							while(_flgUartFin != 1){
CLINEA 0000H 0000H 03D2H 0001H 000BH
_$L523 :

;;							while(_flgUartFin != 1){
CLINEA 0000H 0000H 03D2H 001BH 0022H
	l	r0,	NEAR __flgUartFin
	cmp	r0,	#01h
	bne	_$L478

;;							}
CLINEA 0000H 0000H 03D5H 0008H 0008H
CBLOCKEND 141 115 982
CBLOCKEND 141 114 983
CBLOCKEND 141 113 984
CBLOCKEND 141 112 985
CBLOCKEND 141 111 986

;;		goto RX_Loop;
CLINEA 0000H 0001H 03DBH 0003H 000FH
	b	_$L12
CBLOCKEND 141 2 989

;;}//end main
CLINEA 0000H 0001H 03DDH 0001H 000BH
CBLOCKEND 141 1 989
CFUNCTIONEND 141


	rseg $$main_clrWDT$main
CFUNCTION 124

_main_clrWDT	:
CBLOCK 124 1 1015

;;{
CLINEA 0000H 0001H 03F7H 0001H 0001H
CBLOCK 124 2 1015

;;	do {
CLINEA 0000H 0001H 03FAH 0002H 0005H
_$L527 :
CBLOCK 124 3 1018

;;		WDTCON = 0x5Au;
CLINEA 0000H 0001H 03FBH 0003H 0011H
	mov	r0,	#05ah
	st	r0,	0f00eh
CBLOCKEND 124 3 1020

;;	} while (WDP != 1);
CLINEA 0000H 0000H 03FCH 0002H 0014H
	tb	0f00eh.0
	beq	_$L527

;;	WDTCON = 0xA5u;
CLINEA 0000H 0001H 03FDH 0002H 0010H
	mov	r0,	#0a5h
	st	r0,	0f00eh
CBLOCKEND 124 2 1022

;;}
CLINEA 0000H 0001H 03FEH 0001H 0001H
	rt
CBLOCKEND 124 1 1022
CFUNCTIONEND 124


	rseg $$NOP1000$main
CFUNCTION 140

_NOP1000	:
CBLOCK 140 1 1032

;;{
CLINEA 0000H 0001H 0408H 0001H 0001H
CBLOCK 140 2 1032
CLOCAL 4AH 0002H 0000H 0002H "ONCNT" 02H 00H 01H
CBLOCKEND 140 2 1039

;;}
CLINEA 0000H 0001H 040FH 0001H 0001H
	rt
CBLOCKEND 140 1 1039
CFUNCTIONEND 140


	rseg $$Initialization$main
CFUNCTION 125

_Initialization	:
CBLOCK 125 1 1046

;;static void Initialization(void){
CLINEA 0000H 0001H 0416H 0001H 0021H
	push	lr
CBLOCK 125 2 1046
CRET 0000H

;;	DSIO0 = 1; // 0=> Enables Synchronous Serial Port 0 (initial value).
CLINEA 0000H 0001H 041AH 0002H 0045H
	sb	0f02ah.0

;;	DUA0  = 0; // 0=> Enables the operation of UART0 (initial value).
CLINEA 0000H 0001H 041BH 0002H 0042H
	rb	0f02ah.2

;;	DUA1  = 1; // 0=> Enables Uart1 (initial value). 
CLINEA 0000H 0001H 041CH 0002H 0032H
	sb	0f02ah.3

;;	DI2C1 = 1; // 0=> Enables I2C bus Interface (Slave) (initial value).
CLINEA 0000H 0001H 041DH 0002H 0045H
	sb	0f02ah.6

;;	DI2C0 = 0; // 0=> Enables I2C bus Interface (Master) (initial value).	
CLINEA 0000H 0001H 041EH 0002H 0047H
	rb	0f02ah.7

;;	BLKCON4 = 0x00; // 0=> Enables SA-ADC
CLINEA 0000H 0001H 0420H 0002H 0026H
	mov	r0,	#00h
	st	r0,	0f02ch

;;	BLKCON6 = 0x00; // (1=disables; 0=enables) the operation of Timers 8, 9, A, E, F.
CLINEA 0000H 0001H 0421H 0002H 0052H
	st	r0,	0f02eh

;;	BLKCON7 = 0x00; // (1=disables; 0=enables) the operation of PWW (PWMC, PWMD, PWME, PWMF
CLINEA 0000H 0001H 0422H 0002H 0058H
	st	r0,	0f02fh

;;	PortA_Low();	//Initialize all 3 Ports of Port A to GPIO-Low
CLINEA 0000H 0001H 0425H 0002H 003CH
	bl	_PortA_Low

;;	PortB_Low();	//Initialize all 8 Ports of Port B to GPIO-Low
CLINEA 0000H 0001H 0426H 0002H 003CH
	bl	_PortB_Low

;;	PortC_Low();	//Initialize all 8 Ports of Port C to GPIO-Low
CLINEA 0000H 0001H 0427H 0002H 003CH
	bl	_PortC_Low

;;	PortD_Low();	//Initialize all 6 Ports of Port D to GPIO-Low
CLINEA 0000H 0001H 0428H 0002H 003CH
	bl	_PortD_Low

;;    SetOSC();
CLINEA 0000H 0001H 042BH 0005H 000DH
	bl	_SetOSC

;;	TM8D    = 0;	//Timer 8 DATA Register
CLINEA 0000H 0001H 0432H 0002H 0025H
	mov	r0,	#00h
	st	r0,	0f8e0h

;;	TM8C    = 0;	//Timer 8 CLOCK Register
CLINEA 0000H 0001H 0434H 0002H 0026H
	st	r0,	0f8e1h

;;	T8C1 = 0;	// 01 = HTBCLK  
CLINEA 0000H 0001H 0438H 0002H 001BH
	rb	0f8e1h.1

;;	T8C0 = 1;
CLINEA 0000H 0001H 0439H 0002H 000AH
	sb	0f8e1h.0

;;	T89M16 = 0;	// 0=8-Bit Mode; 1=16bit Mode...
CLINEA 0000H 0001H 043BH 0002H 002DH
	rb	0f8e2h.5

;;	T8OST = 0;	// 0=Normal; 1=One-Shot...
CLINEA 0000H 0001H 043DH 0002H 0026H
	rb	0f8e2h.7

;;	T8RUN = 0;	//0=STOP; 1=START...
CLINEA 0000H 0001H 0440H 0002H 0020H
	rb	0f8e3h.0

;;	irq_di();	// Disable Interrupts
CLINEA 0000H 0001H 0447H 0002H 0020H
	bl	_irq_di

;;	irq_init();	// Initialize Interrupts (All Off and NO Requests)
CLINEA 0000H 0001H 0448H 0002H 003FH
	bl	_irq_init

;;	IE0 = IE1 = IE2 = IE3 = IE4 = IE5 = IE6 = IE7 = 0;
CLINEA 0000H 0001H 0453H 0002H 0033H
	mov	r0,	#00h
	st	r0,	0f017h
	st	r0,	0f016h
	st	r0,	0f015h
	st	r0,	0f014h
	st	r0,	0f013h
	st	r0,	0f012h
	st	r0,	0f011h
	st	r0,	0f010h

;;	IRQ0 = IRQ1 = IRQ2 = IRQ3 = IRQ4 = IRQ5 = IRQ6 = IRQ7 = 0;
CLINEA 0000H 0001H 045EH 0002H 003BH
	st	r0,	0f01fh
	st	r0,	0f01eh
	st	r0,	0f01dh
	st	r0,	0f01ch
	st	r0,	0f01bh
	st	r0,	0f01ah
	st	r0,	0f019h
	st	r0,	0f018h

;;	E2H = 0; 	// E2H is the Enable flag for 2Hz TBC Interrupt (1=ENABLED)
CLINEA 0000H 0001H 045FH 0002H 0046H
	rb	0f017h.3

;;	(void)irq_setHdr( (unsigned char)IRQ_NO_UA0INT, _intUart );
CLINEA 0000H 0001H 0461H 0002H 003CH
	mov	r2,	#BYTE1 OFFSET __intUart
	mov	r3,	#BYTE2 OFFSET __intUart
	mov	r0,	#0fh
	bl	_irq_setHdr

;;	(void)irq_setHdr( (unsigned char)IRQ_NO_I2CMINT, _intI2c );
CLINEA 0000H 0001H 0462H 0002H 003CH
	mov	r2,	#BYTE1 OFFSET __intI2c
	mov	r3,	#BYTE2 OFFSET __intI2c
	mov	r0,	#0ch
	bl	_irq_setHdr

;;	EI2CM = 1;
CLINEA 0000H 0001H 0464H 0002H 000BH
	sb	0f012h.7

;;	QI2CM = 1;
CLINEA 0000H 0001H 0465H 0002H 000BH
	sb	0f01ah.7

;;	EUA0 = 1; // EUA0 is the enable flag for the UART0 interrupt (1=ENABLED)
CLINEA 0000H 0001H 0466H 0002H 0049H
	sb	0f014h.0

;;	irq_ei(); // Enable Interrupts
CLINEA 0000H 0001H 0468H 0002H 001FH
	bl	_irq_ei

;;	WDTMOD = 0x03; 	// 0x03=overflow 8sec...
CLINEA 0000H 0001H 046CH 0002H 0029H
	mov	r0,	#03h
	st	r0,	0f00fh

;;	main_clrWDT(); 	// Clear WDT
CLINEA 0000H 0001H 046DH 0002H 001DH
	bl	_main_clrWDT

;;	HelloWorld[12] 	= 0x0D;
CLINEA 0000H 0001H 0470H 0002H 0018H
	mov	r0,	#0dh
	st	r0,	NEAR _HelloWorld+0ch

;;	HelloWorld[13] 	= 0x0A;
CLINEA 0000H 0001H 0471H 0002H 0018H
	mov	r0,	#0ah
	st	r0,	NEAR _HelloWorld+0dh

;;	InputStatus[21] 	= 0x0D;
CLINEA 0000H 0001H 0472H 0002H 0019H
	mov	r0,	#0dh
	st	r0,	NEAR _InputStatus+015h

;;	InputStatus[22] 	= 0x0A;
CLINEA 0000H 0001H 0473H 0002H 0019H
	mov	r0,	#0ah
	st	r0,	NEAR _InputStatus+016h

;;	InputRec[12] 	= 0x0D;
CLINEA 0000H 0001H 0474H 0002H 0016H
	mov	r0,	#0dh
	st	r0,	NEAR _InputRec+0ch

;;	InputRec[13] 	= 0x0A;
CLINEA 0000H 0001H 0475H 0002H 0016H
	mov	r0,	#0ah
	st	r0,	NEAR _InputRec+0dh

;;	OutputRec[21] 	= 0x0D;
CLINEA 0000H 0001H 0476H 0002H 0017H
	mov	r0,	#0dh
	st	r0,	NEAR _OutputRec+015h

;;	OutputRec[22] 	= 0x0A;
CLINEA 0000H 0001H 0477H 0002H 0017H
	mov	r0,	#0ah
	st	r0,	NEAR _OutputRec+016h

;;	AckMCUConn[20] 	= 0x0D;
CLINEA 0000H 0001H 0478H 0002H 0018H
	mov	r0,	#0dh
	st	r0,	NEAR _AckMCUConn+014h

;;	AckMCUConn[21] 	= 0x0A;
CLINEA 0000H 0001H 0479H 0002H 0018H
	mov	r0,	#0ah
	st	r0,	NEAR _AckMCUConn+015h

;;	NackMCUConn[60] = 0x0D;
CLINEA 0000H 0001H 047AH 0002H 0018H
	mov	r0,	#0dh
	st	r0,	NEAR _NackMCUConn+03ch

;;	NackMCUConn[61] = 0x0A;
CLINEA 0000H 0001H 047BH 0002H 0018H
	mov	r0,	#0ah
	st	r0,	NEAR _NackMCUConn+03dh

;;	ListFWRev[20] = 0x0D;
CLINEA 0000H 0001H 047CH 0002H 0016H
	mov	r0,	#0dh
	st	r0,	NEAR _ListFWRev+014h

;;	ListFWRev[21] = 0x0A;
CLINEA 0000H 0001H 047DH 0002H 0016H
	mov	r0,	#0ah
	st	r0,	NEAR _ListFWRev+015h

;;	I2C_TX_REC[19] = 0x0D;
CLINEA 0000H 0001H 047EH 0002H 0017H
	mov	r0,	#0dh
	st	r0,	NEAR _I2C_TX_REC+013h

;;	I2C_TX_REC[20] = 0x0A;
CLINEA 0000H 0001H 047FH 0002H 0017H
	mov	r0,	#0ah
	st	r0,	NEAR _I2C_TX_REC+014h

;;	I2C_RX_REC[19] = 0x0D;
CLINEA 0000H 0001H 0480H 0002H 0017H
	mov	r0,	#0dh
	st	r0,	NEAR _I2C_RX_REC+013h

;;	I2C_RX_REC[20] = 0x0A;
CLINEA 0000H 0001H 0481H 0002H 0017H
	mov	r0,	#0ah
	st	r0,	NEAR _I2C_RX_REC+014h

;;	I2C_RX_Data[21] = 0x0D;
CLINEA 0000H 0001H 0482H 0002H 0018H
	mov	r0,	#0dh
	st	r0,	NEAR _I2C_RX_Data+015h

;;	I2C_RX_Data[22] = 0x0A;
CLINEA 0000H 0001H 0483H 0002H 0018H
	mov	r0,	#0ah
	st	r0,	NEAR _I2C_RX_Data+016h

;;	(void)i2c_init(I2C_MOD_FST, (unsigned short)HSCLK_KHZ, I2C_SYN_OFF);
CLINEA 0000H 0001H 0489H 0002H 0045H
	mov	r0,	#00h
	push	r0
	mov	r2,	#040h
	mov	r3,	#01fh
	mov	r0,	#01h
	bl	_i2c_init
	add	sp,	#2 

;;			     &_uartSetParam );				/* Param... 	 */
CLINEA 0000H 0001H 048EH 0009H 002DH
	mov	r0,	#BYTE1 OFFSET __uartSetParam
	mov	r1,	#BYTE2 OFFSET __uartSetParam
	push	er0
	mov	r2,	#040h
	mov	r3,	#01fh
	mov	r0,	#02h
	bl	_uart_init
	add	sp,	#2 

;;	uart_PortSet();
CLINEA 0000H 0001H 048FH 0002H 0010H
	bl	_uart_PortSet

;;	_flgUartFin = 0;
CLINEA 0000H 0001H 0490H 0002H 0011H
	mov	r0,	#00h
	st	r0,	NEAR __flgUartFin

;;	uart_stop();
CLINEA 0000H 0001H 0491H 0002H 000DH
	bl	_uart_stop

;;	uart_startSend(HelloWorld, 14, _funcUartFin); // Send, "Hello World!"
CLINEA 0000H 0001H 0493H 0002H 0046H
	mov	r0,	#BYTE1 OFFSET __funcUartFin
	mov	r1,	#BYTE2 OFFSET __funcUartFin
	push	er0
	mov	er2,	#14
	mov	r0,	#BYTE1 OFFSET _HelloWorld
	mov	r1,	#BYTE2 OFFSET _HelloWorld
	bl	_uart_startSend
	add	sp,	#2 

;;	while(_flgUartFin != 1){
CLINEA 0000H 0000H 0494H 0001H 0015H
	bal	_$L540

;;	while(_flgUartFin != 1){
CLINEA 0000H 0000H 0494H 0002H 0019H
_$L538 :
CBLOCK 125 3 1172

;;		NOP1000();
CLINEA 0000H 0001H 0495H 0003H 000CH
	bl	_NOP1000

;;		main_clrWDT();
CLINEA 0000H 0001H 0496H 0003H 0010H
	bl	_main_clrWDT
CBLOCKEND 125 3 1175

;;	while(_flgUartFin != 1){
CLINEA 0000H 0000H 0494H 0001H 0015H
_$L540 :

;;	while(_flgUartFin != 1){
CLINEA 0000H 0000H 0494H 001BH 0022H
	l	r0,	NEAR __flgUartFin
	cmp	r0,	#01h
	bne	_$L538
CBLOCKEND 125 2 1176

;;}//End Initialization
CLINEA 0000H 0001H 0498H 0001H 0015H
	pop	pc
CBLOCKEND 125 1 1176
CFUNCTIONEND 125


	rseg $$_funcUartFin$main
CFUNCTION 134

__funcUartFin	:
CBLOCK 134 1 1188

;;{
CLINEA 0000H 0001H 04A4H 0001H 0001H
	push	lr
CBLOCK 134 2 1188
CRET 0000H
CARGUMENT 46H 0002H 0000H "size" 02H 00H 01H
CARGUMENT 46H 0001H 0000H "errStat" 02H 00H 00H

;;	uart_continue();					// Function in UART.c: process to continue send and receive...
CLINEA 0000H 0001H 04A5H 0002H 0054H
	bl	_uart_continue

;;	_flgUartFin = (unsigned char)FLG_SET;
CLINEA 0000H 0001H 04A6H 0002H 0026H
	mov	r0,	#01h
	st	r0,	NEAR __flgUartFin

;;	main_reqNotHalt();				// uncommented 5/2/2013
CLINEA 0000H 0001H 04A7H 0002H 002EH
	bl	_main_reqNotHalt
CBLOCKEND 134 2 1192

;;}
CLINEA 0000H 0001H 04A8H 0001H 0001H
	pop	pc
CBLOCKEND 134 1 1192
CFUNCTIONEND 134


	rseg $$_funcI2CFin$main
CFUNCTION 135

__funcI2CFin	:
CBLOCK 135 1 1203

;;{
CLINEA 0000H 0001H 04B3H 0001H 0001H
	push	lr
CBLOCK 135 2 1203
CRET 0000H
CARGUMENT 46H 0002H 0000H "size" 02H 00H 01H
CARGUMENT 46H 0001H 0000H "errStat" 02H 00H 00H

;;	i2c_continue();					// Function in UART.c: process to continue send and receive...
CLINEA 0000H 0001H 04B4H 0002H 0053H
	bl	_i2c_continue

;;	_flgI2CFin = (unsigned char)FLG_SET;
CLINEA 0000H 0001H 04B5H 0002H 0025H
	mov	r0,	#01h
	st	r0,	NEAR __flgI2CFin

;;	main_reqNotHalt();				// uncommented 5/2/2013
CLINEA 0000H 0001H 04B6H 0002H 002EH
	bl	_main_reqNotHalt
CBLOCKEND 135 2 1207

;;}
CLINEA 0000H 0001H 04B7H 0001H 0001H
	pop	pc
CBLOCKEND 135 1 1207
CFUNCTIONEND 135


	rseg $$_intI2c$main
CFUNCTION 139

__intI2c	:
CBLOCK 139 1 1217

;;{
CLINEA 0000H 0001H 04C1H 0001H 0001H
	push	lr
CBLOCK 139 2 1217
CRET 0000H

;;	(void)i2c_continue();
CLINEA 0000H 0001H 04C2H 0002H 0016H
	bl	_i2c_continue

;;	main_reqNotHalt();
CLINEA 0000H 0001H 04C3H 0002H 0013H
	bl	_main_reqNotHalt
CBLOCKEND 139 2 1220

;;}
CLINEA 0000H 0001H 04C4H 0001H 0001H
	pop	pc
CBLOCKEND 139 1 1220
CFUNCTIONEND 139


	rseg $$checkI2C$main
CFUNCTION 136

_checkI2C	:
CBLOCK 136 1 1230

;;{
CLINEA 0000H 0001H 04CEH 0001H 0001H
	push	lr
CBLOCK 136 2 1230
CRET 0000H
CLOCAL 47H 0002H 0024H 0002H "ret" 02H 00H 01H

;;	while (ret != 1) {
CLINEA 0000H 0000H 04D3H 0002H 0013H
_$L547 :
CBLOCK 136 3 1235

;;		ret = i2c_continue();
CLINEA 0000H 0000H 04D4H 0003H 0017H
	bl	_i2c_continue
CBLOCK 136 4 1237
CBLOCKEND 136 4 1239
CBLOCKEND 136 3 1240

;;	while (ret != 1) {
CLINEA 0000H 0000H 04D3H 001BH 0022H
	cmp	r0,	#01h
	cmpc	r1,	#00h
	bne	_$L547
CBLOCKEND 136 2 1241

;;}
CLINEA 0000H 0001H 04D9H 0001H 0001H
	pop	pc
CBLOCKEND 136 1 1241
CFUNCTIONEND 136


	rseg $$main_reqNotHalt$main
CFUNCTION 137

_main_reqNotHalt	:
CBLOCK 137 1 1251

;;{
CLINEA 0000H 0001H 04E3H 0001H 0001H
CBLOCK 137 2 1251

;;	_reqNotHalt = (unsigned char)FLG_SET;
CLINEA 0000H 0001H 04E4H 0002H 0026H
	mov	r0,	#01h
	st	r0,	NEAR __reqNotHalt
CBLOCKEND 137 2 1253

;;}
CLINEA 0000H 0001H 04E5H 0001H 0001H
	rt
CBLOCKEND 137 1 1253
CFUNCTIONEND 137


	rseg $$_intUart$main
CFUNCTION 138

__intUart	:
CBLOCK 138 1 1263

;;{
CLINEA 0000H 0001H 04EFH 0001H 0001H
CBLOCK 138 2 1263

;;		uart_continue(); //in UART.c: process to continue send and receive...
CLINEA 0000H 0001H 04F0H 0003H 0047H
	b	_uart_continue
CBLOCKEND 138 2 1265
CLINEA 0000H 0001H 04F1H 0001H 0001H
CBLOCKEND 138 1 1265
CFUNCTIONEND 138


	rseg $$SetOSC$main
CFUNCTION 126

_SetOSC	:
CBLOCK 126 1 1270

;;static void SetOSC(void){
CLINEA 0000H 0001H 04F6H 0001H 0019H
CBLOCK 126 2 1270

;;	SYSC0 = 0;			// Used to select the frequency of the HSCLK => 00=8.192MHz.
CLINEA 0000H 0001H 04F9H 0002H 004AH
	rb	0f002h.0

;;	SYSC1 = 0;
CLINEA 0000H 0001H 04FAH 0002H 000BH
	rb	0f002h.1

;;	OSCM1 = 1;			// 10 => Built-in PLL oscillation mode
CLINEA 0000H 0001H 04FCH 0002H 0034H
	sb	0f002h.3

;;	OSCM0 = 0;
CLINEA 0000H 0001H 04FDH 0002H 000BH
	rb	0f002h.2

;;	ENOSC = 1;			//1=Enable High Speed Oscillator...
CLINEA 0000H 0001H 04FFH 0002H 0031H
	sb	0f003h.1

;;	SYSCLK = 1;			//1=HSCLK; 0=LSCLK 
CLINEA 0000H 0001H 0500H 0002H 0022H
	sb	0f003h.0

;;	LPLL = 1;			//1=Enables the use of PLL oscillation - ADDED 4/30/2013
CLINEA 0000H 0001H 0502H 0002H 0045H
	sb	0f003h.7

;;	__EI();			//INT enable
CLINEA 0000H 0001H 0504H 0002H 0017H
	ei
CBLOCKEND 126 2 1285

;;}
CLINEA 0000H 0001H 0505H 0001H 0001H
	rt
CBLOCKEND 126 1 1285
CFUNCTIONEND 126


	rseg $$analog_comparator$main
CFUNCTION 127

_analog_comparator	:
CBLOCK 127 1 1292

;;void analog_comparator(void){
CLINEA 0000H 0001H 050CH 0001H 001DH
CBLOCK 127 2 1292

;;	CMP0EN  = 0x01; 	// Comparator ON...
CLINEA 0000H 0001H 0522H 0002H 0025H
	sb	0f950h.0

;;	CMP0E1  = 0x00; 	// No Interupt...
CLINEA 0000H 0001H 0523H 0002H 0023H
	rb	0f951h.1

;;	CMP0E0  = 0x00;
CLINEA 0000H 0001H 0524H 0002H 0010H
	rb	0f951h.0

;;	CMP0SM1 = 0x00; 	// Detect without Sampling... 
CLINEA 0000H 0001H 0525H 0002H 0030H
	rb	0f951h.3

;;	CMP0RFS = 0x01; 	// Differential Input on B5
CLINEA 0000H 0001H 0526H 0002H 002DH
	sb	0f951h.4

;;	CMP0EN  = 0x00;
CLINEA 0000H 0001H 0529H 0002H 0010H
	rb	0f950h.0
CBLOCKEND 127 2 1324

;;}
CLINEA 0000H 0001H 052CH 0001H 0001H
	rt
CBLOCKEND 127 1 1324
CFUNCTIONEND 127


	rseg $$PortA_Low$main
CFUNCTION 128

_PortA_Low	:
CBLOCK 128 1 1332

;;void PortA_Low(void){
CLINEA 0000H 0001H 0534H 0001H 0015H
CBLOCK 128 2 1332

;;	PA0DIR = 0;		// PortA Bit0 set to Output Mode...
CLINEA 0000H 0001H 053EH 0002H 0031H
	rb	0f251h.0

;;	PA1DIR = 0;		// PortA Bit1 set to Output Mode...
CLINEA 0000H 0001H 053FH 0002H 0031H
	rb	0f251h.1

;;	PA2DIR = 0;		// PortA Bit2 set to Output Mode...
CLINEA 0000H 0001H 0540H 0002H 0031H
	rb	0f251h.2

;;	PA0C1  = 1;		// PortA Bit0 set to CMOS Output...
CLINEA 0000H 0001H 0543H 0002H 0031H
	sb	0f253h.0

;;	PA0C0  = 1;		
CLINEA 0000H 0001H 0544H 0002H 000EH
	sb	0f252h.0

;;	PA1C1  = 1;		// PortA Bit1 set to CMOS Output...
CLINEA 0000H 0001H 0545H 0002H 0031H
	sb	0f253h.1

;;	PA1C0  = 1;	
CLINEA 0000H 0001H 0546H 0002H 000DH
	sb	0f252h.1

;;	PA2C1  = 1;		// PortA Bit2 set to CMOS Output...
CLINEA 0000H 0001H 0547H 0002H 0031H
	sb	0f253h.2

;;	PA2C0  = 1;	
CLINEA 0000H 0001H 0548H 0002H 000DH
	sb	0f252h.2

;;	PA0MD1  = 0;	// PortA Bit0 set to General Purpose Output...
CLINEA 0000H 0001H 054BH 0002H 003CH
	rb	0f255h.0

;;	PA0MD0  = 0;	
CLINEA 0000H 0001H 054CH 0002H 000EH
	rb	0f254h.0

;;	PA1MD1  = 0;	// PortA Bit1 set to General Purpose Output...
CLINEA 0000H 0001H 054DH 0002H 003CH
	rb	0f255h.1

;;	PA1MD0  = 0;	
CLINEA 0000H 0001H 054EH 0002H 000EH
	rb	0f254h.1

;;	PA2MD1  = 0;	// PortA Bit2 set to General Purpose Output...
CLINEA 0000H 0001H 054FH 0002H 003CH
	rb	0f255h.2

;;	PA2MD0  = 0;	
CLINEA 0000H 0001H 0550H 0002H 000EH
	rb	0f254h.2

;;	PA0D = 0;		// A.0 Output OFF....
CLINEA 0000H 0001H 0553H 0002H 0021H
	rb	0f250h.0

;;	PA1D = 0;		// A.1 Output OFF....
CLINEA 0000H 0001H 0554H 0002H 0021H
	rb	0f250h.1

;;	PA2D = 0;		// A.2 Output OFF....
CLINEA 0000H 0001H 0555H 0002H 0021H
	rb	0f250h.2

;;	main_clrWDT(); 	// Clear WDT
CLINEA 0000H 0001H 0557H 0002H 001DH
	b	_main_clrWDT
CBLOCKEND 128 2 1369
CLINEA 0000H 0001H 0559H 0001H 0001H
CBLOCKEND 128 1 1369
CFUNCTIONEND 128


	rseg $$PortB_Low$main
CFUNCTION 129

_PortB_Low	:
CBLOCK 129 1 1375

;;void PortB_Low(void){
CLINEA 0000H 0001H 055FH 0001H 0015H
CBLOCK 129 2 1375

;;	PB0DIR = 0;		// PortB Bit0 set to Output Mode...
CLINEA 0000H 0001H 0569H 0002H 0031H
	rb	0f259h.0

;;	PB1DIR = 0;		// PortB Bit1 set to Output Mode...
CLINEA 0000H 0001H 056AH 0002H 0031H
	rb	0f259h.1

;;	PB2DIR = 0;		// PortB Bit2 set to Output Mode...
CLINEA 0000H 0001H 056BH 0002H 0031H
	rb	0f259h.2

;;	PB3DIR = 0;		// PortB Bit3 set to Output Mode...
CLINEA 0000H 0001H 056CH 0002H 0031H
	rb	0f259h.3

;;	PB4DIR = 0;		// PortB Bit4 set to Output Mode...
CLINEA 0000H 0001H 056DH 0002H 0031H
	rb	0f259h.4

;;	PB5DIR = 0;		// PortB Bit5 set to Output Mode...
CLINEA 0000H 0001H 056EH 0002H 0031H
	rb	0f259h.5

;;	PB6DIR = 0;		// PortB Bit6 set to Output Mode...
CLINEA 0000H 0001H 056FH 0002H 0031H
	rb	0f259h.6

;;	PB7DIR = 0;		// PortB Bit7 set to Output Mode...
CLINEA 0000H 0001H 0570H 0002H 0031H
	rb	0f259h.7

;;	PB0C1  = 1;		// PortB Bit0 set to CMOS Output...
CLINEA 0000H 0001H 0573H 0002H 0031H
	sb	0f25bh.0

;;	PB0C0  = 1;		
CLINEA 0000H 0001H 0574H 0002H 000EH
	sb	0f25ah.0

;;	PB1C1  = 1;		// PortB Bit1 set to CMOS Output...
CLINEA 0000H 0001H 0575H 0002H 0031H
	sb	0f25bh.1

;;	PB1C0  = 1;	
CLINEA 0000H 0001H 0576H 0002H 000DH
	sb	0f25ah.1

;;	PB2C1  = 1;		// PortB Bit2 set to CMOS Output...
CLINEA 0000H 0001H 0577H 0002H 0031H
	sb	0f25bh.2

;;	PB2C0  = 1;	
CLINEA 0000H 0001H 0578H 0002H 000DH
	sb	0f25ah.2

;;	PB3C1  = 1;		// PortB Bit3 set to CMOS Output...
CLINEA 0000H 0001H 0579H 0002H 0031H
	sb	0f25bh.3

;;	PB3C0  = 1;		
CLINEA 0000H 0001H 057AH 0002H 000EH
	sb	0f25ah.3

;;	PB4C1  = 1;		// PortB Bit4 set to CMOS Output...
CLINEA 0000H 0001H 057BH 0002H 0031H
	sb	0f25bh.4

;;	PB4C0  = 1;	
CLINEA 0000H 0001H 057CH 0002H 000DH
	sb	0f25ah.4

;;	PB5C1  = 1;		// PortB Bit5 set to CMOS Output...
CLINEA 0000H 0001H 057DH 0002H 0031H
	sb	0f25bh.5

;;	PB5C0  = 1;	
CLINEA 0000H 0001H 057EH 0002H 000DH
	sb	0f25ah.5

;;	PB6C1  = 1;		// PortB Bit6 set to CMOS Output...
CLINEA 0000H 0001H 057FH 0002H 0031H
	sb	0f25bh.6

;;	PB6C0  = 1;	
CLINEA 0000H 0001H 0580H 0002H 000DH
	sb	0f25ah.6

;;	PB7C1  = 1;		// PortB Bit7 set to CMOS Output...
CLINEA 0000H 0001H 0581H 0002H 0031H
	sb	0f25bh.7

;;	PB7C0  = 1;	
CLINEA 0000H 0001H 0582H 0002H 000DH
	sb	0f25ah.7
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
