ROHMUSDC/LapisDevBoard/SAMPLE CODE/Q178 - LED_LIGHTING/main/ML610178A.H

/**************************************************************

    ML610178A.H - SFR define Header file for CCU8

    #CORE           "nX-U8/100"
    #TARGET         "ML610178A"
    #VERSION        "2.01"
    Last Edition  Mar 18, 2013
    Copyright (C) 2011 LAPIS SEMICONDUCTOR CO., LTD.
**************************************************************/
#ifndef _ML610178A_H_
#define _ML610178A_H_

typedef struct{
  unsigned char b0  : 1 ;
  unsigned char b1  : 1 ;
  unsigned char b2  : 1 ;
  unsigned char b3  : 1 ;
  unsigned char b4  : 1 ;
  unsigned char b5  : 1 ;
  unsigned char b6  : 1 ;
  unsigned char b7  : 1 ;
} _BYTE_FIELD;

/*---------------------------------------------------
	CODE ADDRESS SYMBOLS
---------------------------------------------------*/
#define WDTINT	0x0008
#define NMINT	0x000A
#define LOSCINT	0x000C
#define P00INT	0x0010
#define P01INT	0x0012
#define P02INT	0x0014
#define P03INT	0x0016
#define SIO0INT	0x0020
#define SIO1INT	0x0022
#define SADINT	0x0024
#define I2C0INT	0x002E
#define TM0INT	0x0030
#define TM1INT	0x0032
#define TM8INT	0x0034
#define TM9INT	0x0036
#define UA0INT	0x0040
#define UA1INT	0x0042
#define TMAINT	0x005C
#define TMBINT	0x005E
#define PW4INT	0x0060
#define PW5INT	0x0062
#define T128HINT	0x006A
#define T32HINT	0x006E
#define T16HINT	0x0070
#define T2HINT	0x0076
/*---------------------------------------------------
	END OF CODE ADDRESS SYMBOLS
---------------------------------------------------*/

/*---------------------------------------------------
	DATA ADDRESS SYMBOLS
---------------------------------------------------*/
#define DSR (*(volatile unsigned char __near *)0xF000)
#define _B_DSR (*(volatile _BYTE_FIELD __near *)0xF000)

#define RSTAT (*(volatile unsigned char __near *)0xF001)
#define _B_RSTAT (*(volatile _BYTE_FIELD __near *)0xF001)

#define FCON (*(volatile unsigned int __near *)0xF002)

#define FCON0 (*(volatile unsigned char __near *)0xF002)
#define _B_FCON0 (*(volatile _BYTE_FIELD __near *)0xF002)

#define FCON1 (*(volatile unsigned char __near *)0xF003)
#define _B_FCON1 (*(volatile _BYTE_FIELD __near *)0xF003)

#define STPACP (*(volatile unsigned char __near *)0xF008)

#define SBYCON (*(volatile unsigned char __near *)0xF009)
#define _B_SBYCON (*(volatile _BYTE_FIELD __near *)0xF009)

#define LTBR (*(volatile unsigned char __near *)0xF00A)
#define _B_LTBR (*(volatile _BYTE_FIELD __near *)0xF00A)

#define HTBDR (*(volatile unsigned char __near *)0xF00B)
#define _B_HTBDR (*(volatile _BYTE_FIELD __near *)0xF00B)

#define LTBADJ (*(volatile unsigned int __near *)0xF00C)

#define LTBADJL (*(volatile unsigned char __near *)0xF00C)
#define _B_LTBADJL (*(volatile _BYTE_FIELD __near *)0xF00C)

#define LTBADJH (*(volatile unsigned char __near *)0xF00D)
#define _B_LTBADJH (*(volatile _BYTE_FIELD __near *)0xF00D)

#define WDTCON (*(volatile unsigned char __near *)0xF00E)
#define _B_WDTCON (*(volatile _BYTE_FIELD __near *)0xF00E)

#define WDTMOD (*(volatile unsigned char __near *)0xF00F)
#define _B_WDTMOD (*(volatile _BYTE_FIELD __near *)0xF00F)

#define IE0 (*(volatile unsigned char __near *)0xF010)
#define _B_IE0 (*(volatile _BYTE_FIELD __near *)0xF010)

#define IE1 (*(volatile unsigned char __near *)0xF011)
#define _B_IE1 (*(volatile _BYTE_FIELD __near *)0xF011)

#define IE2 (*(volatile unsigned char __near *)0xF012)
#define _B_IE2 (*(volatile _BYTE_FIELD __near *)0xF012)

#define IE3 (*(volatile unsigned char __near *)0xF013)
#define _B_IE3 (*(volatile _BYTE_FIELD __near *)0xF013)

#define IE4 (*(volatile unsigned char __near *)0xF014)
#define _B_IE4 (*(volatile _BYTE_FIELD __near *)0xF014)

#define IE5 (*(volatile unsigned char __near *)0xF015)
#define _B_IE5 (*(volatile _BYTE_FIELD __near *)0xF015)

#define IE6 (*(volatile unsigned char __near *)0xF016)
#define _B_IE6 (*(volatile _BYTE_FIELD __near *)0xF016)

#define IE7 (*(volatile unsigned char __near *)0xF017)
#define _B_IE7 (*(volatile _BYTE_FIELD __near *)0xF017)

#define IRQ0 (*(volatile unsigned char __near *)0xF018)
#define _B_IRQ0 (*(volatile _BYTE_FIELD __near *)0xF018)

#define IRQ1 (*(volatile unsigned char __near *)0xF019)
#define _B_IRQ1 (*(volatile _BYTE_FIELD __near *)0xF019)

#define IRQ2 (*(volatile unsigned char __near *)0xF01A)
#define _B_IRQ2 (*(volatile _BYTE_FIELD __near *)0xF01A)

#define IRQ3 (*(volatile unsigned char __near *)0xF01B)
#define _B_IRQ3 (*(volatile _BYTE_FIELD __near *)0xF01B)

#define IRQ4 (*(volatile unsigned char __near *)0xF01C)
#define _B_IRQ4 (*(volatile _BYTE_FIELD __near *)0xF01C)

#define IRQ5 (*(volatile unsigned char __near *)0xF01D)
#define _B_IRQ5 (*(volatile _BYTE_FIELD __near *)0xF01D)

#define IRQ6 (*(volatile unsigned char __near *)0xF01E)
#define _B_IRQ6 (*(volatile _BYTE_FIELD __near *)0xF01E)

#define IRQ7 (*(volatile unsigned char __near *)0xF01F)
#define _B_IRQ7 (*(volatile _BYTE_FIELD __near *)0xF01F)

#define EXICON0 (*(volatile unsigned char __near *)0xF020)
#define _B_EXICON0 (*(volatile _BYTE_FIELD __near *)0xF020)

#define EXICON1 (*(volatile unsigned char __near *)0xF021)
#define _B_EXICON1 (*(volatile _BYTE_FIELD __near *)0xF021)

#define EXICON2 (*(volatile unsigned char __near *)0xF022)
#define _B_EXICON2 (*(volatile _BYTE_FIELD __near *)0xF022)

#define BLKCON0 (*(volatile unsigned char __near *)0xF028)
#define _B_BLKCON0 (*(volatile _BYTE_FIELD __near *)0xF028)

#define BLKCON2 (*(volatile unsigned char __near *)0xF02A)
#define _B_BLKCON2 (*(volatile _BYTE_FIELD __near *)0xF02A)

#define BLKCON4 (*(volatile unsigned char __near *)0xF02C)
#define _B_BLKCON4 (*(volatile _BYTE_FIELD __near *)0xF02C)

#define BLKCON6 (*(volatile unsigned char __near *)0xF02E)
#define _B_BLKCON6 (*(volatile _BYTE_FIELD __near *)0xF02E)

#define BLKCON7 (*(volatile unsigned char __near *)0xF02F)
#define _B_BLKCON7 (*(volatile _BYTE_FIELD __near *)0xF02F)

#define TM0DC (*(volatile unsigned int __near *)0xF030)

#define TM0D (*(volatile unsigned char __near *)0xF030)
#define _B_TM0D (*(volatile _BYTE_FIELD __near *)0xF030)

#define TM0C (*(volatile unsigned char __near *)0xF031)
#define _B_TM0C (*(volatile _BYTE_FIELD __near *)0xF031)

#define TM0CON (*(volatile unsigned int __near *)0xF032)

#define TM0CON0 (*(volatile unsigned char __near *)0xF032)
#define _B_TM0CON0 (*(volatile _BYTE_FIELD __near *)0xF032)

#define TM0CON1 (*(volatile unsigned char __near *)0xF033)
#define _B_TM0CON1 (*(volatile _BYTE_FIELD __near *)0xF033)

#define TM1DC (*(volatile unsigned int __near *)0xF034)

#define TM1D (*(volatile unsigned char __near *)0xF034)
#define _B_TM1D (*(volatile _BYTE_FIELD __near *)0xF034)

#define TM1C (*(volatile unsigned char __near *)0xF035)
#define _B_TM1C (*(volatile _BYTE_FIELD __near *)0xF035)

#define TM1CON (*(volatile unsigned int __near *)0xF036)

#define TM1CON0 (*(volatile unsigned char __near *)0xF036)
#define _B_TM1CON0 (*(volatile _BYTE_FIELD __near *)0xF036)

#define TM1CON1 (*(volatile unsigned char __near *)0xF037)
#define _B_TM1CON1 (*(volatile _BYTE_FIELD __near *)0xF037)

#define FSTAT (*(volatile unsigned char __near *)0xF070)
#define _B_FSTAT (*(volatile _BYTE_FIELD __near *)0xF070)

#define BLDCON (*(volatile unsigned int __near *)0xF0D0)

#define BLDCON0 (*(volatile unsigned char __near *)0xF0D0)
#define _B_BLDCON0 (*(volatile _BYTE_FIELD __near *)0xF0D0)

#define BLDCON1 (*(volatile unsigned char __near *)0xF0D1)
#define _B_BLDCON1 (*(volatile _BYTE_FIELD __near *)0xF0D1)

#define BIASCON (*(volatile unsigned char __near *)0xF0F0)
#define _B_BIASCON (*(volatile _BYTE_FIELD __near *)0xF0F0)

#define DSPMOD (*(volatile unsigned int __near *)0xF0F2)

#define DSPMOD0 (*(volatile unsigned char __near *)0xF0F2)
#define _B_DSPMOD0 (*(volatile _BYTE_FIELD __near *)0xF0F2)

#define DSPCON (*(volatile unsigned char __near *)0xF0F4)
#define _B_DSPCON (*(volatile _BYTE_FIELD __near *)0xF0F4)

#define DSPR00 (*(volatile unsigned char __near *)0xF100)

#define DSPR01 (*(volatile unsigned char __near *)0xF101)

#define DSPR02 (*(volatile unsigned char __near *)0xF102)

#define DSPR03 (*(volatile unsigned char __near *)0xF103)

#define DSPR04 (*(volatile unsigned char __near *)0xF104)

#define DSPR05 (*(volatile unsigned char __near *)0xF105)

#define DSPR06 (*(volatile unsigned char __near *)0xF106)

#define DSPR07 (*(volatile unsigned char __near *)0xF107)

#define DSPR08 (*(volatile unsigned char __near *)0xF108)

#define DSPR09 (*(volatile unsigned char __near *)0xF109)

#define DSPR0A (*(volatile unsigned char __near *)0xF10A)

#define DSPR0B (*(volatile unsigned char __near *)0xF10B)

#define DSPR0C (*(volatile unsigned char __near *)0xF10C)

#define DSPR0D (*(volatile unsigned char __near *)0xF10D)

#define DSPR0E (*(volatile unsigned char __near *)0xF10E)

#define DSPR0F (*(volatile unsigned char __near *)0xF10F)

#define DSPR10 (*(volatile unsigned char __near *)0xF110)

#define DSPR11 (*(volatile unsigned char __near *)0xF111)

#define DSPR12 (*(volatile unsigned char __near *)0xF112)

#define DSPR13 (*(volatile unsigned char __near *)0xF113)

#define DSPR14 (*(volatile unsigned char __near *)0xF114)

#define DSPR15 (*(volatile unsigned char __near *)0xF115)

#define DSPR16 (*(volatile unsigned char __near *)0xF116)

#define DSPR17 (*(volatile unsigned char __near *)0xF117)

#define DSPR18 (*(volatile unsigned char __near *)0xF118)

#define DSPR19 (*(volatile unsigned char __near *)0xF119)

#define DSPR1A (*(volatile unsigned char __near *)0xF11A)

#define DSPR1B (*(volatile unsigned char __near *)0xF11B)

#define DSPR1C (*(volatile unsigned char __near *)0xF11C)

#define DSPR1D (*(volatile unsigned char __near *)0xF11D)

#define DSPR1E (*(volatile unsigned char __near *)0xF11E)

#define DSPR1F (*(volatile unsigned char __near *)0xF11F)

#define DSPR20 (*(volatile unsigned char __near *)0xF120)

#define DSPR21 (*(volatile unsigned char __near *)0xF121)

#define DSPR22 (*(volatile unsigned char __near *)0xF122)

#define DSPR23 (*(volatile unsigned char __near *)0xF123)

#define DSPR24 (*(volatile unsigned char __near *)0xF124)

#define DSPR25 (*(volatile unsigned char __near *)0xF125)

#define DSPR26 (*(volatile unsigned char __near *)0xF126)

#define DSPR27 (*(volatile unsigned char __near *)0xF127)

#define NMID (*(volatile unsigned char __near *)0xF200)
#define _B_NMID (*(volatile _BYTE_FIELD __near *)0xF200)

#define NMICON (*(volatile unsigned char __near *)0xF201)
#define _B_NMICON (*(volatile _BYTE_FIELD __near *)0xF201)

#define P0D (*(volatile unsigned char __near *)0xF204)
#define _B_P0D (*(volatile _BYTE_FIELD __near *)0xF204)

#define P0CON (*(volatile unsigned int __near *)0xF206)

#define P0CON0 (*(volatile unsigned char __near *)0xF206)
#define _B_P0CON0 (*(volatile _BYTE_FIELD __near *)0xF206)

#define P0CON1 (*(volatile unsigned char __near *)0xF207)
#define _B_P0CON1 (*(volatile _BYTE_FIELD __near *)0xF207)

#define P1D (*(volatile unsigned char __near *)0xF208)
#define _B_P1D (*(volatile _BYTE_FIELD __near *)0xF208)

#define P1CON (*(volatile unsigned int __near *)0xF20A)

#define P1CON0 (*(volatile unsigned char __near *)0xF20A)
#define _B_P1CON0 (*(volatile _BYTE_FIELD __near *)0xF20A)

#define P1CON1 (*(volatile unsigned char __near *)0xF20B)
#define _B_P1CON1 (*(volatile _BYTE_FIELD __near *)0xF20B)

#define P2D (*(volatile unsigned char __near *)0xF210)
#define _B_P2D (*(volatile _BYTE_FIELD __near *)0xF210)

#define P2CON (*(volatile unsigned int __near *)0xF212)

#define P2CON0 (*(volatile unsigned char __near *)0xF212)
#define _B_P2CON0 (*(volatile _BYTE_FIELD __near *)0xF212)

#define P2CON1 (*(volatile unsigned char __near *)0xF213)
#define _B_P2CON1 (*(volatile _BYTE_FIELD __near *)0xF213)

#define P2MOD (*(volatile unsigned char __near *)0xF214)
#define _B_P2MOD (*(volatile _BYTE_FIELD __near *)0xF214)

#define P2MOD1 (*(volatile unsigned char __near *)0xF215)
#define _B_P2MOD1 (*(volatile _BYTE_FIELD __near *)0xF215)

#define P3D (*(volatile unsigned char __near *)0xF218)
#define _B_P3D (*(volatile _BYTE_FIELD __near *)0xF218)

#define P3DIR (*(volatile unsigned char __near *)0xF219)
#define _B_P3DIR (*(volatile _BYTE_FIELD __near *)0xF219)

#define P3CON (*(volatile unsigned int __near *)0xF21A)

#define P3CON0 (*(volatile unsigned char __near *)0xF21A)
#define _B_P3CON0 (*(volatile _BYTE_FIELD __near *)0xF21A)

#define P3CON1 (*(volatile unsigned char __near *)0xF21B)
#define _B_P3CON1 (*(volatile _BYTE_FIELD __near *)0xF21B)

#define P3MOD (*(volatile unsigned int __near *)0xF21C)

#define P3MOD0 (*(volatile unsigned char __near *)0xF21C)
#define _B_P3MOD0 (*(volatile _BYTE_FIELD __near *)0xF21C)

#define P3MOD1 (*(volatile unsigned char __near *)0xF21D)
#define _B_P3MOD1 (*(volatile _BYTE_FIELD __near *)0xF21D)

#define P4D (*(volatile unsigned char __near *)0xF220)
#define _B_P4D (*(volatile _BYTE_FIELD __near *)0xF220)

#define P4DIR (*(volatile unsigned char __near *)0xF221)
#define _B_P4DIR (*(volatile _BYTE_FIELD __near *)0xF221)

#define P4CON (*(volatile unsigned int __near *)0xF222)

#define P4CON0 (*(volatile unsigned char __near *)0xF222)
#define _B_P4CON0 (*(volatile _BYTE_FIELD __near *)0xF222)

#define P4CON1 (*(volatile unsigned char __near *)0xF223)
#define _B_P4CON1 (*(volatile _BYTE_FIELD __near *)0xF223)

#define P4MOD (*(volatile unsigned int __near *)0xF224)

#define P4MOD0 (*(volatile unsigned char __near *)0xF224)
#define _B_P4MOD0 (*(volatile _BYTE_FIELD __near *)0xF224)

#define P4MOD1 (*(volatile unsigned char __near *)0xF225)
#define _B_P4MOD1 (*(volatile _BYTE_FIELD __near *)0xF225)

#define P5D (*(volatile unsigned char __near *)0xF228)
#define _B_P5D (*(volatile _BYTE_FIELD __near *)0xF228)

#define P5DIR (*(volatile unsigned char __near *)0xF229)
#define _B_P5DIR (*(volatile _BYTE_FIELD __near *)0xF229)

#define P5CON (*(volatile unsigned int __near *)0xF22A)

#define P5CON0 (*(volatile unsigned char __near *)0xF22A)
#define _B_P5CON0 (*(volatile _BYTE_FIELD __near *)0xF22A)

#define P5CON1 (*(volatile unsigned char __near *)0xF22B)
#define _B_P5CON1 (*(volatile _BYTE_FIELD __near *)0xF22B)

#define P5MOD (*(volatile unsigned int __near *)0xF22C)

#define P5MOD0 (*(volatile unsigned char __near *)0xF22C)
#define _B_P5MOD0 (*(volatile _BYTE_FIELD __near *)0xF22C)

#define P5MOD1 (*(volatile unsigned char __near *)0xF22D)
#define _B_P5MOD1 (*(volatile _BYTE_FIELD __near *)0xF22D)

#define P6D (*(volatile unsigned char __near *)0xF230)
#define _B_P6D (*(volatile _BYTE_FIELD __near *)0xF230)

#define P6DIR (*(volatile unsigned char __near *)0xF231)
#define _B_P6DIR (*(volatile _BYTE_FIELD __near *)0xF231)

#define P6CON (*(volatile unsigned int __near *)0xF232)

#define P6CON0 (*(volatile unsigned char __near *)0xF232)
#define _B_P6CON0 (*(volatile _BYTE_FIELD __near *)0xF232)

#define P6CON1 (*(volatile unsigned char __near *)0xF233)
#define _B_P6CON1 (*(volatile _BYTE_FIELD __near *)0xF233)

#define P9D (*(volatile unsigned char __near *)0xF248)
#define _B_P9D (*(volatile _BYTE_FIELD __near *)0xF248)

#define P9CON (*(volatile unsigned int __near *)0xF24A)

#define P9CON0 (*(volatile unsigned char __near *)0xF24A)
#define _B_P9CON0 (*(volatile _BYTE_FIELD __near *)0xF24A)

#define P9CON1 (*(volatile unsigned char __near *)0xF24B)
#define _B_P9CON1 (*(volatile _BYTE_FIELD __near *)0xF24B)

#define PCD (*(volatile unsigned char __near *)0xF260)
#define _B_PCD (*(volatile _BYTE_FIELD __near *)0xF260)

#define PCDIR (*(volatile unsigned char __near *)0xF261)
#define _B_PCDIR (*(volatile _BYTE_FIELD __near *)0xF261)

#define PCCON (*(volatile unsigned int __near *)0xF262)

#define PCCON0 (*(volatile unsigned char __near *)0xF262)
#define _B_PCCON0 (*(volatile _BYTE_FIELD __near *)0xF262)

#define PCCON1 (*(volatile unsigned char __near *)0xF263)
#define _B_PCCON1 (*(volatile _BYTE_FIELD __near *)0xF263)

#define PDD (*(volatile unsigned char __near *)0xF268)
#define _B_PDD (*(volatile _BYTE_FIELD __near *)0xF268)

#define PDDIR (*(volatile unsigned char __near *)0xF269)
#define _B_PDDIR (*(volatile _BYTE_FIELD __near *)0xF269)

#define PDCON (*(volatile unsigned int __near *)0xF26A)

#define PDCON0 (*(volatile unsigned char __near *)0xF26A)
#define _B_PDCON0 (*(volatile _BYTE_FIELD __near *)0xF26A)

#define PDCON1 (*(volatile unsigned char __near *)0xF26B)
#define _B_PDCON1 (*(volatile _BYTE_FIELD __near *)0xF26B)

#define PED (*(volatile unsigned char __near *)0xF270)
#define _B_PED (*(volatile _BYTE_FIELD __near *)0xF270)

#define PEDIR (*(volatile unsigned char __near *)0xF271)
#define _B_PEDIR (*(volatile _BYTE_FIELD __near *)0xF271)

#define PECON (*(volatile unsigned int __near *)0xF272)

#define PECON0 (*(volatile unsigned char __near *)0xF272)
#define _B_PECON0 (*(volatile _BYTE_FIELD __near *)0xF272)

#define PECON1 (*(volatile unsigned char __near *)0xF273)
#define _B_PECON1 (*(volatile _BYTE_FIELD __near *)0xF273)

#define PFD (*(volatile unsigned char __near *)0xF278)
#define _B_PFD (*(volatile _BYTE_FIELD __near *)0xF278)

#define PFDIR (*(volatile unsigned char __near *)0xF279)
#define _B_PFDIR (*(volatile _BYTE_FIELD __near *)0xF279)

#define PFCON (*(volatile unsigned int __near *)0xF27A)

#define PFCON0 (*(volatile unsigned char __near *)0xF27A)
#define _B_PFCON0 (*(volatile _BYTE_FIELD __near *)0xF27A)

#define PFCON1 (*(volatile unsigned char __near *)0xF27B)
#define _B_PFCON1 (*(volatile _BYTE_FIELD __near *)0xF27B)

#define SIO0BUF (*(volatile unsigned int __near *)0xF280)

#define SIO0BUFL (*(volatile unsigned char __near *)0xF280)
#define _B_SIO0BUFL (*(volatile _BYTE_FIELD __near *)0xF280)

#define SIO0BUFH (*(volatile unsigned char __near *)0xF281)
#define _B_SIO0BUFH (*(volatile _BYTE_FIELD __near *)0xF281)

#define SIO0CON (*(volatile unsigned char __near *)0xF282)
#define _B_SIO0CON (*(volatile _BYTE_FIELD __near *)0xF282)

#define SIO0MOD (*(volatile unsigned int __near *)0xF284)

#define SIO0MOD0 (*(volatile unsigned char __near *)0xF284)
#define _B_SIO0MOD0 (*(volatile _BYTE_FIELD __near *)0xF284)

#define SIO0MOD1 (*(volatile unsigned char __near *)0xF285)
#define _B_SIO0MOD1 (*(volatile _BYTE_FIELD __near *)0xF285)

#define SIO1BUF (*(volatile unsigned int __near *)0xF288)

#define SIO1BUFL (*(volatile unsigned char __near *)0xF288)
#define _B_SIO1BUFL (*(volatile _BYTE_FIELD __near *)0xF288)

#define SIO1BUFH (*(volatile unsigned char __near *)0xF289)
#define _B_SIO1BUFH (*(volatile _BYTE_FIELD __near *)0xF289)

#define SIO1CON (*(volatile unsigned char __near *)0xF28A)
#define _B_SIO1CON (*(volatile _BYTE_FIELD __near *)0xF28A)

#define SIO1MOD (*(volatile unsigned int __near *)0xF28C)

#define SIO1MOD0 (*(volatile unsigned char __near *)0xF28C)
#define _B_SIO1MOD0 (*(volatile _BYTE_FIELD __near *)0xF28C)

#define SIO1MOD1 (*(volatile unsigned char __near *)0xF28D)
#define _B_SIO1MOD1 (*(volatile _BYTE_FIELD __near *)0xF28D)

#define UA0BUF (*(volatile unsigned char __near *)0xF290)
#define _B_UA0BUF (*(volatile _BYTE_FIELD __near *)0xF290)

#define UA0CON (*(volatile unsigned char __near *)0xF291)
#define _B_UA0CON (*(volatile _BYTE_FIELD __near *)0xF291)

#define UA0MOD (*(volatile unsigned int __near *)0xF292)

#define UA0MOD0 (*(volatile unsigned char __near *)0xF292)
#define _B_UA0MOD0 (*(volatile _BYTE_FIELD __near *)0xF292)

#define UA0MOD1 (*(volatile unsigned char __near *)0xF293)
#define _B_UA0MOD1 (*(volatile _BYTE_FIELD __near *)0xF293)

#define UA0BRT (*(volatile unsigned int __near *)0xF294)

#define UA0BRTL (*(volatile unsigned char __near *)0xF294)
#define _B_UA0BRTL (*(volatile _BYTE_FIELD __near *)0xF294)

#define UA0BRTH (*(volatile unsigned char __near *)0xF295)
#define _B_UA0BRTH (*(volatile _BYTE_FIELD __near *)0xF295)

#define UA0STAT (*(volatile unsigned char __near *)0xF296)
#define _B_UA0STAT (*(volatile _BYTE_FIELD __near *)0xF296)

#define UA1BUF (*(volatile unsigned char __near *)0xF298)
#define _B_UA1BUF (*(volatile _BYTE_FIELD __near *)0xF298)

#define UA1CON (*(volatile unsigned char __near *)0xF299)
#define _B_UA1CON (*(volatile _BYTE_FIELD __near *)0xF299)

#define UA1MOD (*(volatile unsigned int __near *)0xF29A)

#define UA1MOD0 (*(volatile unsigned char __near *)0xF29A)
#define _B_UA1MOD0 (*(volatile _BYTE_FIELD __near *)0xF29A)

#define UA1MOD1 (*(volatile unsigned char __near *)0xF29B)
#define _B_UA1MOD1 (*(volatile _BYTE_FIELD __near *)0xF29B)

#define UA1BRT (*(volatile unsigned int __near *)0xF29C)

#define UA1BRTL (*(volatile unsigned char __near *)0xF29C)
#define _B_UA1BRTL (*(volatile _BYTE_FIELD __near *)0xF29C)

#define UA1BRTH (*(volatile unsigned char __near *)0xF29D)
#define _B_UA1BRTH (*(volatile _BYTE_FIELD __near *)0xF29D)

#define UA1STAT (*(volatile unsigned char __near *)0xF29E)
#define _B_UA1STAT (*(volatile _BYTE_FIELD __near *)0xF29E)

#define I2C0RD (*(volatile unsigned char __near *)0xF2A0)
#define _B_I2C0RD (*(volatile _BYTE_FIELD __near *)0xF2A0)

#define I2C0SA (*(volatile unsigned char __near *)0xF2A1)
#define _B_I2C0SA (*(volatile _BYTE_FIELD __near *)0xF2A1)

#define I2C0TD (*(volatile unsigned char __near *)0xF2A2)
#define _B_I2C0TD (*(volatile _BYTE_FIELD __near *)0xF2A2)

#define I2C0CON (*(volatile unsigned char __near *)0xF2A3)
#define _B_I2C0CON (*(volatile _BYTE_FIELD __near *)0xF2A3)

#define I2C0MOD (*(volatile unsigned char __near *)0xF2A4)
#define _B_I2C0MOD (*(volatile _BYTE_FIELD __near *)0xF2A4)

#define I2C0STAT (*(volatile unsigned char __near *)0xF2A5)
#define _B_I2C0STAT (*(volatile _BYTE_FIELD __near *)0xF2A5)

#define SADR0 (*(volatile unsigned int __near *)0xF2D0)

#define SADR0L (*(volatile unsigned char __near *)0xF2D0)
#define _B_SADR0L (*(volatile _BYTE_FIELD __near *)0xF2D0)

#define SADR0H (*(volatile unsigned char __near *)0xF2D1)
#define _B_SADR0H (*(volatile _BYTE_FIELD __near *)0xF2D1)

#define SADR1 (*(volatile unsigned int __near *)0xF2D2)

#define SADR1L (*(volatile unsigned char __near *)0xF2D2)
#define _B_SADR1L (*(volatile _BYTE_FIELD __near *)0xF2D2)

#define SADR1H (*(volatile unsigned char __near *)0xF2D3)
#define _B_SADR1H (*(volatile _BYTE_FIELD __near *)0xF2D3)

#define SADR2 (*(volatile unsigned int __near *)0xF2D4)

#define SADR2L (*(volatile unsigned char __near *)0xF2D4)
#define _B_SADR2L (*(volatile _BYTE_FIELD __near *)0xF2D4)

#define SADR2H (*(volatile unsigned char __near *)0xF2D5)
#define _B_SADR2H (*(volatile _BYTE_FIELD __near *)0xF2D5)

#define SADR3 (*(volatile unsigned int __near *)0xF2D6)

#define SADR3L (*(volatile unsigned char __near *)0xF2D6)
#define _B_SADR3L (*(volatile _BYTE_FIELD __near *)0xF2D6)

#define SADR3H (*(volatile unsigned char __near *)0xF2D7)
#define _B_SADR3H (*(volatile _BYTE_FIELD __near *)0xF2D7)

#define SADR4 (*(volatile unsigned int __near *)0xF2D8)

#define SADR4L (*(volatile unsigned char __near *)0xF2D8)
#define _B_SADR4L (*(volatile _BYTE_FIELD __near *)0xF2D8)

#define SADR4H (*(volatile unsigned char __near *)0xF2D9)
#define _B_SADR4H (*(volatile _BYTE_FIELD __near *)0xF2D9)

#define SADR5 (*(volatile unsigned int __near *)0xF2DA)

#define SADR5L (*(volatile unsigned char __near *)0xF2DA)
#define _B_SADR5L (*(volatile _BYTE_FIELD __near *)0xF2DA)

#define SADR5H (*(volatile unsigned char __near *)0xF2DB)
#define _B_SADR5H (*(volatile _BYTE_FIELD __near *)0xF2DB)

#define SADR6 (*(volatile unsigned int __near *)0xF2DC)

#define SADR6L (*(volatile unsigned char __near *)0xF2DC)
#define _B_SADR6L (*(volatile _BYTE_FIELD __near *)0xF2DC)

#define SADR6H (*(volatile unsigned char __near *)0xF2DD)
#define _B_SADR6H (*(volatile _BYTE_FIELD __near *)0xF2DD)

#define SADR7 (*(volatile unsigned int __near *)0xF2DE)

#define SADR7L (*(volatile unsigned char __near *)0xF2DE)
#define _B_SADR7L (*(volatile _BYTE_FIELD __near *)0xF2DE)

#define SADR7H (*(volatile unsigned char __near *)0xF2DF)
#define _B_SADR7H (*(volatile _BYTE_FIELD __near *)0xF2DF)

#define SADR8 (*(volatile unsigned int __near *)0xF2E0)

#define SADR8L (*(volatile unsigned char __near *)0xF2E0)
#define _B_SADR8L (*(volatile _BYTE_FIELD __near *)0xF2E0)

#define SADR8H (*(volatile unsigned char __near *)0xF2E1)
#define _B_SADR8H (*(volatile _BYTE_FIELD __near *)0xF2E1)

#define SADR9 (*(volatile unsigned int __near *)0xF2E2)

#define SADR9L (*(volatile unsigned char __near *)0xF2E2)
#define _B_SADR9L (*(volatile _BYTE_FIELD __near *)0xF2E2)

#define SADR9H (*(volatile unsigned char __near *)0xF2E3)
#define _B_SADR9H (*(volatile _BYTE_FIELD __near *)0xF2E3)

#define SADRA (*(volatile unsigned int __near *)0xF2E4)

#define SADRAL (*(volatile unsigned char __near *)0xF2E4)
#define _B_SADRAL (*(volatile _BYTE_FIELD __near *)0xF2E4)

#define SADRAH (*(volatile unsigned char __near *)0xF2E5)
#define _B_SADRAH (*(volatile _BYTE_FIELD __near *)0xF2E5)

#define SADRB (*(volatile unsigned int __near *)0xF2E6)

#define SADRBL (*(volatile unsigned char __near *)0xF2E6)
#define _B_SADRBL (*(volatile _BYTE_FIELD __near *)0xF2E6)

#define SADRBH (*(volatile unsigned char __near *)0xF2E7)
#define _B_SADRBH (*(volatile _BYTE_FIELD __near *)0xF2E7)

#define SADRC (*(volatile unsigned int __near *)0xF2E8)

#define SADRCL (*(volatile unsigned char __near *)0xF2E8)
#define _B_SADRCL (*(volatile _BYTE_FIELD __near *)0xF2E8)

#define SADRCH (*(volatile unsigned char __near *)0xF2E9)
#define _B_SADRCH (*(volatile _BYTE_FIELD __near *)0xF2E9)

#define SADRD (*(volatile unsigned int __near *)0xF2EA)

#define SADRDL (*(volatile unsigned char __near *)0xF2EA)
#define _B_SADRDL (*(volatile _BYTE_FIELD __near *)0xF2EA)

#define SADRDH (*(volatile unsigned char __near *)0xF2EB)
#define _B_SADRDH (*(volatile _BYTE_FIELD __near *)0xF2EB)

#define SADRE (*(volatile unsigned int __near *)0xF2EC)

#define SADREL (*(volatile unsigned char __near *)0xF2EC)
#define _B_SADREL (*(volatile _BYTE_FIELD __near *)0xF2EC)

#define SADREH (*(volatile unsigned char __near *)0xF2ED)
#define _B_SADREH (*(volatile _BYTE_FIELD __near *)0xF2ED)

#define SADRF (*(volatile unsigned int __near *)0xF2EE)

#define SADRFL (*(volatile unsigned char __near *)0xF2EE)
#define _B_SADRFL (*(volatile _BYTE_FIELD __near *)0xF2EE)

#define SADRFH (*(volatile unsigned char __near *)0xF2EF)
#define _B_SADRFH (*(volatile _BYTE_FIELD __near *)0xF2EF)

#define SADCON (*(volatile unsigned int __near *)0xF2F0)

#define SADCON0 (*(volatile unsigned char __near *)0xF2F0)
#define _B_SADCON0 (*(volatile _BYTE_FIELD __near *)0xF2F0)

#define SADCON1 (*(volatile unsigned char __near *)0xF2F1)
#define _B_SADCON1 (*(volatile _BYTE_FIELD __near *)0xF2F1)

#define SADMOD (*(volatile unsigned int __near *)0xF2F2)

#define SADMOD0 (*(volatile unsigned char __near *)0xF2F2)
#define _B_SADMOD0 (*(volatile _BYTE_FIELD __near *)0xF2F2)

#define SADMOD1 (*(volatile unsigned char __near *)0xF2F3)
#define _B_SADMOD1 (*(volatile _BYTE_FIELD __near *)0xF2F3)

#define CODEOP0 (*(volatile unsigned char __near *)0xF3D8)
#define _B_CODEOP0 (*(volatile _BYTE_FIELD __near *)0xF3D8)

#define PW4P (*(volatile unsigned int __near *)0xF8A0)

#define PW4PL (*(volatile unsigned char __near *)0xF8A0)
#define _B_PW4PL (*(volatile _BYTE_FIELD __near *)0xF8A0)

#define PW4PH (*(volatile unsigned char __near *)0xF8A1)
#define _B_PW4PH (*(volatile _BYTE_FIELD __near *)0xF8A1)

#define PW4D (*(volatile unsigned int __near *)0xF8A2)

#define PW4DL (*(volatile unsigned char __near *)0xF8A2)
#define _B_PW4DL (*(volatile _BYTE_FIELD __near *)0xF8A2)

#define PW4DH (*(volatile unsigned char __near *)0xF8A3)
#define _B_PW4DH (*(volatile _BYTE_FIELD __near *)0xF8A3)

#define PW4C (*(volatile unsigned int __near *)0xF8A4)

#define PW4CL (*(volatile unsigned char __near *)0xF8A4)
#define _B_PW4CL (*(volatile _BYTE_FIELD __near *)0xF8A4)

#define PW4CH (*(volatile unsigned char __near *)0xF8A5)
#define _B_PW4CH (*(volatile _BYTE_FIELD __near *)0xF8A5)

#define PW4CON (*(volatile unsigned int __near *)0xF8A6)

#define PW4CON0 (*(volatile unsigned char __near *)0xF8A6)
#define _B_PW4CON0 (*(volatile _BYTE_FIELD __near *)0xF8A6)

#define PW4CON1 (*(volatile unsigned char __near *)0xF8A7)
#define _B_PW4CON1 (*(volatile _BYTE_FIELD __near *)0xF8A7)

#define PW4CON2 (*(volatile unsigned char __near *)0xF8A8)
#define _B_PW4CON2 (*(volatile _BYTE_FIELD __near *)0xF8A8)

#define PW4CON3 (*(volatile unsigned char __near *)0xF8A9)
#define _B_PW4CON3 (*(volatile _BYTE_FIELD __near *)0xF8A9)

#define PW5P (*(volatile unsigned int __near *)0xF8B0)

#define PW5PL (*(volatile unsigned char __near *)0xF8B0)
#define _B_PW5PL (*(volatile _BYTE_FIELD __near *)0xF8B0)

#define PW5PH (*(volatile unsigned char __near *)0xF8B1)
#define _B_PW5PH (*(volatile _BYTE_FIELD __near *)0xF8B1)

#define PW5D (*(volatile unsigned int __near *)0xF8B2)

#define PW5DL (*(volatile unsigned char __near *)0xF8B2)
#define _B_PW5DL (*(volatile _BYTE_FIELD __near *)0xF8B2)

#define PW5DH (*(volatile unsigned char __near *)0xF8B3)
#define _B_PW5DH (*(volatile _BYTE_FIELD __near *)0xF8B3)

#define PW5C (*(volatile unsigned int __near *)0xF8B4)

#define PW5CL (*(volatile unsigned char __near *)0xF8B4)
#define _B_PW5CL (*(volatile _BYTE_FIELD __near *)0xF8B4)

#define PW5CH (*(volatile unsigned char __near *)0xF8B5)
#define _B_PW5CH (*(volatile _BYTE_FIELD __near *)0xF8B5)

#define PW5CON (*(volatile unsigned int __near *)0xF8B6)

#define PW5CON0 (*(volatile unsigned char __near *)0xF8B6)
#define _B_PW5CON0 (*(volatile _BYTE_FIELD __near *)0xF8B6)

#define PW5CON1 (*(volatile unsigned char __near *)0xF8B7)
#define _B_PW5CON1 (*(volatile _BYTE_FIELD __near *)0xF8B7)

#define PW5CON2 (*(volatile unsigned char __near *)0xF8B8)
#define _B_PW5CON2 (*(volatile _BYTE_FIELD __near *)0xF8B8)

#define TM8DC (*(volatile unsigned int __near *)0xF8E0)

#define TM8D (*(volatile unsigned char __near *)0xF8E0)
#define _B_TM8D (*(volatile _BYTE_FIELD __near *)0xF8E0)

#define TM8C (*(volatile unsigned char __near *)0xF8E1)
#define _B_TM8C (*(volatile _BYTE_FIELD __near *)0xF8E1)

#define TM8CON (*(volatile unsigned int __near *)0xF8E2)

#define TM8CON0 (*(volatile unsigned char __near *)0xF8E2)
#define _B_TM8CON0 (*(volatile _BYTE_FIELD __near *)0xF8E2)

#define TM8CON1 (*(volatile unsigned char __near *)0xF8E3)
#define _B_TM8CON1 (*(volatile _BYTE_FIELD __near *)0xF8E3)

#define TM9DC (*(volatile unsigned int __near *)0xF8E4)

#define TM9D (*(volatile unsigned char __near *)0xF8E4)
#define _B_TM9D (*(volatile _BYTE_FIELD __near *)0xF8E4)

#define TM9C (*(volatile unsigned char __near *)0xF8E5)
#define _B_TM9C (*(volatile _BYTE_FIELD __near *)0xF8E5)

#define TM9CON (*(volatile unsigned int __near *)0xF8E6)

#define TM9CON0 (*(volatile unsigned char __near *)0xF8E6)
#define _B_TM9CON0 (*(volatile _BYTE_FIELD __near *)0xF8E6)

#define TM9CON1 (*(volatile unsigned char __near *)0xF8E7)
#define _B_TM9CON1 (*(volatile _BYTE_FIELD __near *)0xF8E7)

#define TMADC (*(volatile unsigned int __near *)0xF8E8)

#define TMAD (*(volatile unsigned char __near *)0xF8E8)
#define _B_TMAD (*(volatile _BYTE_FIELD __near *)0xF8E8)

#define TMAC (*(volatile unsigned char __near *)0xF8E9)
#define _B_TMAC (*(volatile _BYTE_FIELD __near *)0xF8E9)

#define TMACON (*(volatile unsigned int __near *)0xF8EA)

#define TMACON0 (*(volatile unsigned char __near *)0xF8EA)
#define _B_TMACON0 (*(volatile _BYTE_FIELD __near *)0xF8EA)

#define TMACON1 (*(volatile unsigned char __near *)0xF8EB)
#define _B_TMACON1 (*(volatile _BYTE_FIELD __near *)0xF8EB)

#define TMBDC (*(volatile unsigned int __near *)0xF8EC)

#define TMBD (*(volatile unsigned char __near *)0xF8EC)
#define _B_TMBD (*(volatile _BYTE_FIELD __near *)0xF8EC)

#define TMBC (*(volatile unsigned char __near *)0xF8ED)
#define _B_TMBC (*(volatile _BYTE_FIELD __near *)0xF8ED)

#define TMBCON (*(volatile unsigned int __near *)0xF8EE)

#define TMBCON0 (*(volatile unsigned char __near *)0xF8EE)
#define _B_TMBCON0 (*(volatile _BYTE_FIELD __near *)0xF8EE)

#define TMBCON1 (*(volatile unsigned char __near *)0xF8EF)
#define _B_TMBCON1 (*(volatile _BYTE_FIELD __near *)0xF8EF)

#define LSELS1 (*(volatile unsigned char __near *)0xF8F1)
#define _B_LSELS1 (*(volatile _BYTE_FIELD __near *)0xF8F1)

#define LSELS2 (*(volatile unsigned char __near *)0xF8F2)
#define _B_LSELS2 (*(volatile _BYTE_FIELD __near *)0xF8F2)

#define LSELS3 (*(volatile unsigned char __near *)0xF8F3)
#define _B_LSELS3 (*(volatile _BYTE_FIELD __near *)0xF8F3)

#define LSELS4 (*(volatile unsigned char __near *)0xF8F4)
#define _B_LSELS4 (*(volatile _BYTE_FIELD __near *)0xF8F4)

/*---------------------------------------------------
	END OF DATA ADDRESS SYMBOLS
---------------------------------------------------*/
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
